EmS228/jumpguard/presentations/FDR_13Jump.pdf

# JumpGuard Final Design Review

Team Members:
Riley Holmes (CpE)
Emily Schwartz (CpE)
Ben Caba (EE)
Trevor Jordan (ME)
John Podgorney (ME)

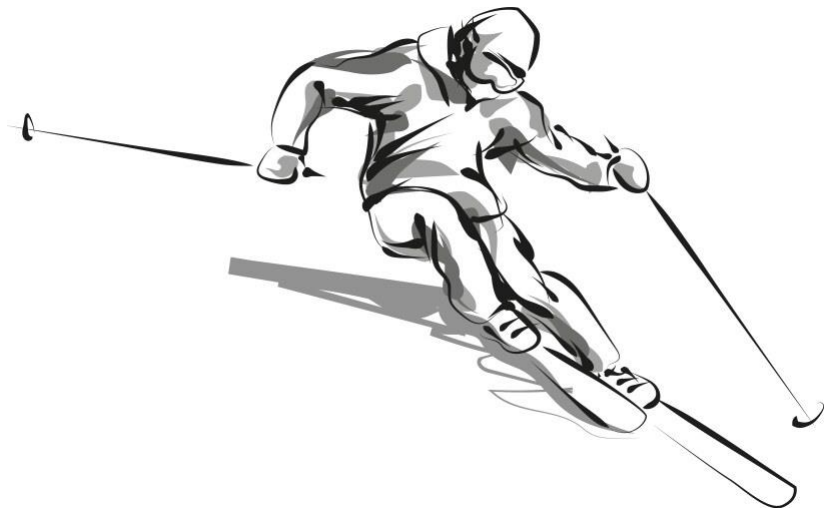
[picture p16: figure]

Clients: Nick Hekker, Kade Borson, Tate Ellinwood, Tristan Tober Advisor: Dr. Kevin Repasky
Date: 4/15/2025

# Problem Statement

Problem Motivation:
Many ski resorts today have terrain parks, which are collections of jumps and obstacles that can be ridden by athletes. Depending on the size of terrain park jumps, athletes can't always see the landing area before committing to the jump. So, if an athlete crashes on the bottom of a larger jump, athletes uphill may not be aware of the risk of collision awaiting them at the bottom of the jump.

Project Description:
A system will be designed to detect when the landing area is clear before notifying the next athlete that it is safe to proceed from the top of the hill.

Objectives:
This system will determine whether the landing area below a jump is clear and then report the status to athletes uphill from the landing area. The system must operate in inclement weather throughout the ski-season. The system will operate on a stand-alone power system to avoid running power lines to the system, which could create unnecessary hazards.

# Necessary Background

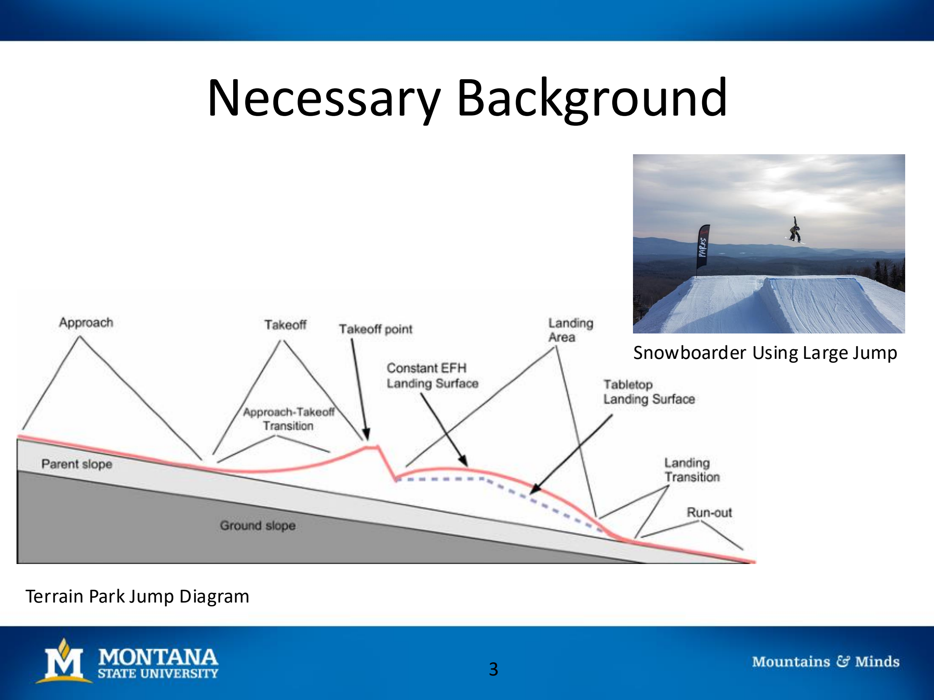
[picture p17: page 3]

Terrain Park Jump Diagram

Snowboarder Using Large Jump

# Project Design Concept

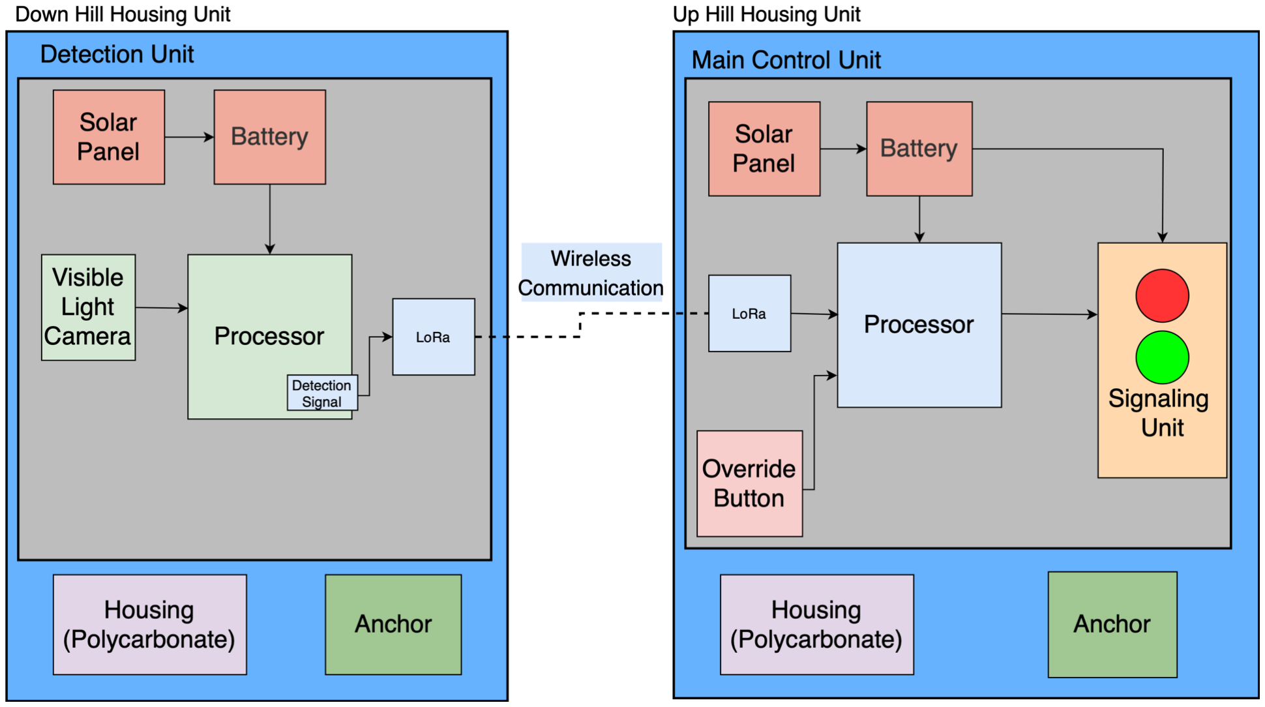
[picture p18: figure]

Conceptual Block Diagram

# System Design Solution

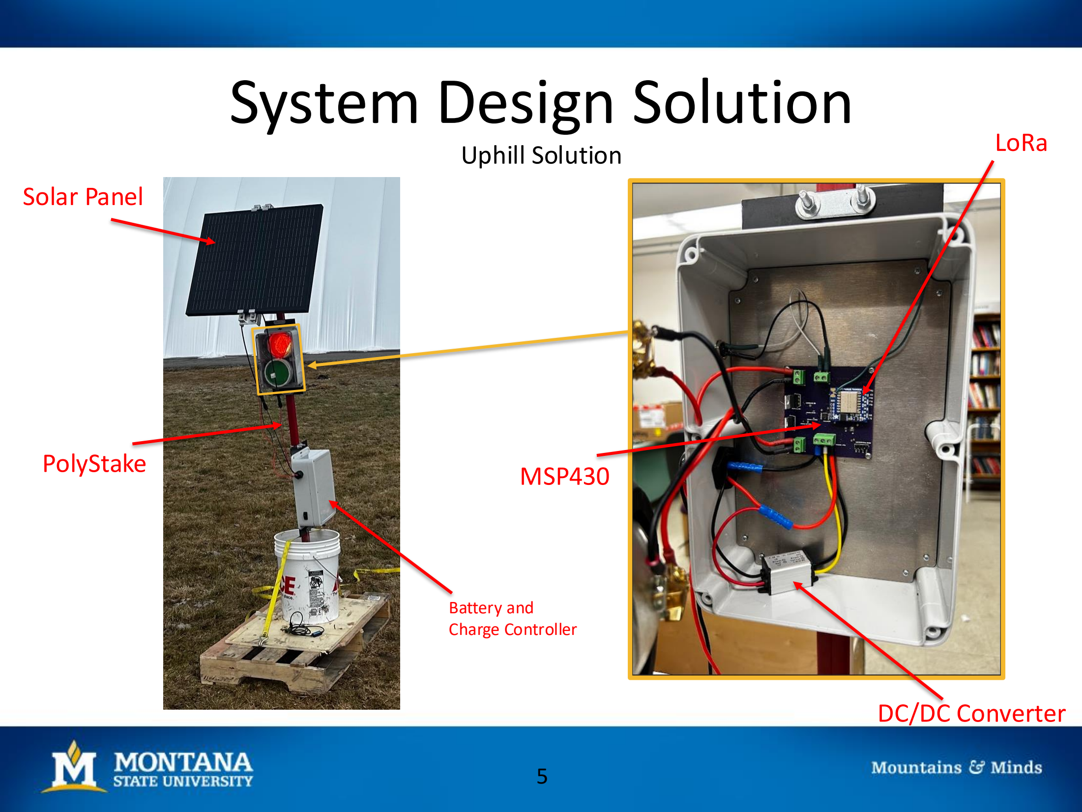
[picture p19: page 5]

Uphill Solution
Solar Panel

Battery and
Charge Controller

PolyStake

LoRa

MSP430

DC/DC Converter

# System Design Solution

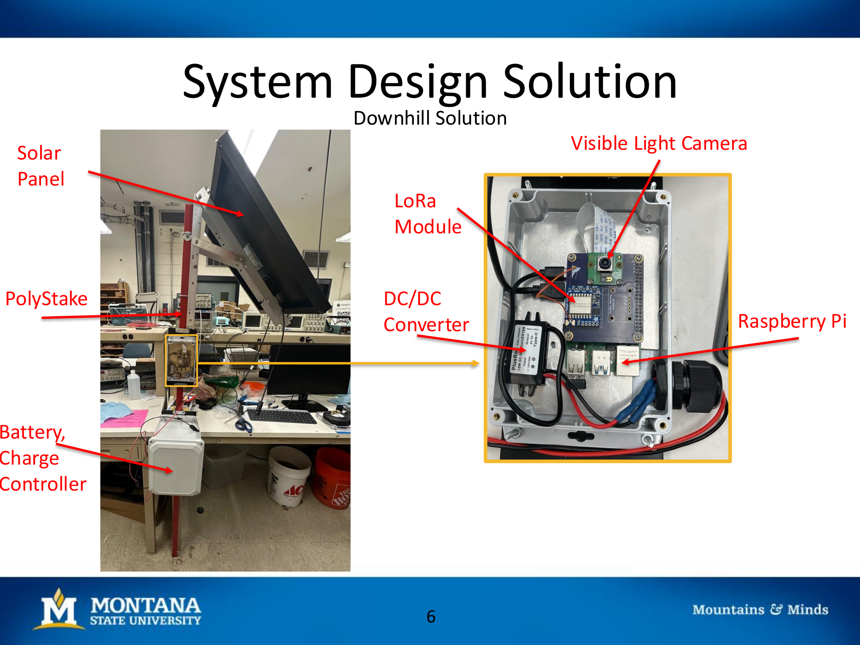
[picture p20: page 6]

Downhill Solution

Battery,
Charge
Controller

Solar
Panel
PolyStake | DC/DC Converter

Visible Light Camera

Raspberry Pi

LoRa
Module

# Design Solution: Uphill Power

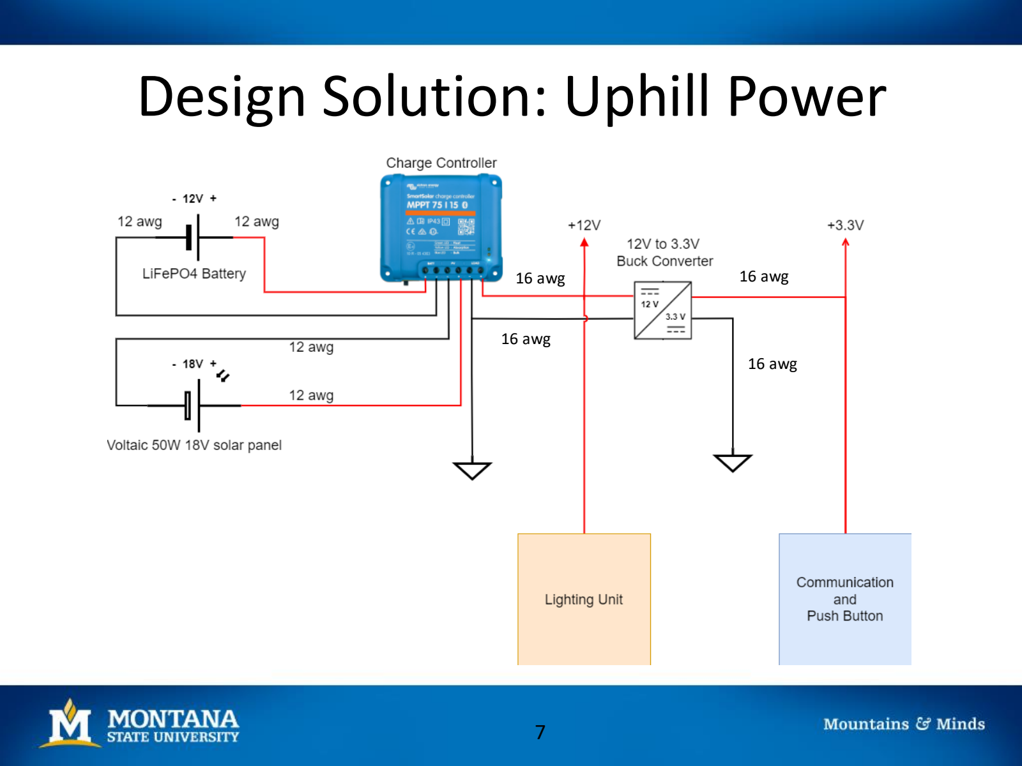
[picture p21: page 7]

16 awg

16 awg

16 awg

16 awg

# Design Solution: Uphill Power

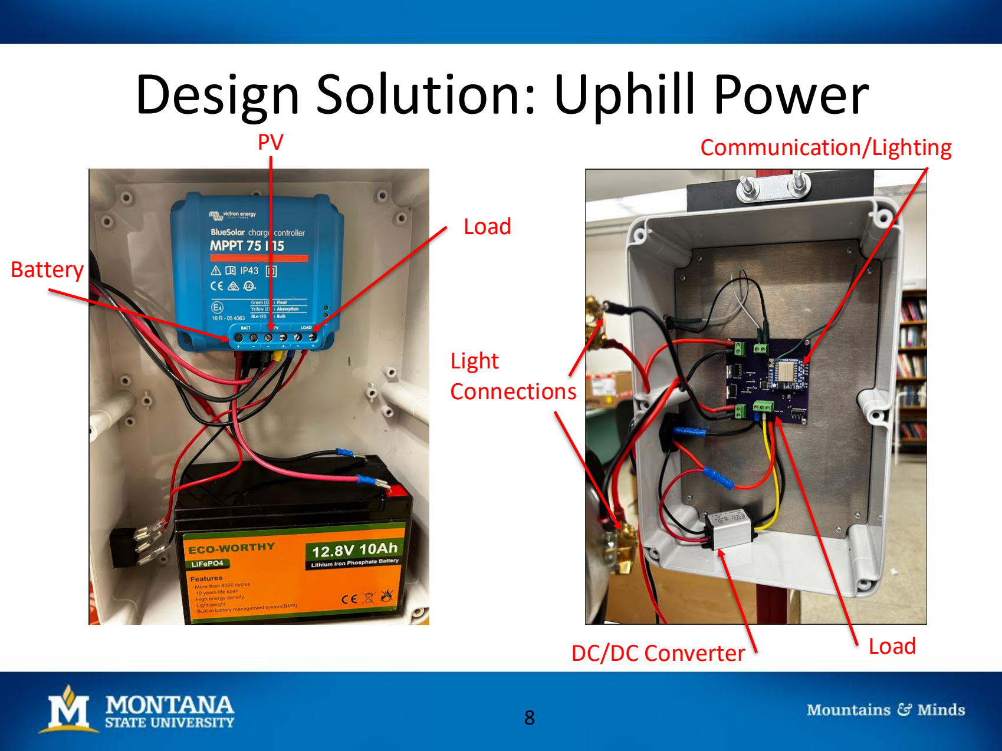
[picture p22: page 8]

Battery

PV

Load

Load

Light
Connections

DC/DC Converter

Communication/Lighting

# System Verification: Power (Spec 3.2.1 – test description)

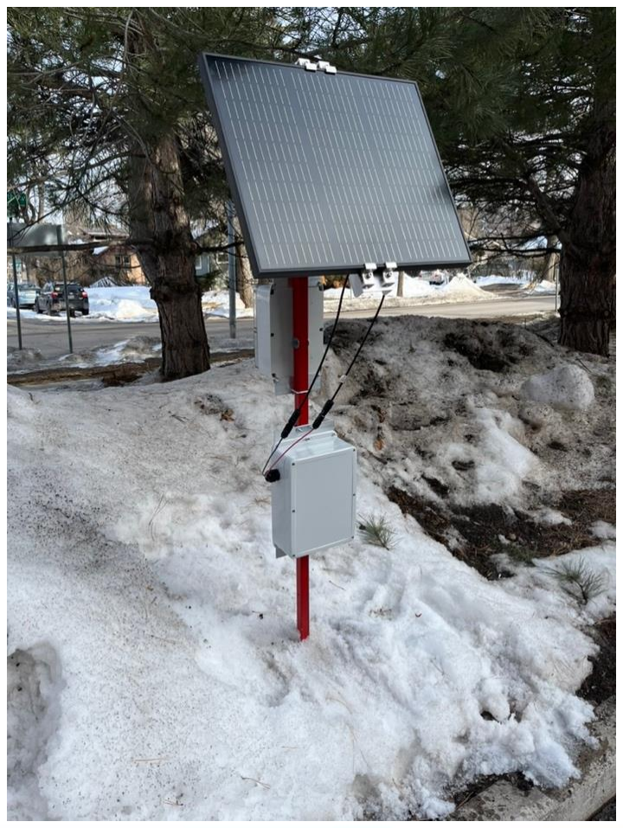
[picture p23: figure]

- Full system assembled
- Run off backup power for one day
- Run with solar panels for one day
- Run off backup power for one day

Spec 3.2.1) Can recharge for a 7-hour operational day with 3.5 hours of peak sunlight

# System Verification: Power (Spec 3.2.1 – test results)

Spec 3.2.1) Can recharge for a 7-hour operational day with 3.5 hours of peak sunlight

Date (mm/dd/yyyy) | Consumption (Wh) | Yield (Wh) | Initial Voltage (V) | Final Voltage (V)
04/09/2024 | 80 | 0 | 13.27 | 13.12
04/10/2024 | 70 | 160 | 13.14 | 13.42
04/11/2024 | 80 | 0 | 13.29* | 13.00

Uphill test results (04/09 – 04/11)

*system was used for additional testing after the 7 hour testing window

# System Verification: Power (Spec 3.2.1 – test results)

Spec 3.2.1) Can recharge for a 7-hour operational day with 3.5 hours of peak sunlight

Solar irradiance data for 04/10/2024 [1]

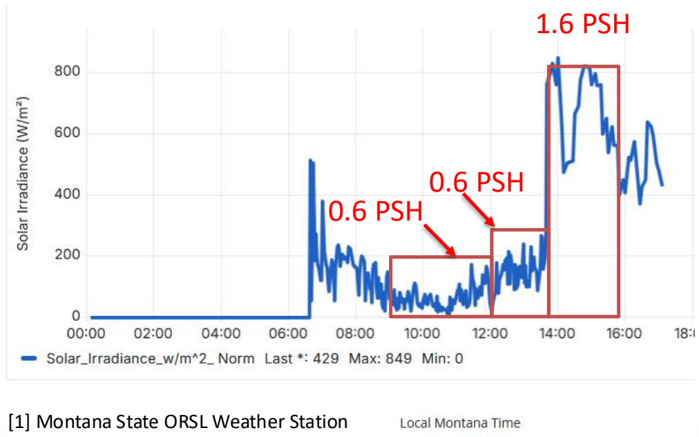
[picture p24: figure]
0.6 PSH; 1.6 PSH; [1] Montana State ORSL Weather Station

PSH for 4/10/2025 =
0.6 + 0.6 + 1.6 = ~2.8 PSH

Testing window: 8:56am-4:00pm

# System Verification: Power (summary)

Req Doc Item | Result | Pass/Fail
Req 3.1 | System operated continuously for 7 operational days | Pass
Spec 3.1.1 | System operated continuously for a 7-hour operational day | Pass
Spec 3.1.2 | Backup power operated for 7 hours | Pass
Req 3.2 | Solar and battery charger both charged the system | Pass
Spec 3.2.1 | Recharged with under 2.8 PSH | Pass
Spec 3.2.2 | Battery charger charged battery under 8 hours | Pass

# Design Solution: Communication

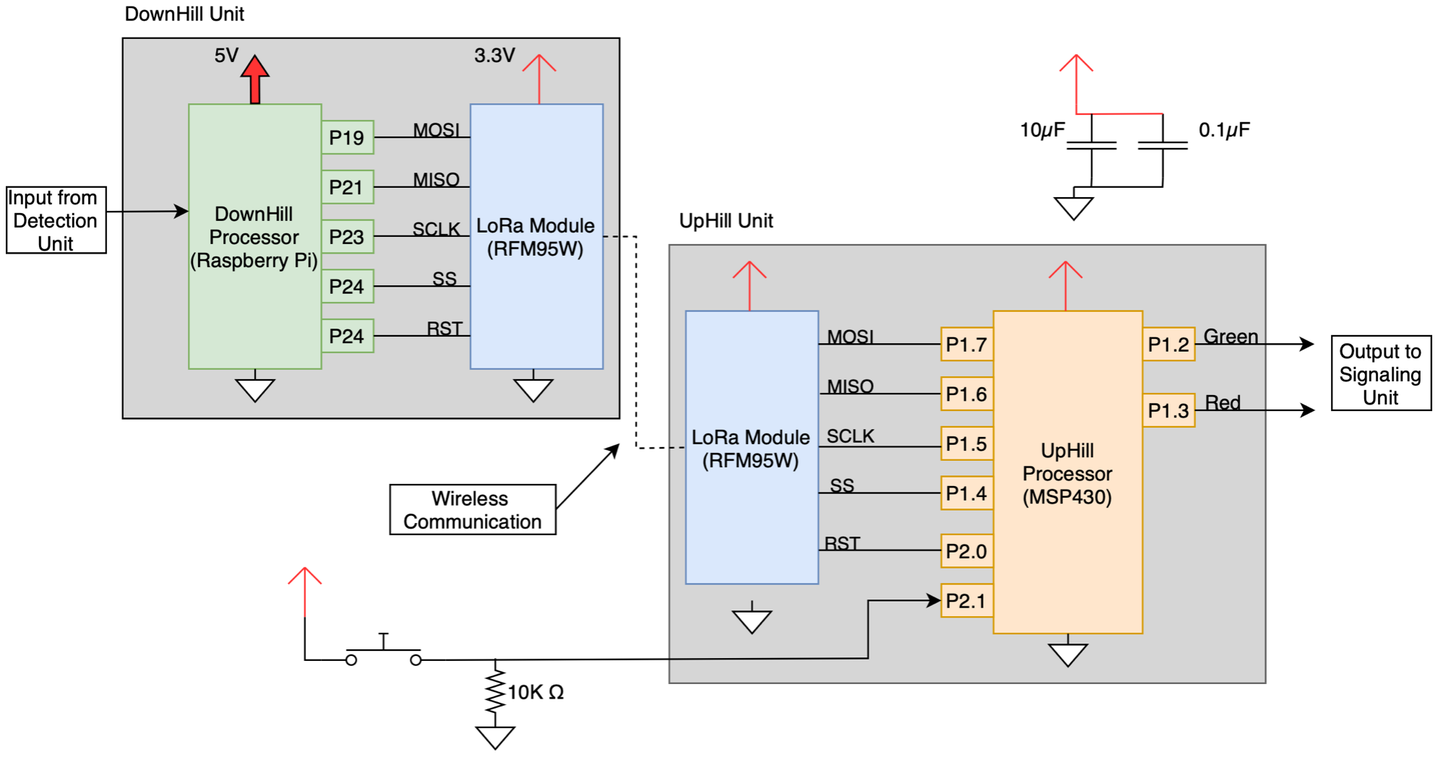
[picture p25: figure]

# System Verification: Communication Setup

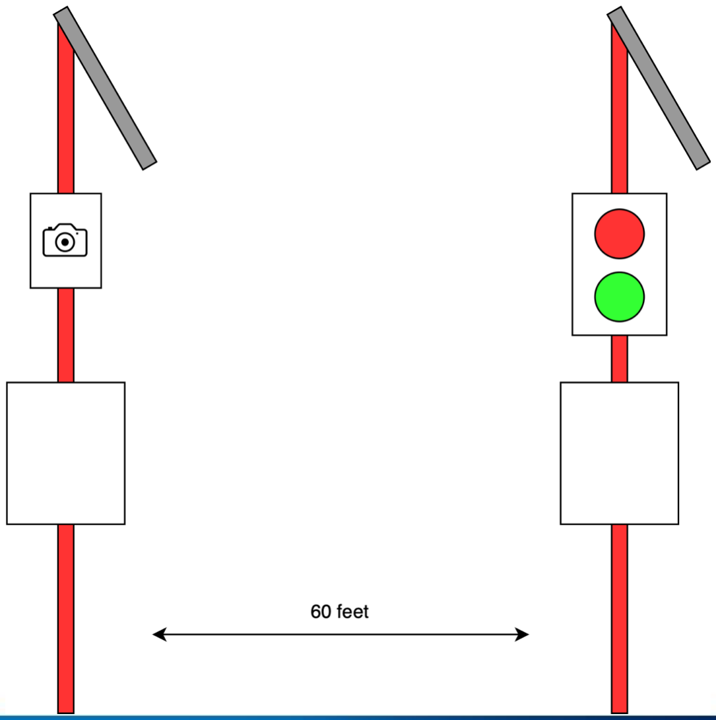
[picture p26: figure]

Req 1.2) System must communicate detection results to uphill athletes.

Spec 1.2.2) Dropout rate of information must be ≤ 2.0%

Spec 1.2.3) Sensors must communicate with signaling unit from a maximum distance of 60 ft away with a direct line of sight

Testing Procedures:
- Tested 20 times throughout a 7-hour period
- Tested for 5 days total
- Camera was covered with paper; green light is expected. When camera is uncovered, red light is expected

# System Verification: Communication Results

Results for day 1:
- 100% communication rate
- 0% dropout rate

Results for all days:
- 100% communication rate
- 0% dropout rate
| Expected Detection Signals | Actual Detection Signals
Test 1: | 1 | 1
Test 2: | 1 | 1
Test 3: | 1 | 1
Test 4: | 1 | 1
Test 5: | 1 | 1*
Test 6: | 1 | 1
Test 7: | 1 | 1
Test 8: | 1 | 1*
Test 9: | 1 | 1
Test 10: | 1 | 1
Test 11: | 1 | 1*
Test 12: | 1 | 1
Test 13: | 1 | 1
Test 14: | 1 | 1
Test 15: | 1 | 1
Test 16: | 1 | 1*
Test 17: | 1 | 1
Test 18: | 1 | 1
Test 19: | 1 | 1
Test 20: | 1 | 1

Testing day 1 – April 6th

*Camera timed out, after a reboot the system operated as expected

0 = lights did not operate as expected
1 = lights operated as
expected (changed from
green to red when camera
was uncovered, then back to green once covered)

Req 1.2) System must communicate detection results to uphill athletes.

Spec 1.2.2) Dropout rate of information must be ≤ 2.0%

Spec 1.2.3) Sensors must communicate with signaling unit from a maximum distance of 60 ft away with a direct line of sight

# Verification: Communication (Summary)

Req Doc Item | Results | Pass
Spec 1.2.1 – Latency from when the sensor triggers, to when the signaling unit triggers, must be ≤ 0.5s | Maximum Latency of 110 ms | Pass
Spec 1.3.3 – Latency of the lights changing states after a signal is received must be ≤ 0.5s | Refer to spec 1.2.1 results | Pass
Spec 1.3.4 – Must have a manual override to send the system to the “stop” state in case of emergencies | Entered ”Stop” mode 20/20 times | Pass

# Design Solution: Detection

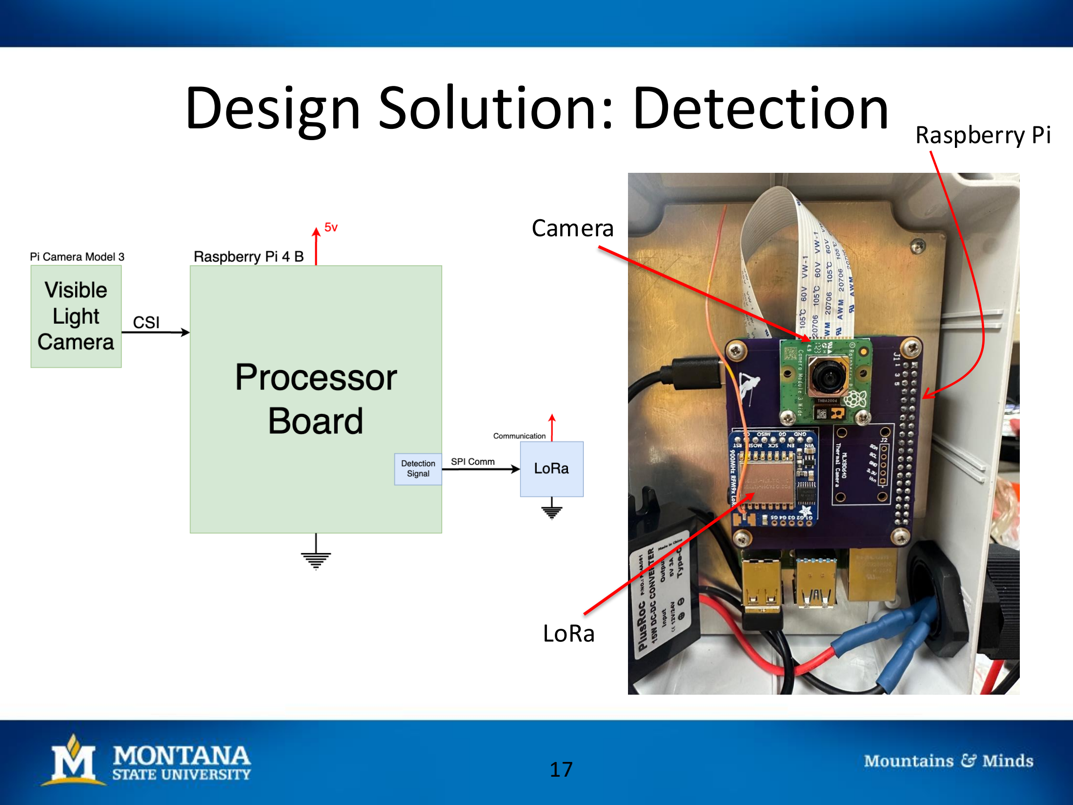
[picture p27: page 17]

LoRa

Camera

Raspberry Pi

# System Verification: Detection Setup

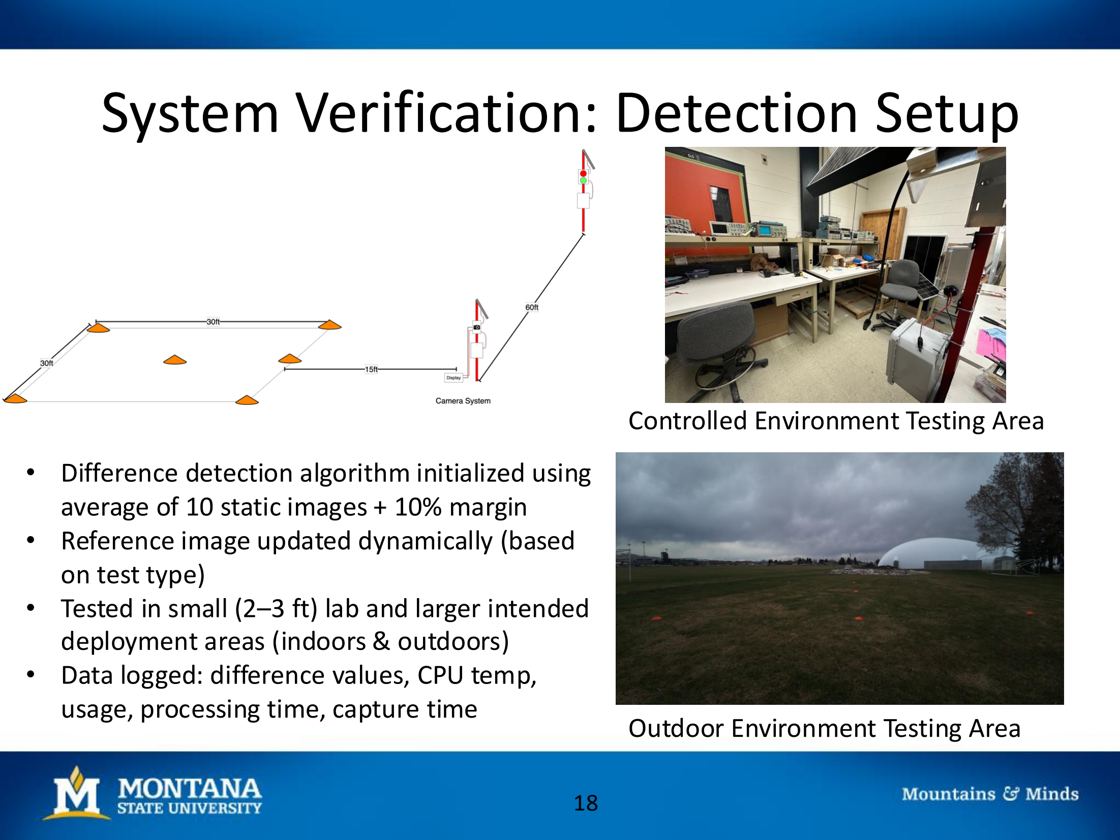
[picture p28: page 18]

Controlled Environment Testing Area

Outdoor Environment Testing Area

- Difference detection algorithm initialized using average of 10 static images + 10% margin
- Reference image updated dynamically (based on test type)
- Tested in small (2–3 ft) lab and larger intended deployment areas (indoors & outdoors)
- Data logged: difference values, CPU temp, usage, processing time, capture time

## System Verification: Detection Results (Controlled Test)

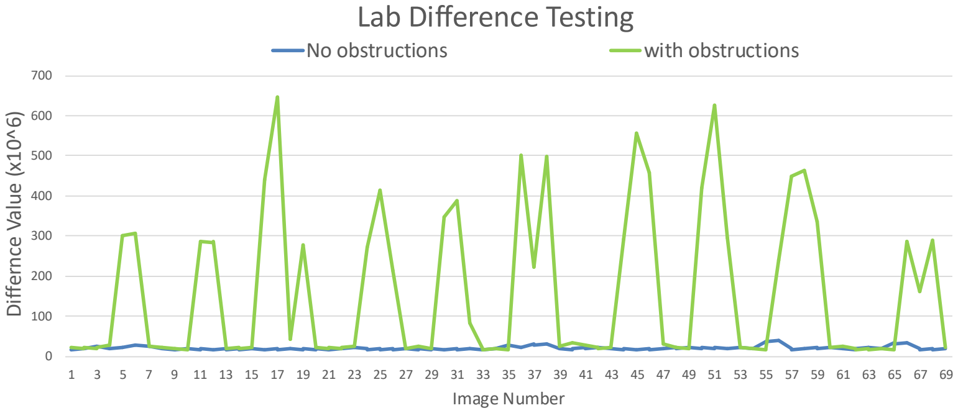
[picture p29: figure]
Differnce Value (x10^6); Image Number; Lab Difference Testing; No obstructions; with obstructions

- Detection was 100% accurate in limited space (~2–3 ft)
- Threshold logic performed consistently
- Difference values remained consistent: ~20-30M
- System remained responsive and CPU/memory usage stable
- Confirms algorithmic viability in stable, small-scale settings
1 | 3 | 5 | 7 | 9 11 13 15 17 19 21 23 25 27 29 31 33 35 37 39 41 43 45 47 49 51 53 55 57 59 61 63 65 67 69

## System Verification: Detection Results (Outdoor Test)

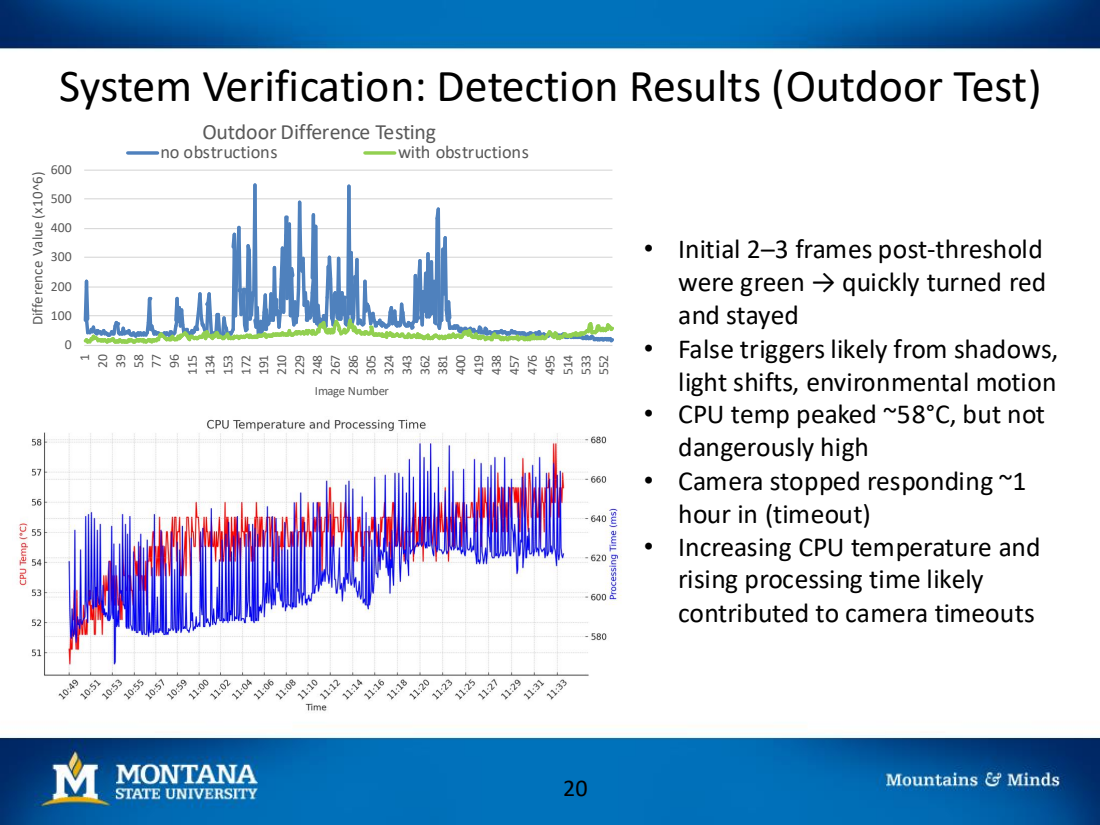
[picture p30: page 20]
Difference Value (x10^6); Image Number; no obstructions; with obstructions

Outdoor Difference Testing

• Initial 2–3 frames post-threshold
were green → quickly turned red
and stayed
• False triggers likely from shadows,

• CPU temp peaked ~58°C, but not
dangerously high
• Camera stopped responding ~1
hour in (timeout)
• Increasing CPU temperature and
rising processing time likely
contributed to camera timeouts

light shifts, environmental motion

## System Verification: Detection Summary & Lessons Learned

- What Worked: Algorithm logic, adaptive thresholding, thermal performance
- What didn’t Work: Environmental adaptation, reference handling, long-term stability
- To be added in the Future: Add thermal camera, region filtering, watchdog for camera recovery

Lessons + Next Steps

Metric | Small-Scale Lab | Full-Area Setup | Outdoor
Accuracy | 100% | Inconsistent | Unusable
Threshold Stability | High | Low | Very Low
CPU/Temp | Stable | Stable | High Load
Behavior | Reliable | Detection Drift | Crashes/Freezes

Req Doc Item | Results | Pass
Req 1.1: System must detect when the landing area is clear | In controlled smaller environments the system can detect a clear detection area | Fail at system level
Spec 1.1.1: Detection system must be able to detect athletes within a 30x30 ft area within the landing area | Environmental noise prevents detection over larger areas | Pass at Spec level, fail at system level
Spec 1.1.2: Must have ≥ 95% detection rate | In controlled environments the system can detect a clear landing area. | Pass at Spec level, fail at system level

# System Verification: Detection Summary

*Based on image difference noise behavior shown in Slide 3

# Design Solution: Mounting and Anchoring

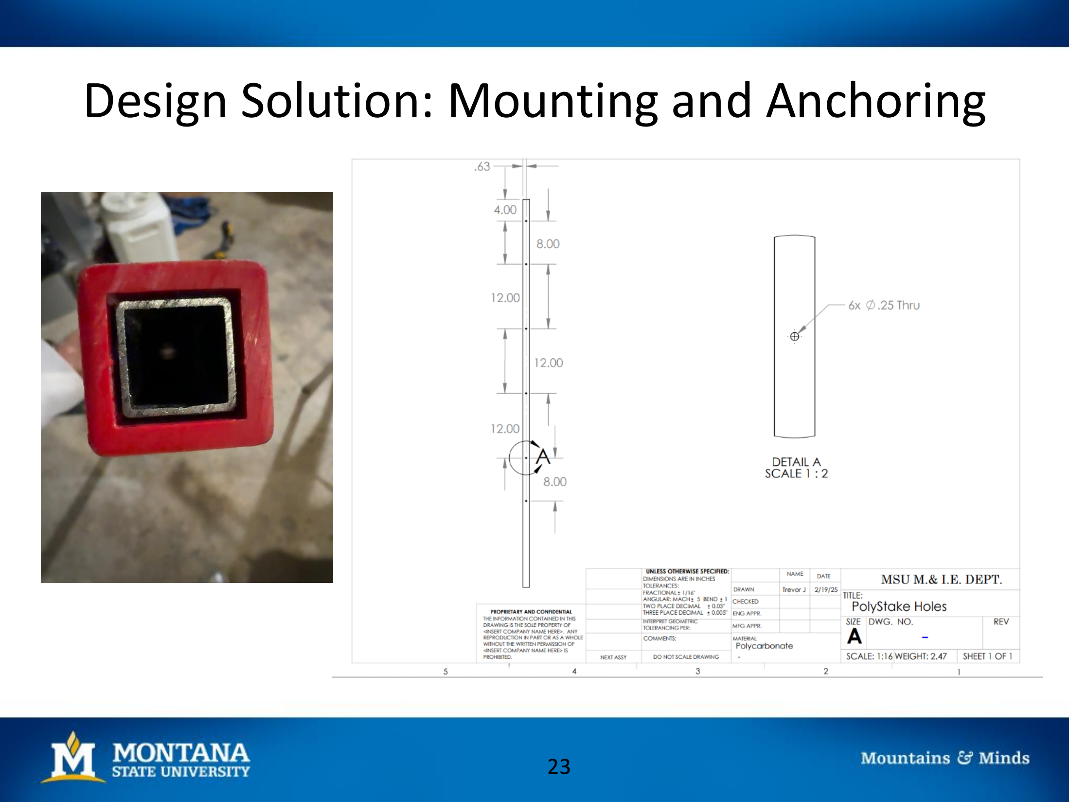
[picture p31: page 23]

# System Verification: Mounting and Anchoring Setup

Req 2.1) Must have housing material capable of protecting electronics while ensuring operation in varying weather conditions

Spec 2.1.2: Must be able to operate in winds up to 20 mph

Testing Procedure:
- System fully set up outdoors daily for 6 days with 20 random checks for functionality
- Wind speed, temperature, and overall conditions were recorded during each detection test
- Sand Bucket used to simulate mounting in snow

# System Verification: Mounting and Anchoring Results

Test # | Expected Signal | Actual Signal | Time | Weather | Light Visible? | Wind | Temp
6 | 1 | 1 | 10:50 AM | Light Hail | Yes | 1.21 mph | 46.8°F
7 | 1 | 1 | 11:05 AM | Light Hail | Yes | 1.13 mph | 47°F
18 | 1 | 1 | 3:15 PM | Sunny/ Cloudy | Yes | 23 mph | 54°F
19 | 1 | 1 | 3:30 PM | Sunny/ Cloudy | Yes | 24 | 54°F

Key Points of data from Thursday, April 10

# System Verification: Anchoring and Mounting

- Spec 2.1.2 Verified
The system was exposed to wind conditions up to and above 20 mph. All components remained fully functional, meeting the design specification.
- Weather Resistance Demonstrated
During testing, the system withstood not only wind but also rain and hail. No damage or performance issues were observed, confirming durability under various weather conditions.
- 0°F Temperature Specification Partially Verified
Full-system cold testing at 0°F was not possible due to the lack of a controlled environment and spring weather. However, the housings were tested separately and passed under low-temperature conditions.

# Design Solution: Housing

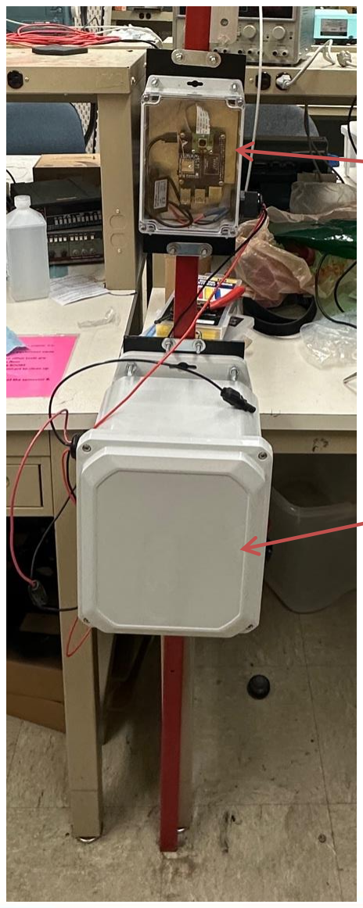
[picture p32: figure]

Detection Unit

Detection Housing

Battery Housing

# System Verification: Housing Setup

Req 2.1) Must have housing material capable of protecting electronics while ensuring operation in varying weather conditions

Test Method Summary:
Water was sprayed on the housings for 4 minutes from all sides using a hose / similar source, then internal elements were inspected for moisture and electronics functionality.

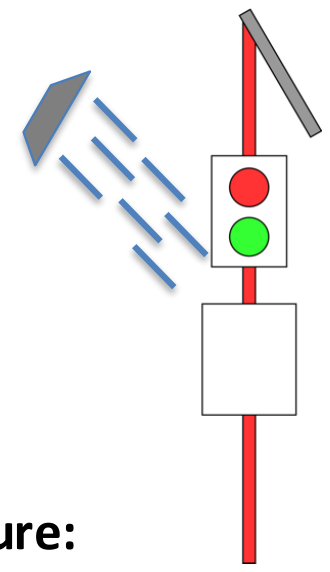
[picture p33: figure]

Testing Procedure:

1. Absorbent paper was placed in all housing at seams and cable entries
2. Housings were sprayed at medium pressure from the top, front, left, and right for 1 minute each
3. Housings were dried off, opened and inspected for water ingress

# System Verification: Housing Results

Housing Unit | Water Present? | Paper Damp? | Leak Location? | Electronics Functional?
Signaling | N | Y | Cable Gland | Y
Uphill Battery | N | N | N/A | Y
Detection | N | Y | Cable Gland | Y
Downhill Battery | N | N | N/A | Y
- Since slight water ingress was present, the system cannot confidently pass Req 2.1
- Moving forward, a simple fix can be made by getting some larger rubber plugs or silicon-based sealant for the unused spots in the cable glands

Pass/Fail Criteria:
PASS: No visible internal water, dry paper/sensors, electronics working normally.

FAIL: Any sign of internal water, malfunctioning components, or wet absorbent indicators.

# System Verification: Objective 2

Req Doc item | Result | Pass
Spec 2.1.1 | Humidity remained below 80% at 0° | Spec passes, System N/A
Spec 2.1.2 | System operated in wind over 20mph | Pass
Spec 2.1.3 | Unable to test | N/A
Req 2.1 | Slight water ingress, electronics protected | Fail – Can be fixed with some quick changes to sealing
Spec 2.2.1 | Light visible from 180ft | Pass
Spec 2.2.2 | Green: 1317 Lumens Red: 1626 Lumens | Pass
Spec 2.2.3 | Housings fully adjustable along stake up to 5ft individually | Spec pass, System fail – Can be fixed with a longer stake/extension
Req 2.2 | Lights produce bright and visible light from 30ft away | Pass

Spec 2.1.1) Must be able to withstand and function in temperatures ≥ 0°F
Spec 2.1.3) System is not meant to operate in visibility lower than 30 ft or when the terrain park is not operational Spec 2.2.3) Adjustable between 0 - 5 feet with height increments by ± 6” for every adjustment

# Project Status

- Working to complete Final Project Report, and create User’s manual for Sponsors - Communicating with the Sponsors for Project Handoff - Design Fair Poster is nearly complete - Preparing System to display during Design Fair - Req 2.1 will be tested again before Design Fair with improved sealing in the upper units’ glands

# Project Budget

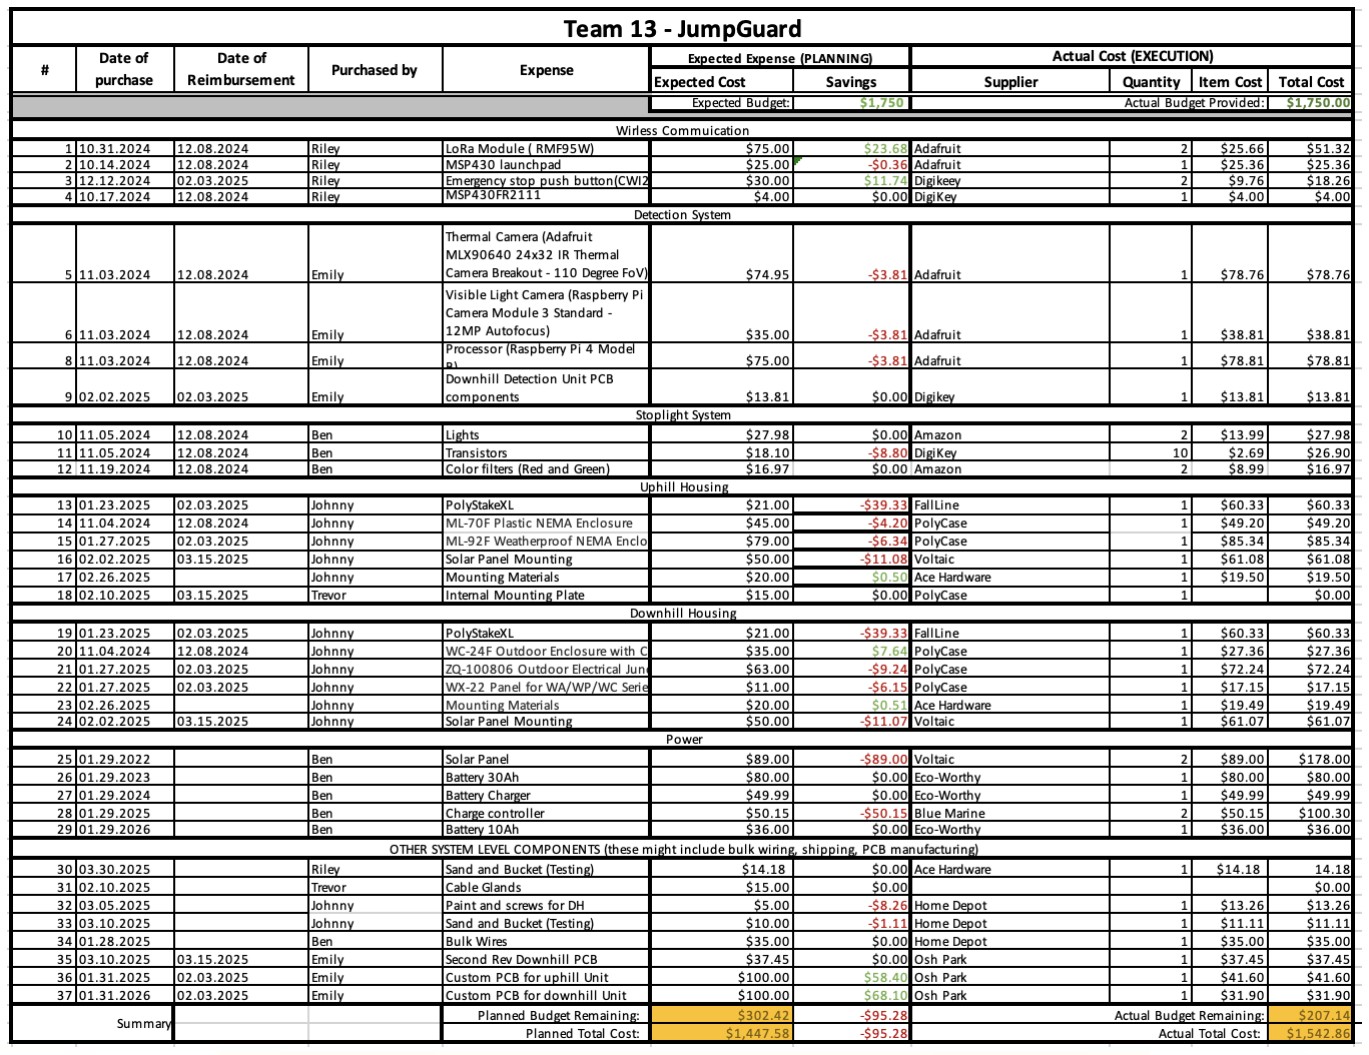
[picture p34: figure]

# Bill of Materials

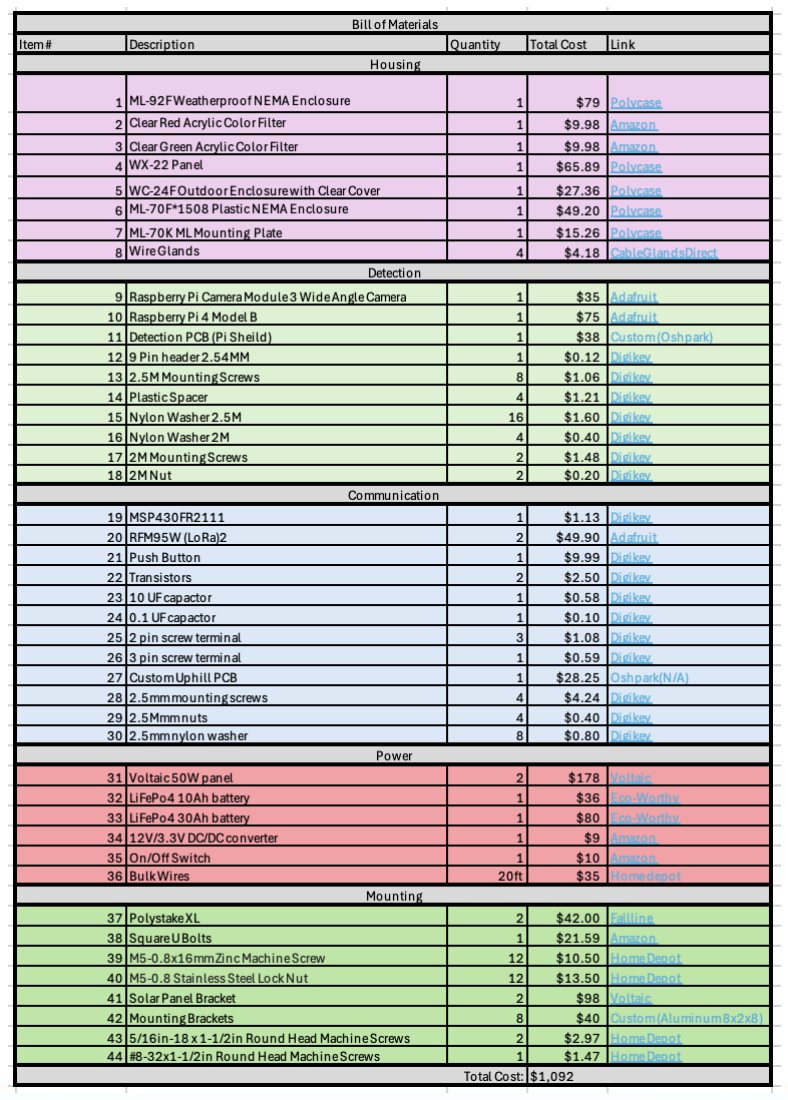
[picture p35: figure]

# Summary

- This project integrated electrical, computer, and mechanical subsystems into a unified object detection system. While the system worked reliably in a controlled lab setting, real-world testing revealed challenges with environmental variability and system stability.
- We gained valuable experience in applying the full engineering design process—designing, testing, analyzing results, and iterating based on performance. Each team member contributed to this effort:
– Electrical Engineer: Power and lighting subsystem
– Computer Engineers: Image processing and LoRa communication
– Mechanical Engineers: Stake and protective hardware design
- Although not all detection goals were met in the field, the project gave us meaningful hands-on experience in cross-disciplinary collaboration and real-world system design, and a successful proof of concept and prototype was designed for the sponsors to move into the next stage of the design process.

# QUESTIONS?

# Design Solution: Downhill Power System

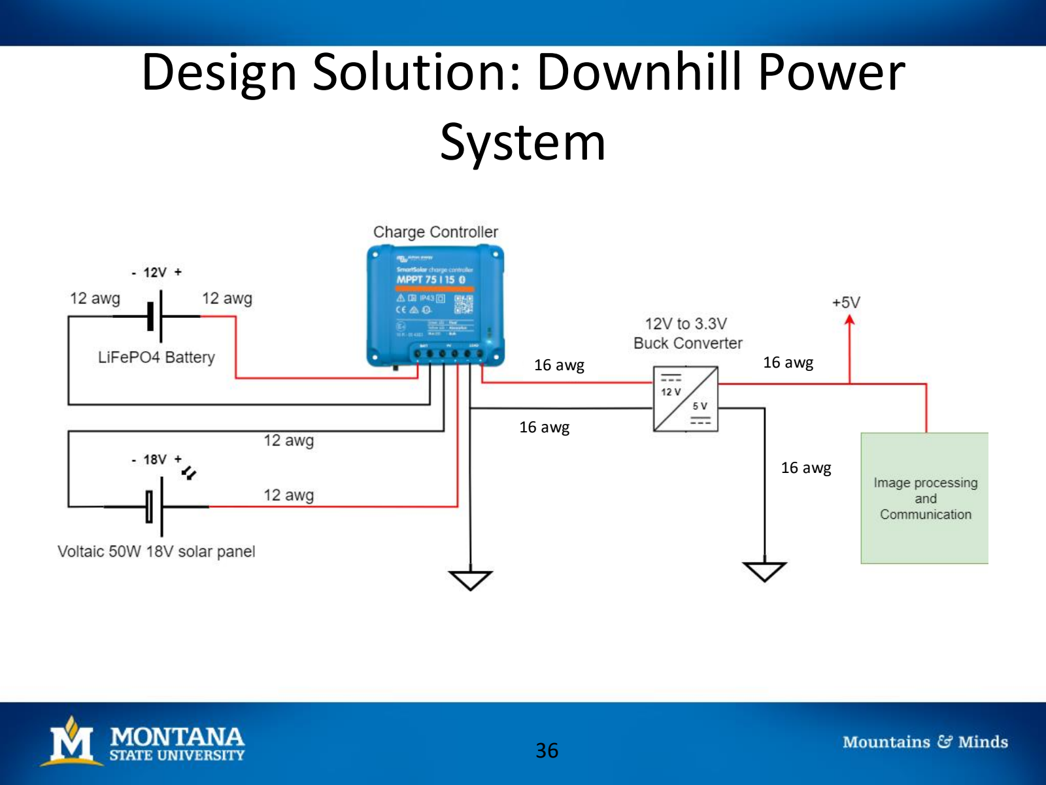
[picture p36: page 36]

16 awg

16 awg

16 awg

16 awg

# Design Solution: Downhill Power System

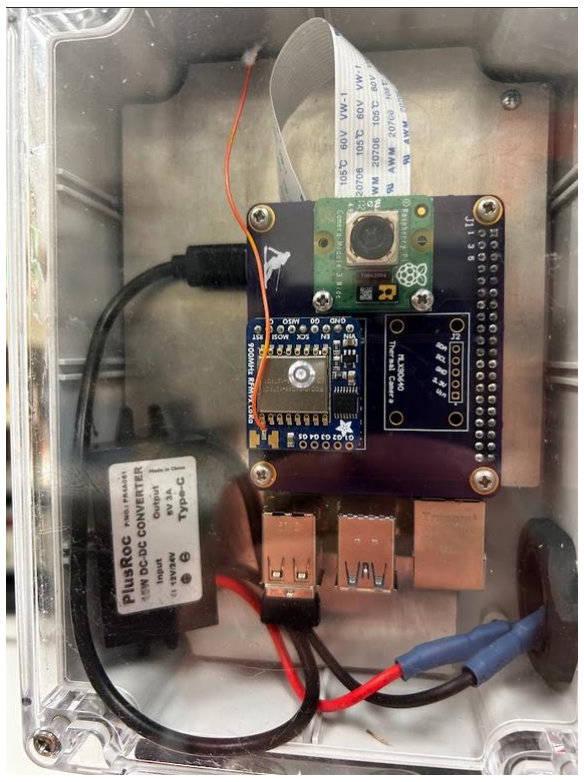
[picture p37: figure]

# System Verification: Power system test results (uphill)

Date | Yield(Wh) | Consumption (Wh) | Max. PV power(W) | Max. PV voltage(V) | Min. battery voltage(V) | Max. battery voltage(V)
4/11/2025 | 0 | 80 | 0 | 0.01 | 12.87 | 13.43
4/10/2025 | 160 | 70 | 54 | 19.62 | 13.15 | 14.21
4/9/2025 | 0 | 80 | 0 | 0 | 13.12 | 13.27
4/8/2025 | 50 | 80 | 50 | 19.01 | 12.71 | 13.35
4/7/2025 | 60 | 70 | 35 | 20.72 | 13.19 | 14.23
4/6/2025 | 0 | 70 | 0 | 0.01 | 12.97 | 13.8

# System Verification: Power system test results (downhill)

Date | Yield(Wh) | Consumption (Wh) | Max. PV power(W) | Max. PV voltage(V) | Min. battery voltage(V) | Max. battery voltage(V)
4/11/2025 | 0 | 40 | 0 | 0.01 | 13.24 | 13.39
4/10/2025 | 70 | 40 | 38 | 19.74 | 13.25 | 14.22
4/9/2025 | 0 | 30 | 0 | 0.01 | 13.24 | 13.39
4/8/2025 | 40 | 30 | 57 | 20.59 | 13.26 | 14.22
4/7/2025 | 50 | 30 | 36 | 18.19 | 13.28 | 13.49
4/6/2025 | 0 | 30 | 0 | 0.01 | 13.25 | 13.31

# System Verification: Mounting and Anchoring

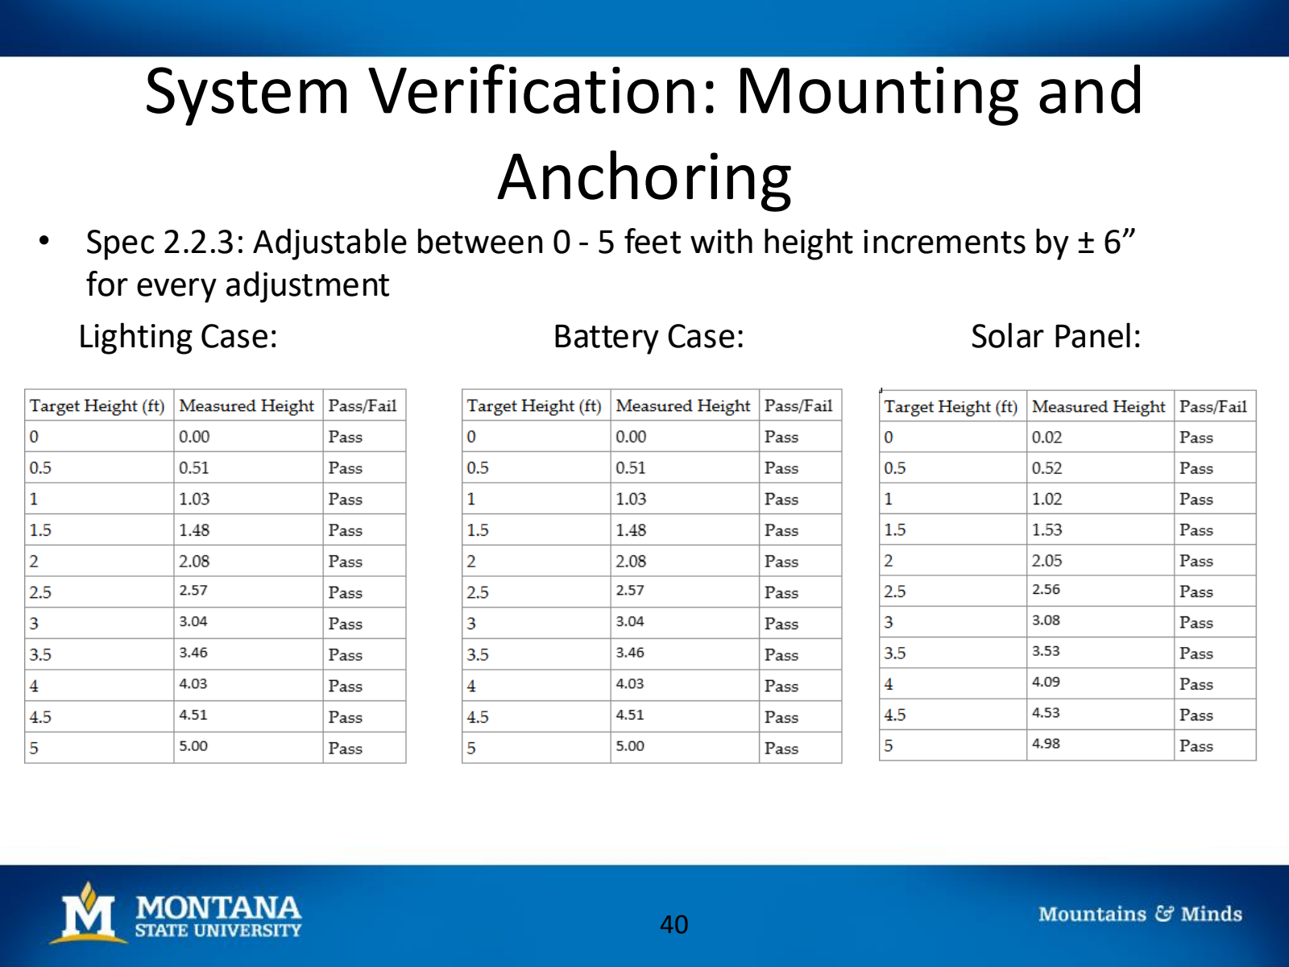
[picture p38: page 40]

- Spec 2.2.3: Adjustable between 0 - 5 feet with height increments by ± 6” for every adjustment
Lighting Case: | Battery Case: | Solar Panel:

# System Verification: Detection Data

## Indoor Full Area Testing

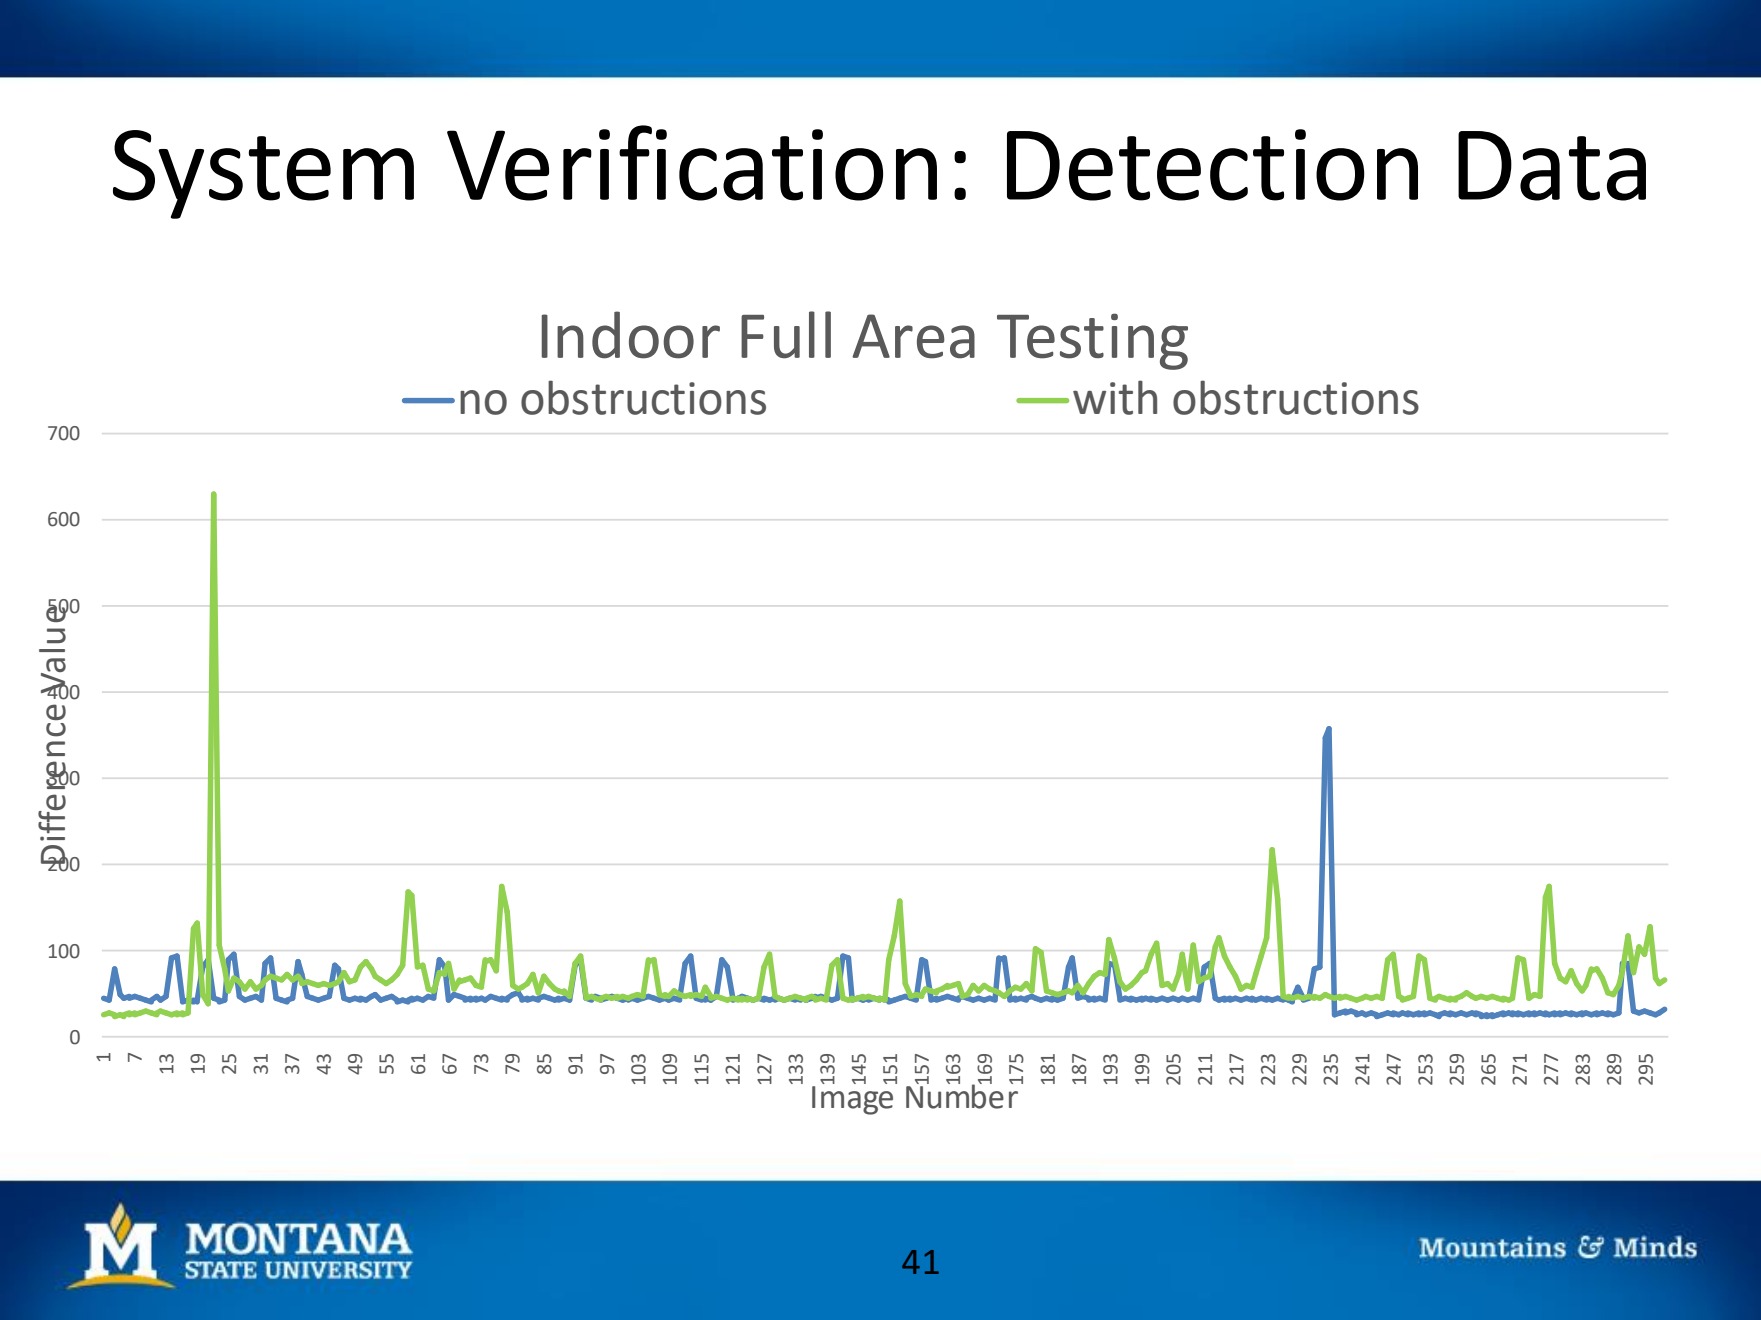
[picture p39: page 41]
Difference Value; Image Number; no obstructions; with obstructions

# Day 1 System Testing Data

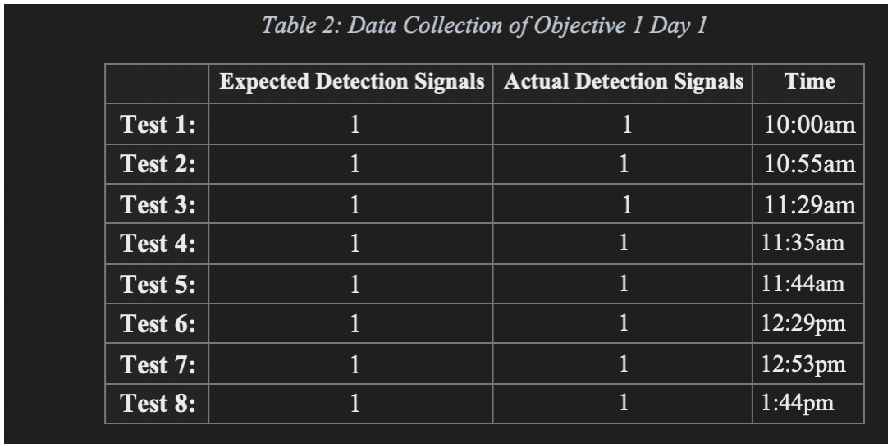
[picture p40: figure]

# Day 2 System Testing Data

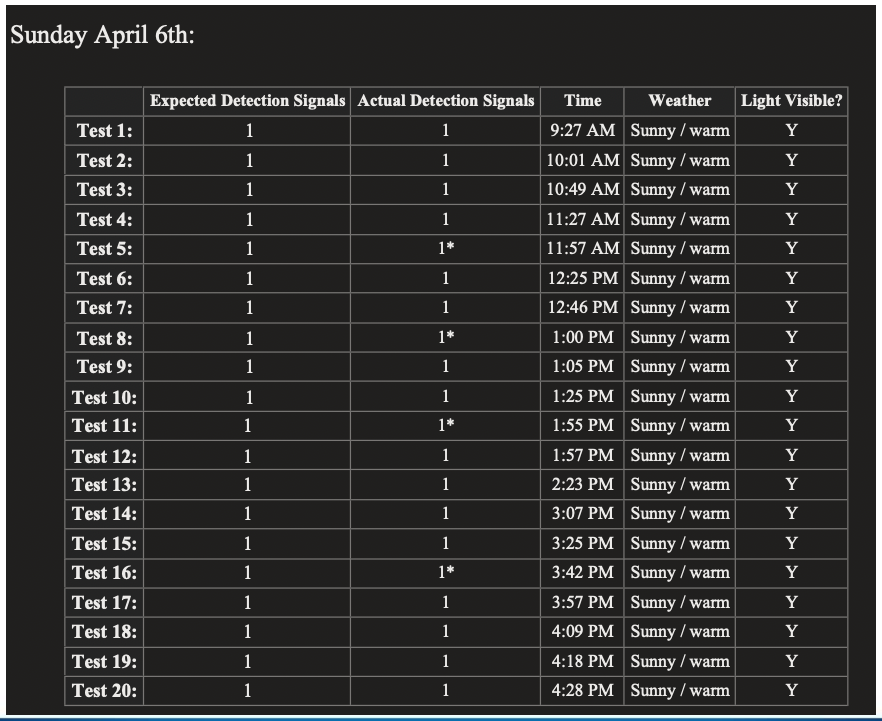
[picture p41: figure]

# Day 3 System Testing Data

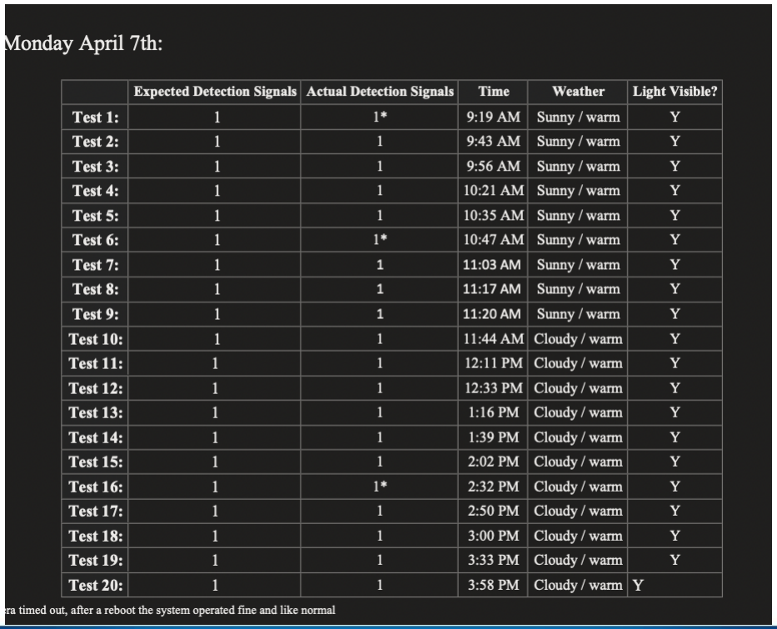
[picture p42: figure]

# Day 4 System Testing Data

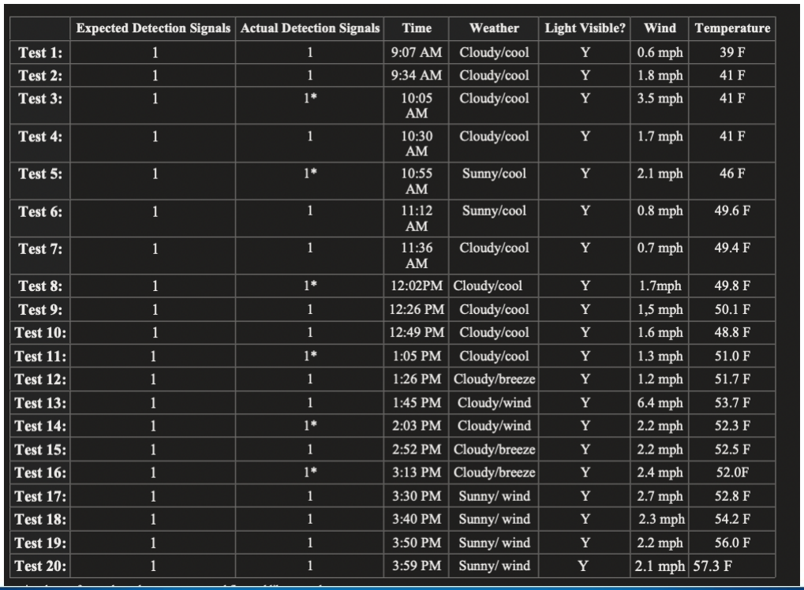
[picture p43: figure]

# Day 5 System Testing Data

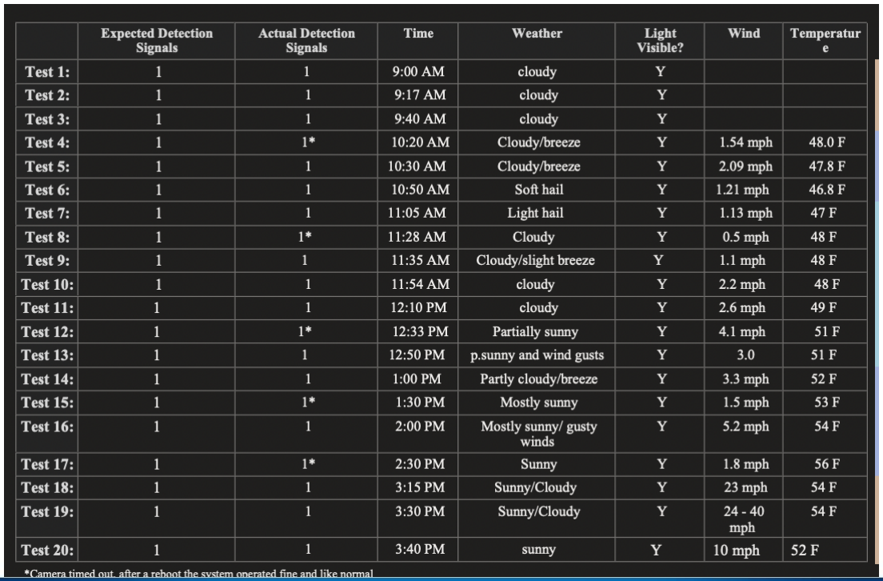
[picture p44: figure]

# Day 6 System Testing Data

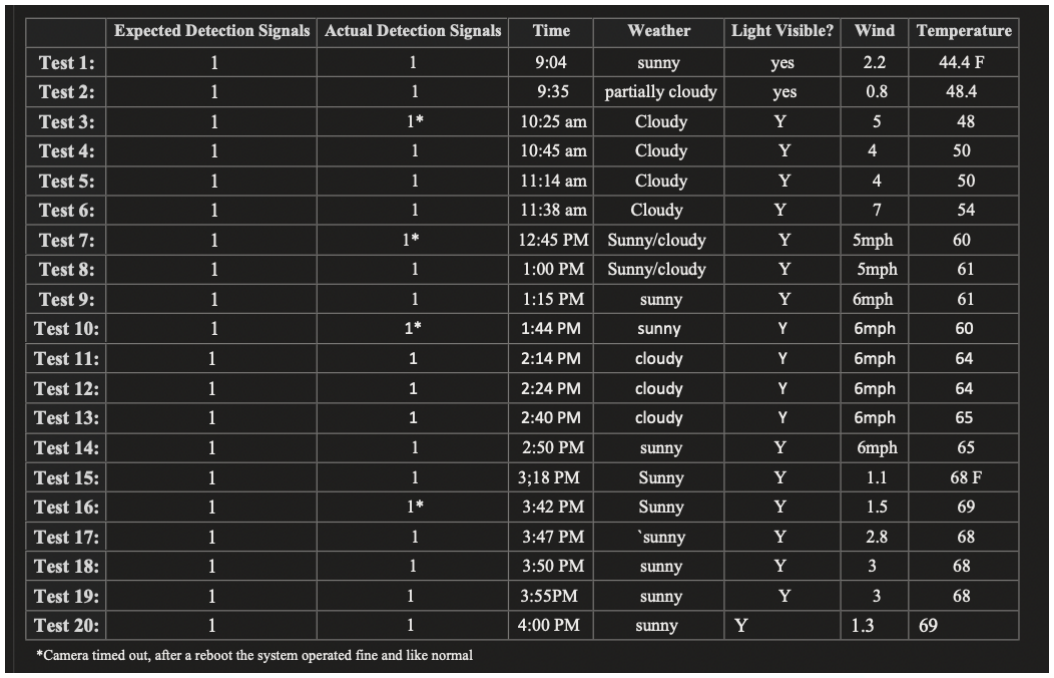
[picture p45: figure]

Objective 1: Determine whether the landing area below a jump is clear,

### and then report the status to athletes uphill from the landing area

Req 1.1) System must detect when the landing area is clear
Spec 1.1.1) Detection system must be able to detect athletes within a 30x30 ft area within the landing area
Spec 1.1.2) Must have ≥ 95% detection rate
Req 1.2) System must communicate detection results to uphill athletes
Spec 1.2.1) Latency from when the sensor triggers, to when the signaling unit triggers, must be ≤ 0.5s
Spec 1.2.2) Dropout rate of information must be ≤ 2%
Spec 1.2.3) Sensors must communicate with signaling unit from a maximum distance of 60 ft away with a direct line of sight
Req 1.3) System must notify the next athlete it is safe to proceed
Spec 1.3.1) Signal must produce a green light when the landing area is clear
Spec 1.3.2) Signal must produce a red light when the landing area is not clear
Spec 1.3.3) The latency of the light changing states after a signal is received must be ≤ 0.5 seconds
Spec 1.3.4) Must have a manual override to send the system to the “stop” state in case of emergencies or other events

## Objective 2: The system must operate in inclement weather throughout the months of December through April

Req 2.1) Must have housing material capable of protecting electronics while ensuring operation in varying weather conditions
Spec 2.1.1) Must be able to withstand and function in temperatures ≥ 0°F Spec 2.1.2) Must be able to operate in winds up to 20 mph
Spec 2.1.3) System is not meant to operate in visibility lower than 30 ft or when the terrain park is not operational
Req 2.2) Signaling Unit must be visible to athletes in varying weather conditions Spec 2.2.1) Must be able to see signaling unit from 30 ft away uphill
Spec 2.2.2) Lights on the signaling unit must produce at least 1000 Lumens Spec 2.2.3) Adjustable between 0 - 5 feet with height increments by ± 6” for every adjustment

### Objective 3: The system will operate on a standalone power system to avoid running power lines to the system which could create unnecessary hazards

Req 3.1) Power source must be reliable in varying winter conditions
Spec 3.1.1) Must operate continuously for 7 hours
Spec 3.1.2) Must have sufficient backup power to operate normally for 7 operational hours
Req 3.2) The system must have the ability to recharge both primary and secondary power sources
Spec 3.2.1) Can recharge for a 7 hour operational day with 3.5 hours of peak sunlight
Spec 3.2.2) Backup power can be recharged through an external source in 8 hours for the system to operate for 7 operational hours
