EmS228/jumpguard/presentations/PDR_13Jump.pdf

# JumpGuard Preliminary Design Review

Team Members:
Riley Holmes (CpE)
Emily Schwartz (CpE)
Ben Caba (EE)
Trevor Jordan (ME)
John Podgorney (ME)


Clients: Nick Hekker, Kade Borson, Tate Ellinwood, Tristan Tober Advisor: Dr. Kevin Repasky
Date: 10/31/2024

# Problem Statement

Problem Motivation:
Many ski resorts today have terrain parks, which are collections of jumps and obstacles that can be ridden by athletes. Depending on the size of terrain park jumps, athletes can't always see the landing area before committing to the jump. So, if an athlete crashes on the bottom of a larger jump, athletes uphill may not be aware of the risk of collision awaiting them at the bottom of the jump.

Project Description:
A system will be designed to detect when the landing area is clear before notifying the next athlete that it is safe to proceed from the top of the hill.

Objectives:
This system will determine whether the landing area below a jump is clear, and then report the status to athletes uphill from the landing area. The system must operate in inclement weather throughout the ski-season. The system will operate on a stand-alone power system to avoid running power lines to the system, which could create unnecessary hazards.

# Necessary Background

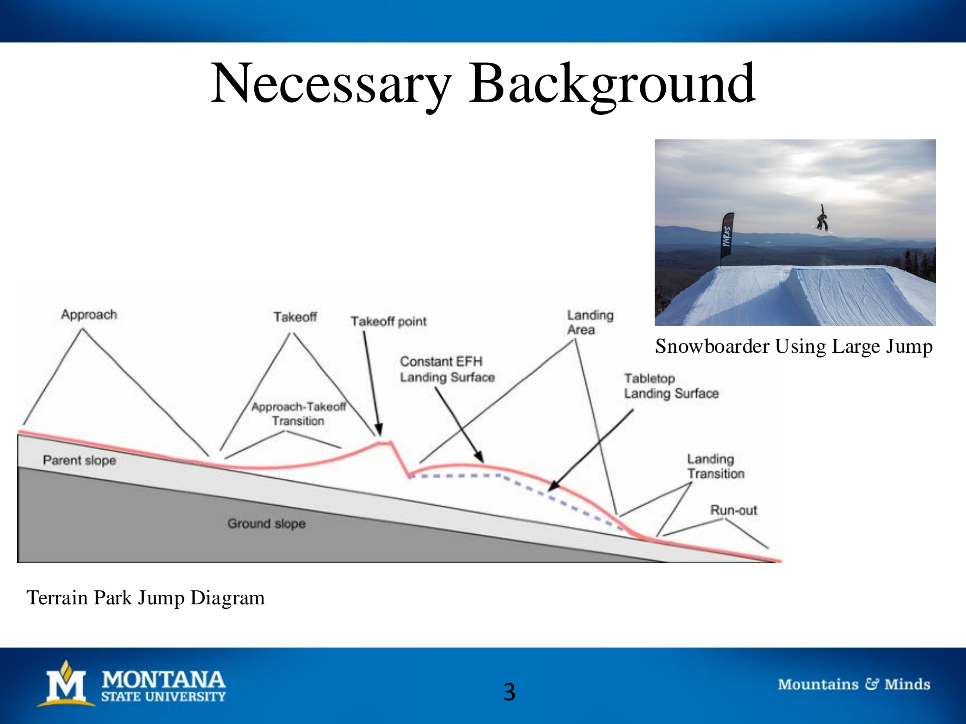
[picture p46: page 3]

Terrain Park Jump Diagram

Snowboarder Using Large Jump

# Project Design Concept

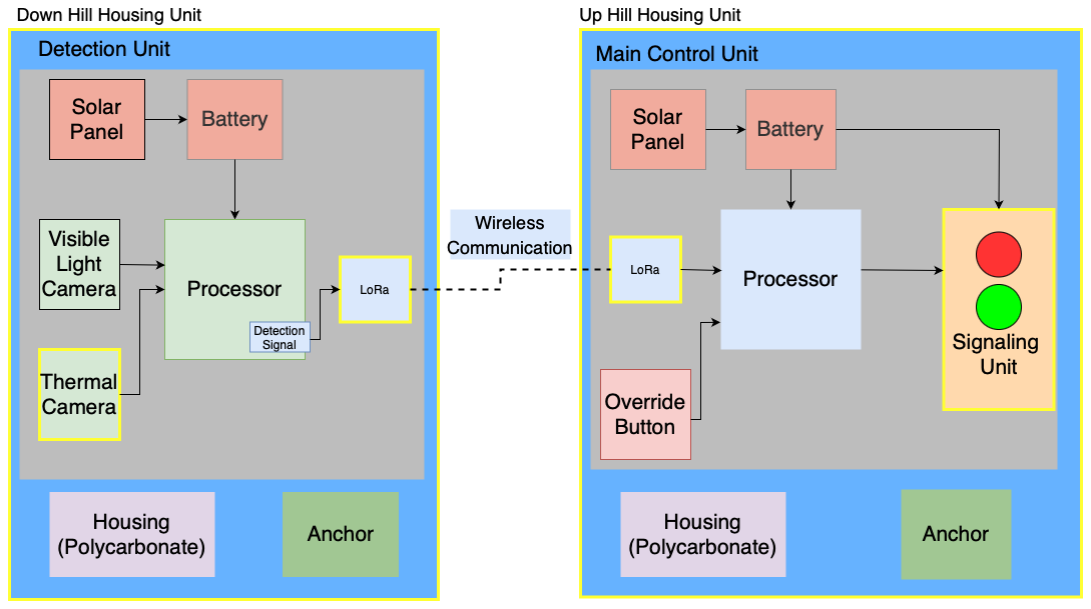
[picture p47: figure]

Conceptual Block Diagram

# Design Solution: Detection Unit

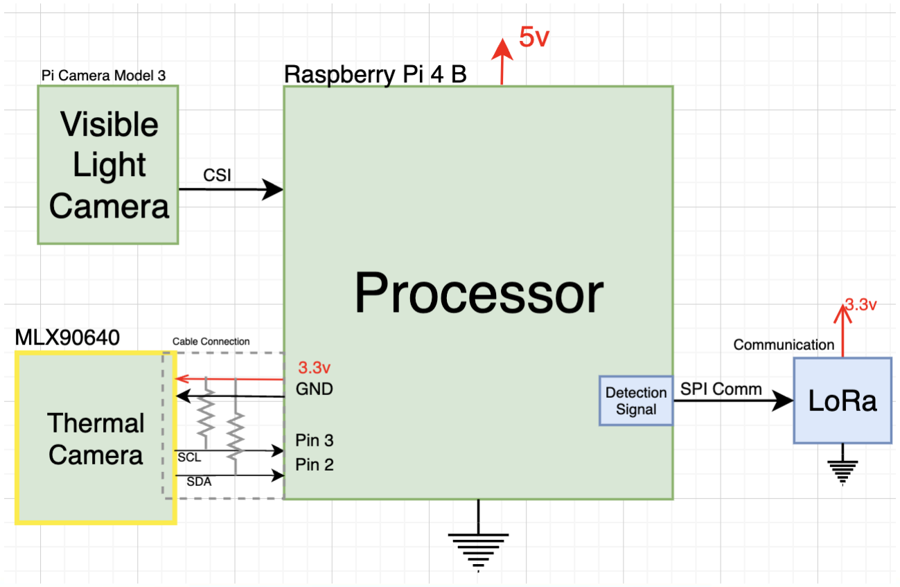
[picture p48: figure]

# Detection Unit: Software Design

## Thermal Camera

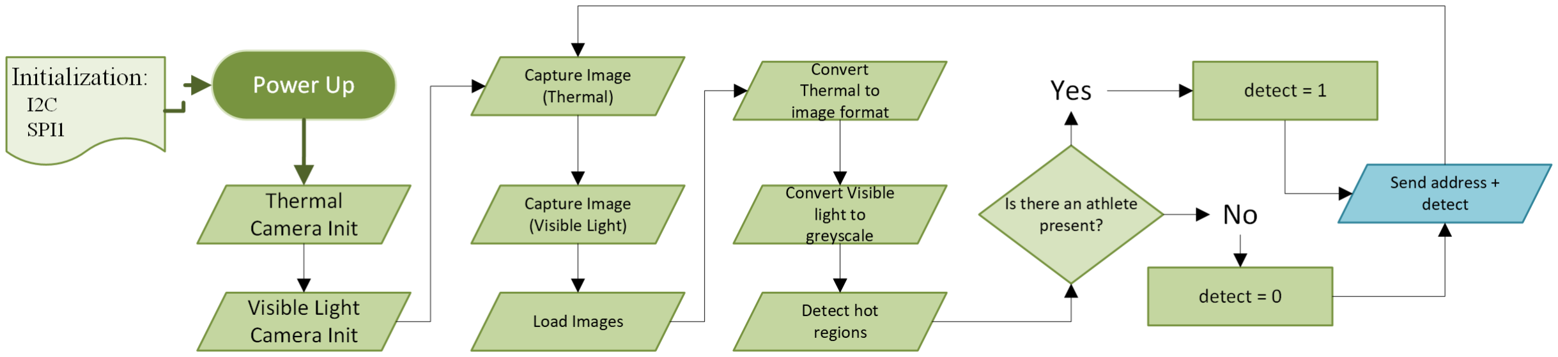
[picture p49: figure]

I2C slave address | 0x33
RAM start address | 0x0400

# Detection Unit Preliminary Prototype

Spec 1.1.1) Detection system must be able to detect athletes within a 30x30 ft area within the landing area

### Issue/Risk:

- I am unfamiliar with image processing, and how to interpret images in MATLAB

### Prototype:

- Gain familiarity with MATLAB image processing toolbox.
- Interpret images in MATLAB (Determine presence of athlete)
- The data to be collected will be the accuracy between different layers of clothing. (Threshold of 95%)

### Benefits:

- Doing this will ensure the successful interpretation of the images from the cameras once they are sent to the raspberry pi
- The data will be used to create the program to run the subsystem

# Downhill Housing Subsystem

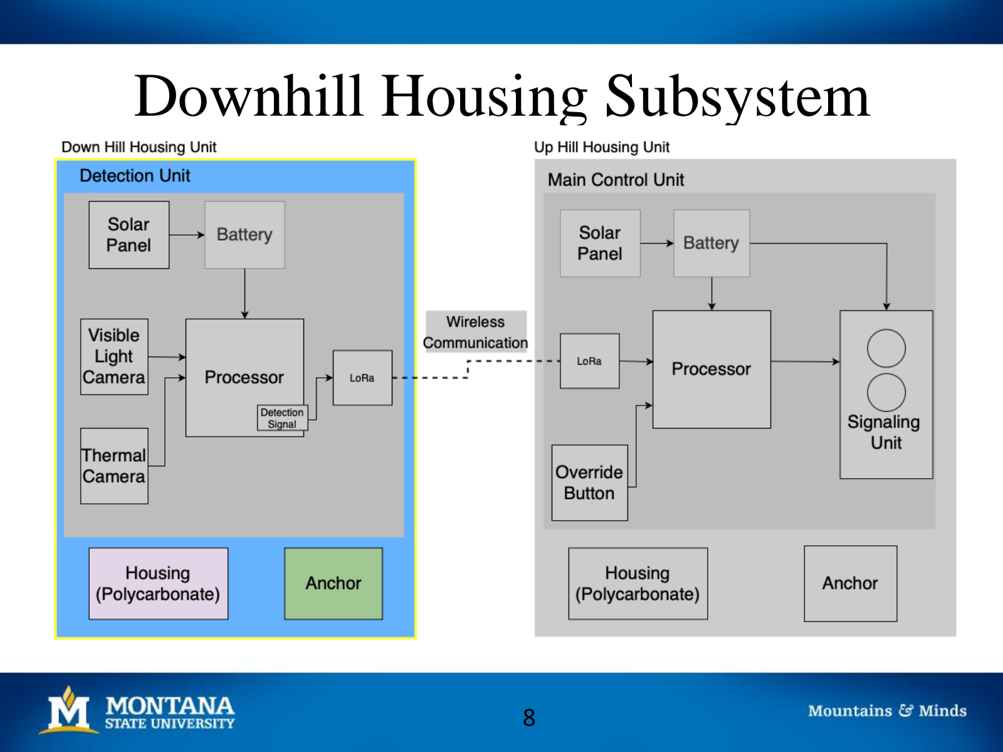
[picture p50: page 8]

# Design Solution: Downhill Housing

Downhill housing from PolyCase
- Weatherproof
- Clear cover for detection system visibility
- Custom machinability
- Fully adjustable on the stake using U-bolts

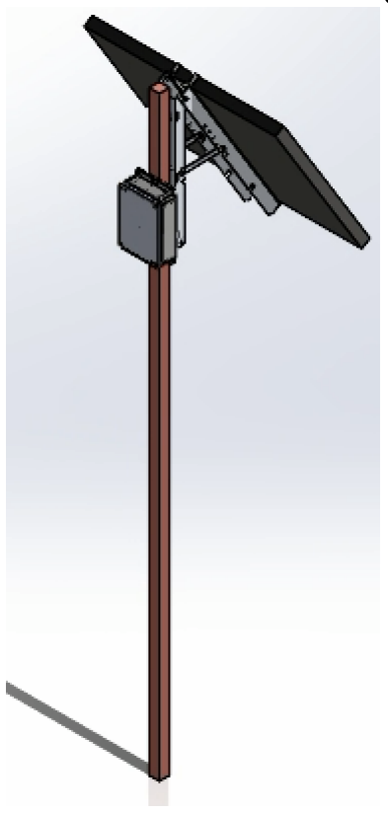
[picture p51: figure]

3D model of the downhill
components mounted on the
Polystake

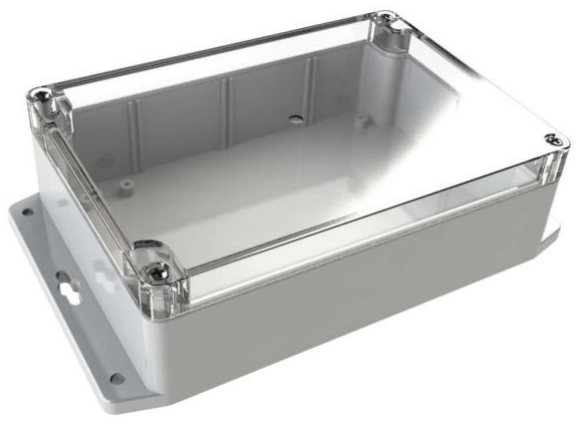
[picture p52: figure]

6.73 x 4.76 x 2.17 inch case PolyStake from FallLine
- Same stakes used for marking at resorts such as Bridger Bowl
- Made to bend if ran into by a skier or snowboarder
- 1.25” x 1.25” x 6’ Stake, providing the necessary height for adjustment

# Downhill Housing Preliminary Prototype

Issues/Risk:
- The exact solar panel and battery to be mounted is unknown, as we are still determining needed power for the detection unit
Prototype:
- Will test the ability of the Detection Unit to detect through the clear polycarbonate cover
- Done by collecting images at various decreasing temperatures and comparing them to a test image
- Data will be analyzed by examining the contrast and the change in dimensions of the gridlines
- Plot the analyzed data as a function of temperature
Benefits:
- Allow us to make sure the downhill housing fully cooperates with the detection system

Req 2.1) Must have housing material capable of protecting electronics while
ensuring operation in varying weather conditions
Spec 2.1.1) Must be able to withstand and function in temperatures ≥ 0°F Spec 2.1.2) Must be able to operate in winds up to 20 mph
Spec 2.1.3) System is not meant to operate in visibility lower than 30 ft or

# Example Test Image

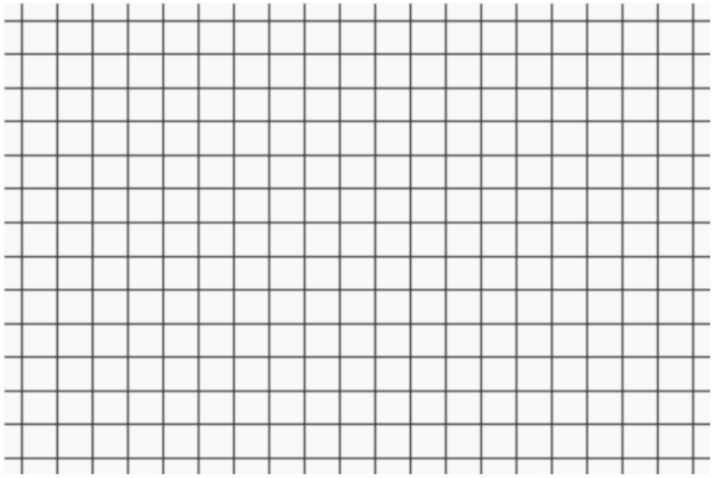
[picture p53: figure]

# Theoretical Results Plot

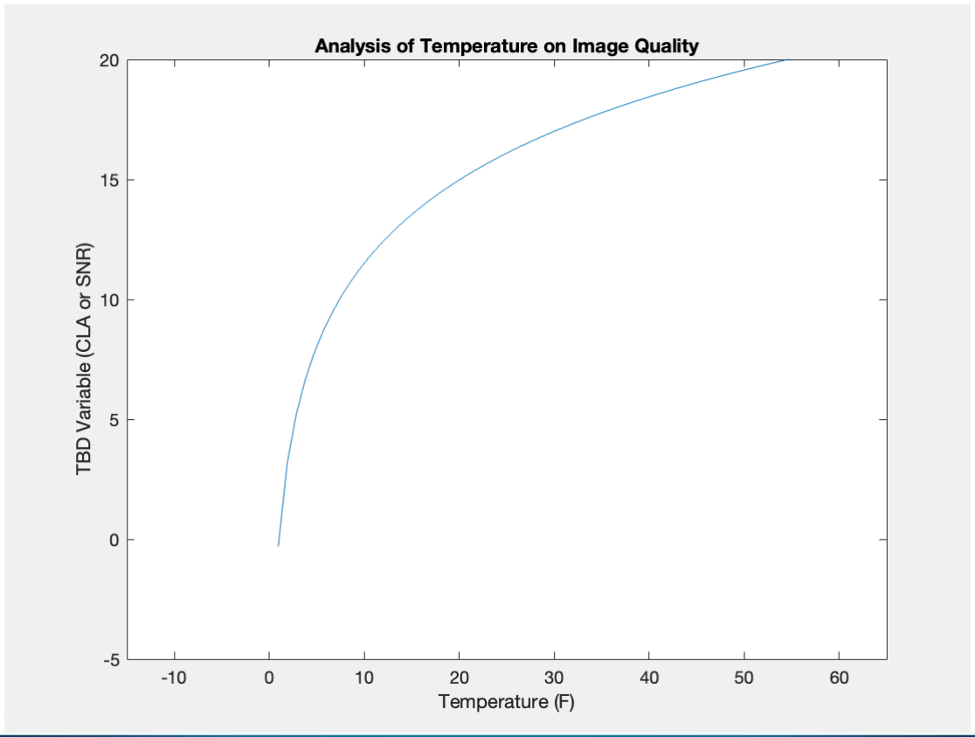
[picture p54: figure]

# Communication Subsystem

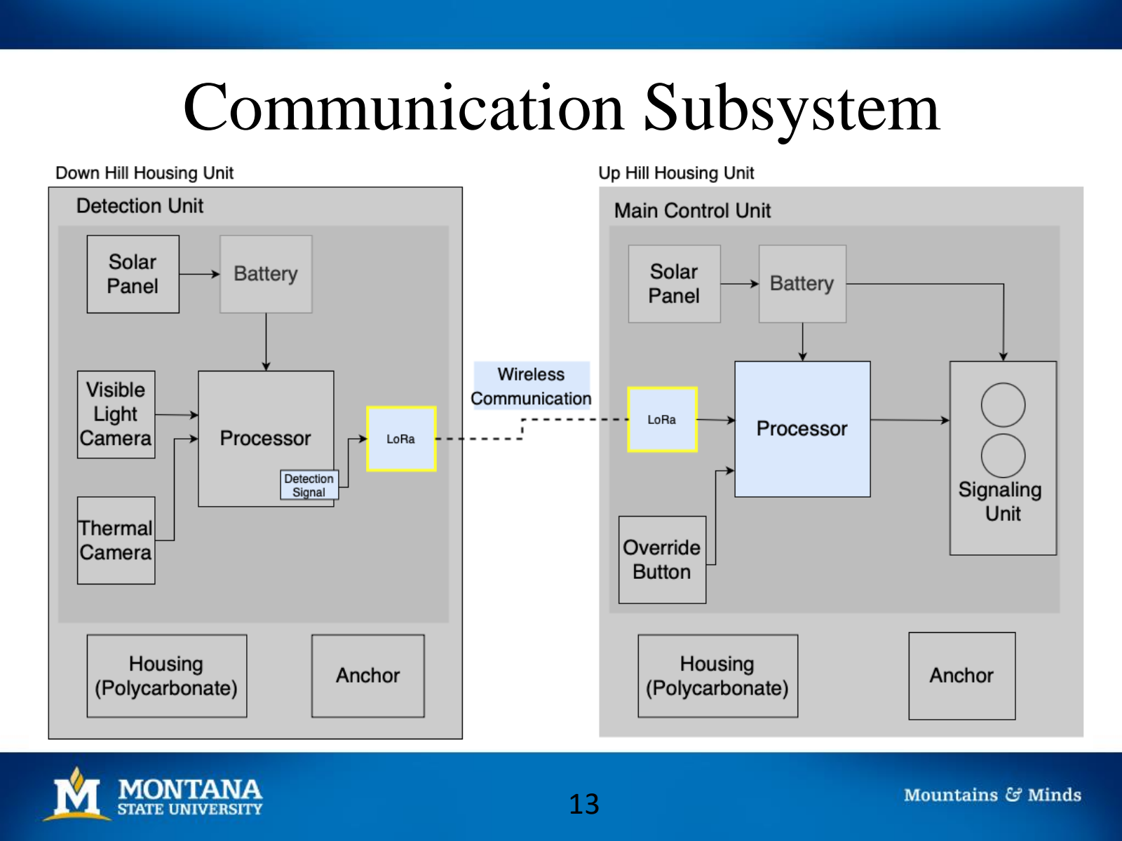
[picture p55: page 13]

# Design Solution: Communication

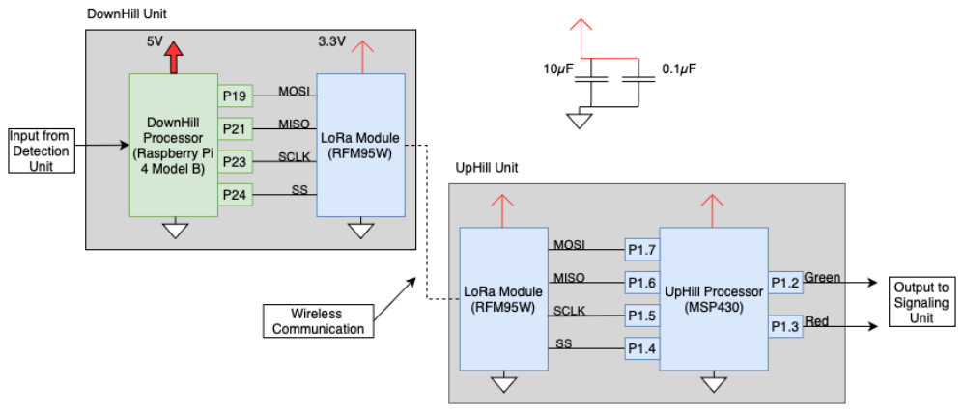
[picture p56: figure]

# Design Solution: Communication Flow Chart

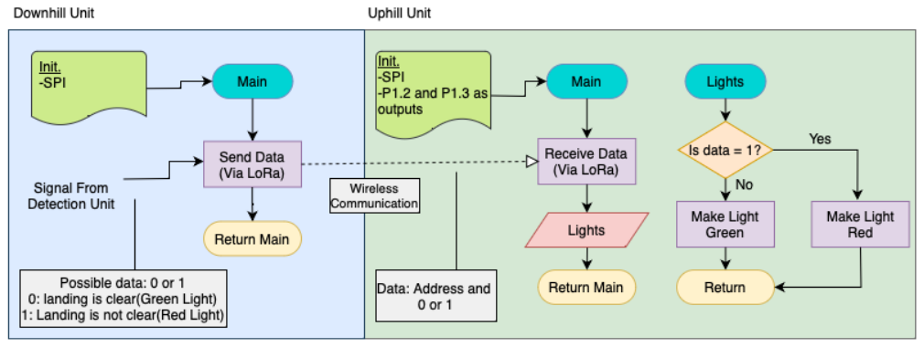
[picture p57: figure]

# Communication Preliminary Prototype

## Risk:

- Unfamiliarity with LoRa
- Latency
- Data loss during
transmission

Req 1.2) Communication between units must be wireless
Spec 1.2.1) Latency from when the sensor triggers to when the signaling unit triggers must be less than 0.5s
Spec 1.2.2) Dropout rate of information must be less than 2%
Spec 1.2.3) Sensors must communicate with signaling unit from a maximum distance of 60 ft away with a direct line of sight

## Prototype:

- Build the uphill and downhill units, including LoRa modules and processors.

## Testing/Data:

- Starting at 60 ft test:
– Latency: will be plotted as a function of distance
– Packet loss: will be plotted as a function of distance
- Then test at a range 10ft – 200ft, and without direct line of sight.
- This data will then be used to verify a working subsystem and reveal weaknesses in the system, such as signal strength, latency and packet loss.

# Communication Preliminary Prototype

To collect latency:
- Send a packet of data from downhill unit
to uphill unit.
- Once received, send an acknowledgement back to downhill unit

To measure latency:
- Start a timer on downhill unit before packet is sent and stop timer when acknowledgement is received.
- Start a timer when uphill unit received data and stop timer when ack is sent.

To collect Packet loss:
- Send one packet 500 times

To measure packet loss:
- Measure how many packets were received
- Measure the inaccuracy of packets received

DH timer – UH timer = 2x Latency Goal: latency ≤ 100 ms

Packet loss % + inaccuracy % ≤ 2%

# Lighting Unit Subsystem

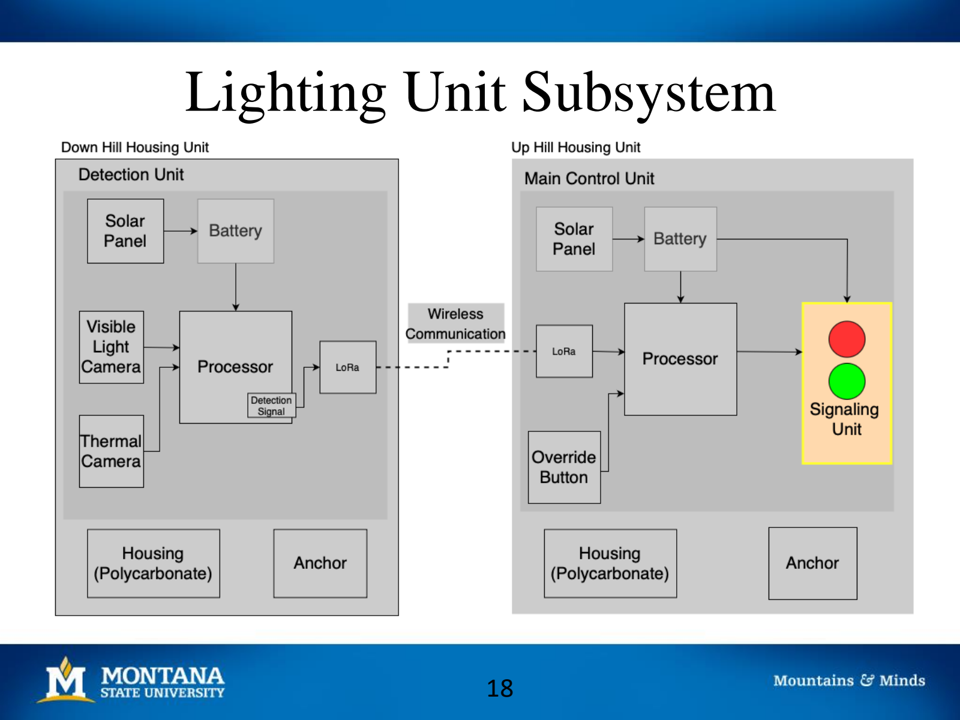
[picture p58: page 18]

# Design Solution: Signaling Unit

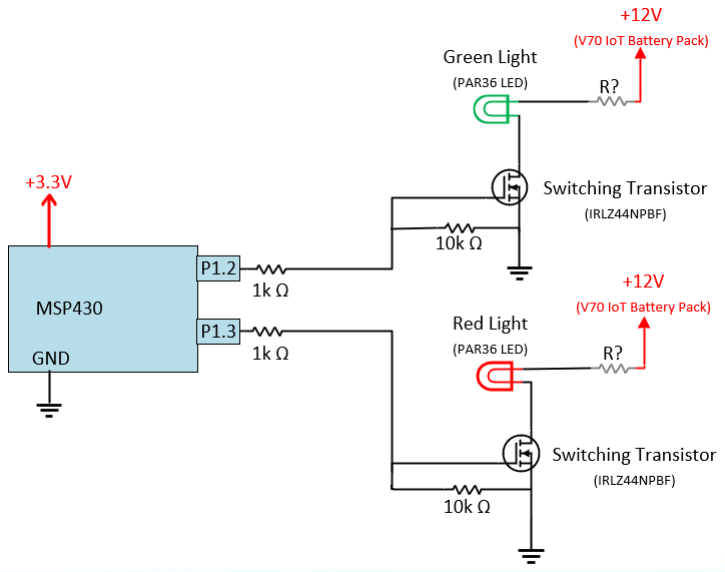
[picture p59: figure]

- Control signal from
microcontroller will
control light color
- Each transistor acts as
switch
- High control signal
will turn on a light
- Lights will be
primarily powered by
solar battery, with a
backup battery
capability

# Signaling Unit Preliminary Prototype

Issues/Risk:
- Exact current draw from the lights is unknown
- Visibility of lights

Prototype:
- Test lumen count
- Measure voltage across each light
- Measure current through each light
- Measure current and voltage through each transistor (on and off)
- Measure gate voltage and current

Benefits:
- Knowing the amount of current through the lights will allow us to finish power calculations and pick a backup battery
- If lumen count is high enough, we can potentially add a current limiting resistor to increase power efficiency

# Signaling Unit Preliminary Prototype

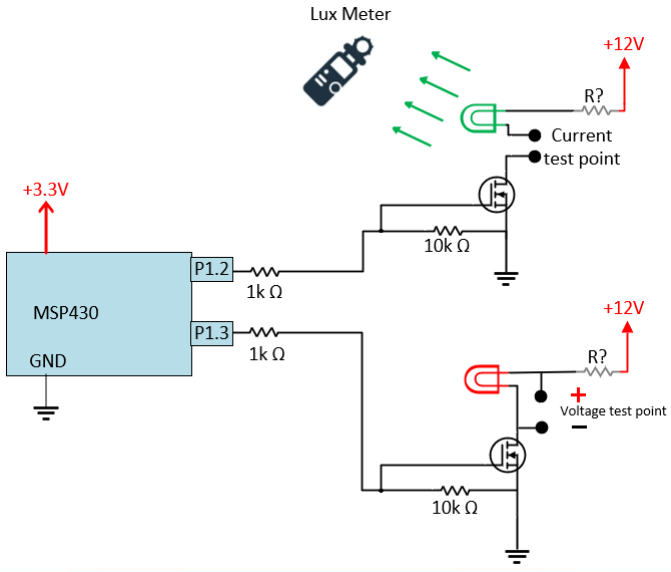
[picture p60: figure]

# Uphill Housing Subsystem

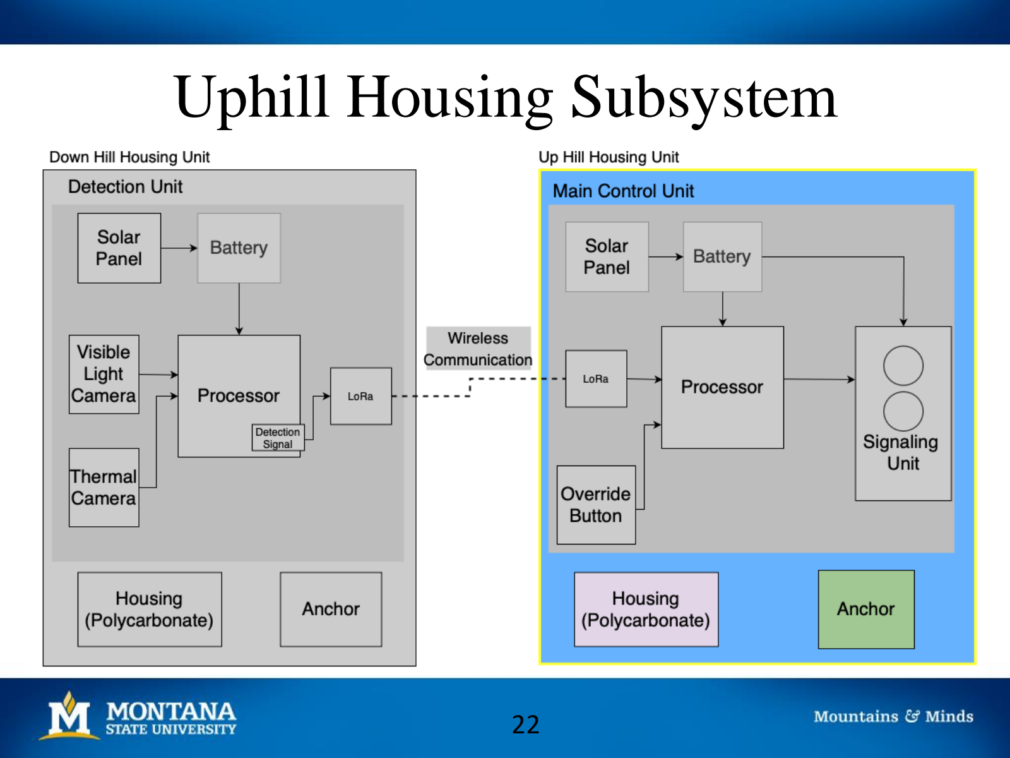
[picture p61: page 22]

# Design Solution: Uphill Housing

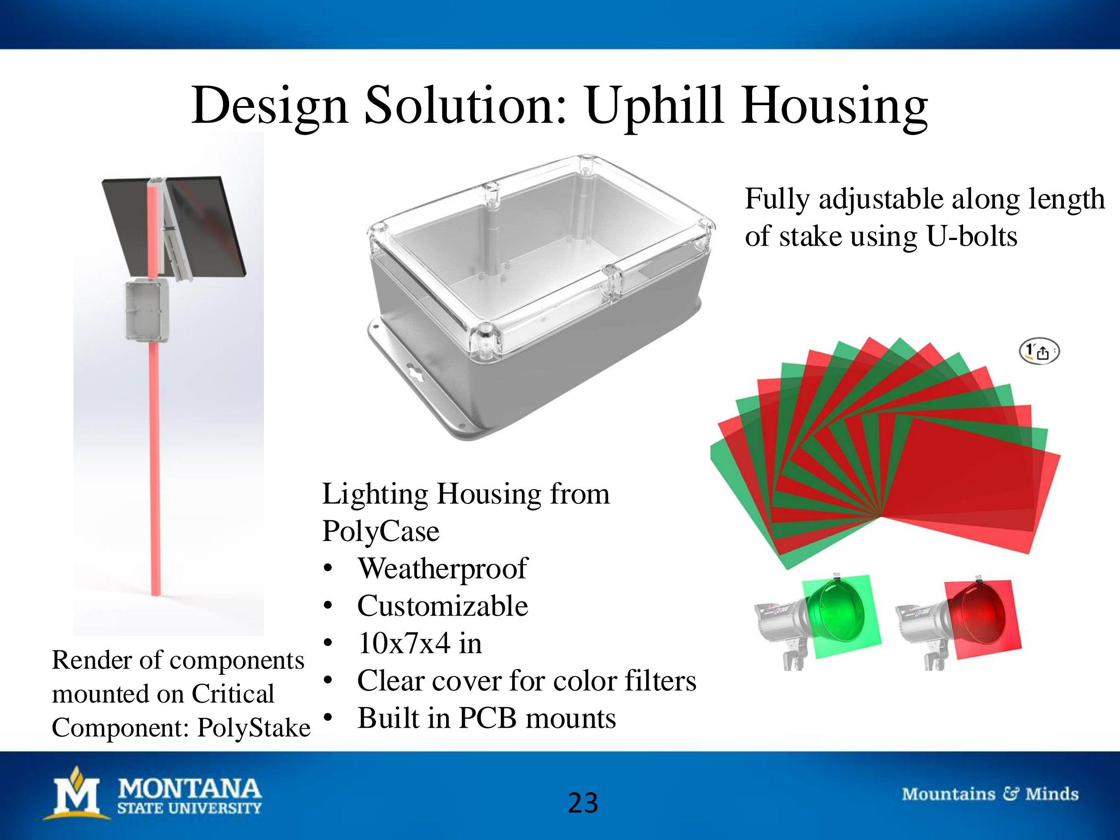
[picture p62: page 23]

Lighting Housing from
PolyCase
- Weatherproof
- Customizable
- 10x7x4 in
- Clear cover for color filters
- Built in PCB mounts

Render of components
mounted on Critical
Component: PolyStake

Fully adjustable along length of stake using U-bolts

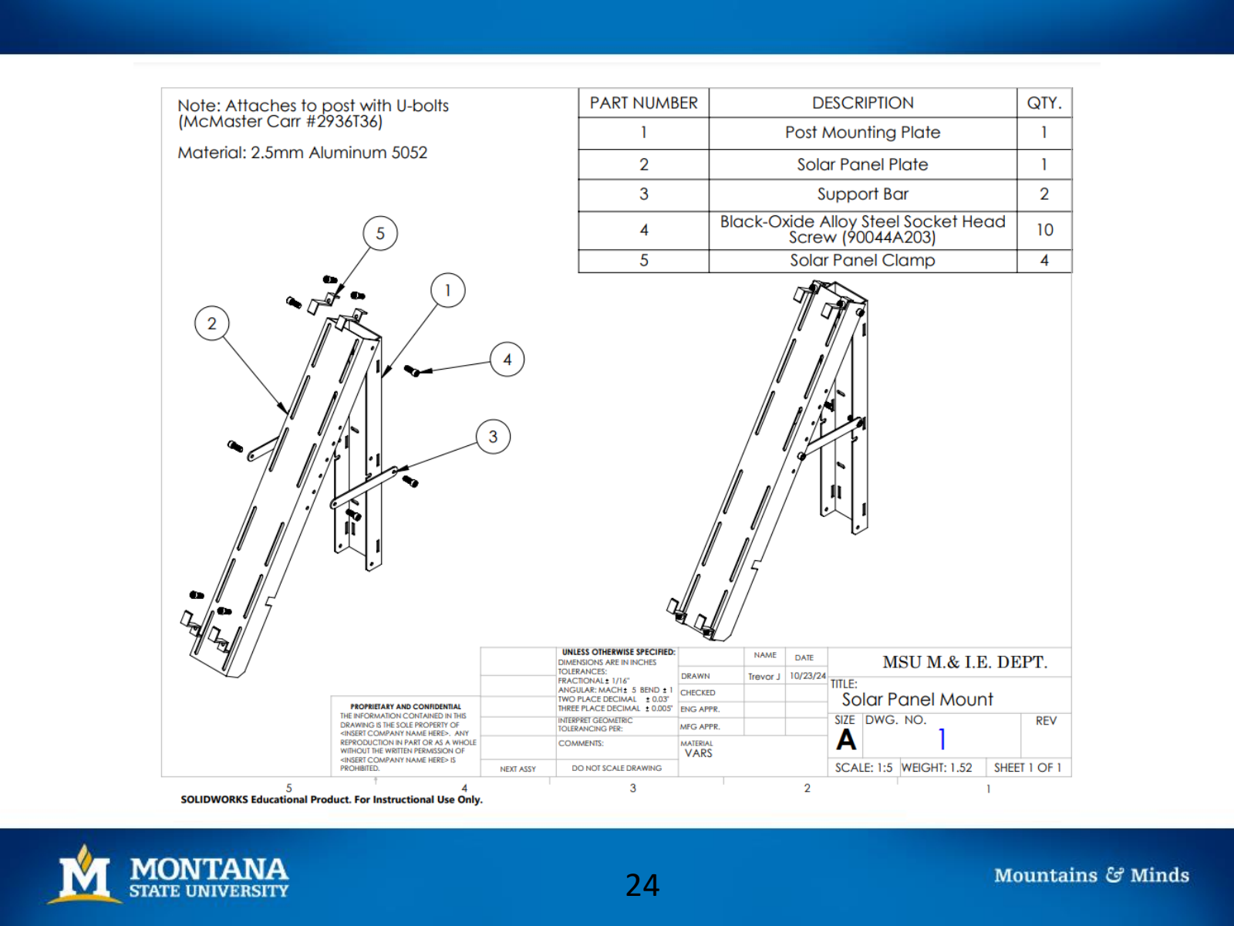
[picture p63: page 24]
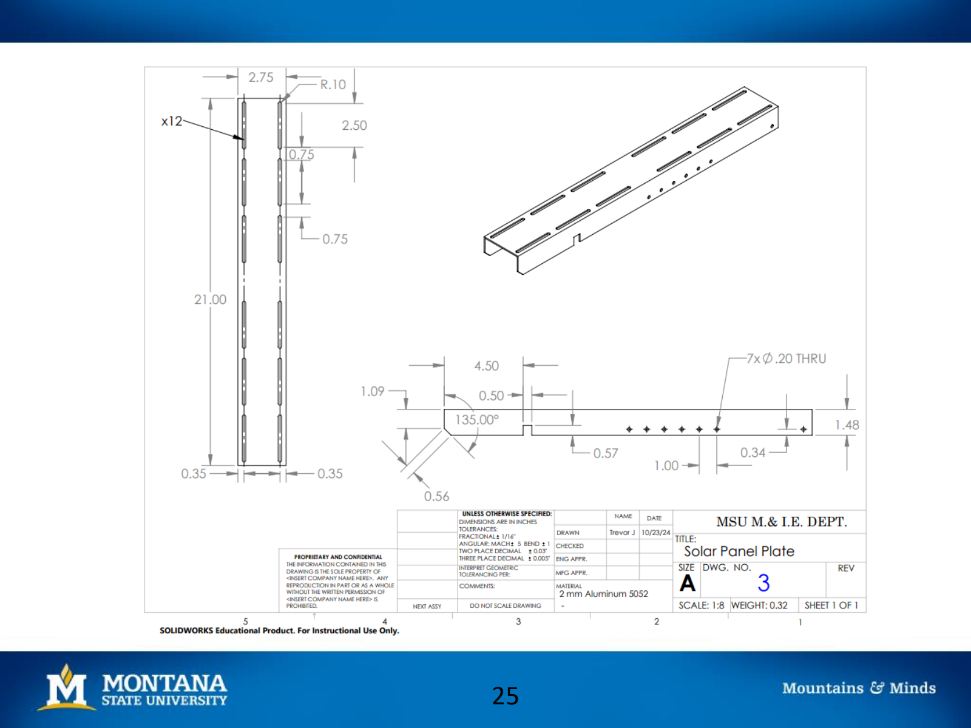
[picture p64: page 25]

# Uphill Housing Preliminary Prototype

Prototype:
- The displacement at the top of the stake vs incremental loads (1 pound per measurement) will be measured and analyzed
- Will test a few pounds over the equivalent load calculated to ensure reliability
- A sandbag will be tied to the top of the stake to simulate the load
- Stake inserted in sand water mix to simulate snow
Benefits:
- Accurate data on how much weight our stake can withstand
- Potentially will need to reinforce the stake

Issue/Risk:
- Mounting Stake must be able to support the weight of solar panel, solar panel mount, lighting unit, and battery/housing

# Ideation of Complete System Design

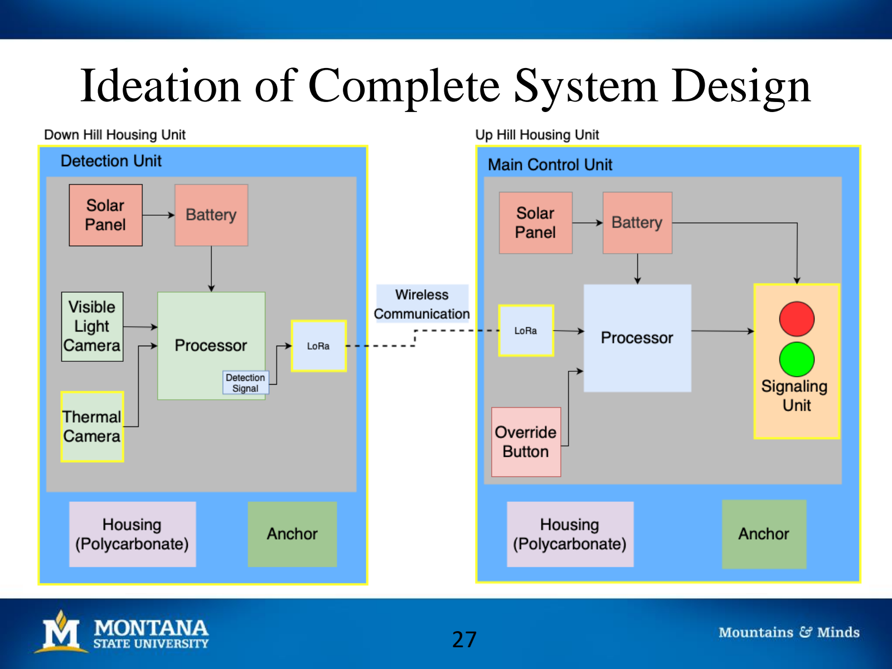
[picture p65: page 27]

# Additional Subsystems

# Power Subsystem

## Uphill Unit: - 50 Watt 18 Volt Solar Panel (Voltaic) - 12V Lithium-ion battery (Ah needed unknown) - Charge controller - 12V to 3.3V DC/DC converter Downhill Unit: - Expected Wattage 15W (5V and 3A) - 12V to 5V DC/DC converter

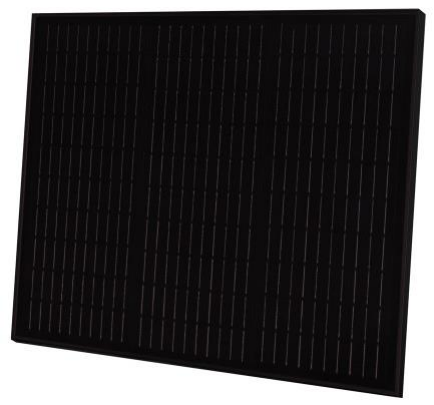
[picture p66: figure]

Uphill Solar Panel
(23 x 20 x 1.2 in)

# Estimated Budget

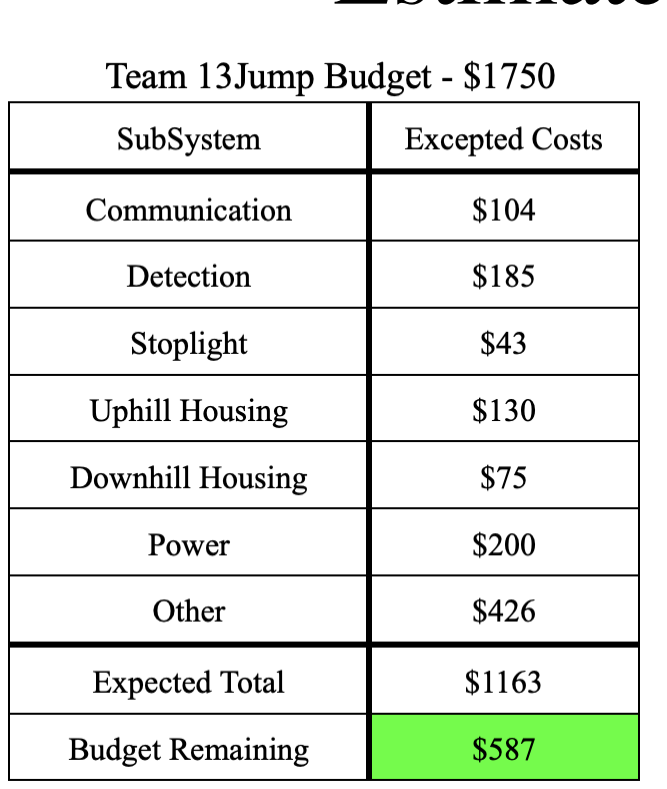
[picture p67: figure]

Key Items Costs:
- LoRa - $75
- Thermal Camera - $75
- Visible Light Camera - $35
- Raspberry Pi 4 - $75
- Stoplights - $28
- Uphill housing - $40
- Solar panel and battery - $200

# Summary

- This project aims to enhance skier safety by providing real-time information about the landing zone's clarity, reducing collision risks and promoting smoother traffic flow in terrain parks. With the design phase complete, we are preparing to begin prototype testing.
- Our progress is supported by our expertise, resources, and commitment to improving safety. We have designed a robust system that integrates thermal and visible light imaging technologies for accurate monitoring of the landing area.
- The potential to significantly reduce accidents makes this project valuable. As we test the system, we believe it will effectively prevent collisions, and we will make necessary adjustments to optimize its performance in real-world conditions.

# QUESTIONS?

# ADDITIONAL SUPPORT SLIDES

Objective 1: Determine whether the landing area below a jump is clear,

## and then report the status to athletes uphill from the landing area

Req 1.1) System must detect when the landing area is clear
Spec 1.1.1) Detection system must be able to detect athletes within a 30x30 ft area within the landing area
Spec 1.1.2) Must have ≥ 95% detection rate
Req 1.2) System must communicate detection results to uphill athletes
Spec 1.2.1) Latency from when the sensor triggers, to when the signaling unit triggers, must be ≤ 0.5s
Spec 1.2.2) Dropout rate of information must be ≤ 2%
Spec 1.2.3) Sensors must communicate with signaling unit from a maximum distance of 60 ft away with a direct line of sight
Req 1.3) System must notify the next athlete it is safe to proceed
Spec 1.3.1) Signal must produce a green light when the landing area is clear
Spec 1.3.2) Signal must produce a red light when the landing area is not clear
Spec 1.3.3) The latency of the light changing states after a signal is received must be ≤ 0.5 seconds
Spec 1.3.4) Must have a manual override to send the system to the “stop” state in case of emergencies or other events

## Objective 2: The system must operate in inclement weather throughout the months of December through April

Req 2.1) Must have housing material capable of protecting electronics while ensuring operation in varying weather conditions
Spec 2.1.1) Must be able to withstand and function in temperatures ≥ 0°F Spec 2.1.2) Must be able to operate in winds up to 20 mph
Spec 2.1.3) System is not meant to operate in visibility lower than 30 ft or when the terrain park is not operational
Req 2.2) Signaling Unit must be visible to athletes in varying weather conditions Spec 2.2.1) Must be able to see signaling unit from 30 ft away uphill
Spec 2.2.2) Lights on the signaling unit must produce at least 1000 Lumens Spec 2.2.3) Adjustable between 0 - 5 feet with height increments by ± 6” for every adjustment

## Objective 3: The system will operate on a standalone power system to avoid running power lines to the system which could create unnecessary hazards

Req 3.1) Power source must be reliable in varying winter conditions
Spec 3.1.1) Must operate continuously for 7.5 hours
Spec 3.1.2) Must have sufficient backup power to operate normally for 21 operational hours
Req 3.2) The system must have the ability to recharge both primary and secondary power sources
Spec 3.2.1) Can recharge for a 7.5 hour operational day with 3.5 hours of peak sunlight
Spec 3.2.2) Backup power can be recharged through an external source in 8 hours for the system to operate for 21 operational hours

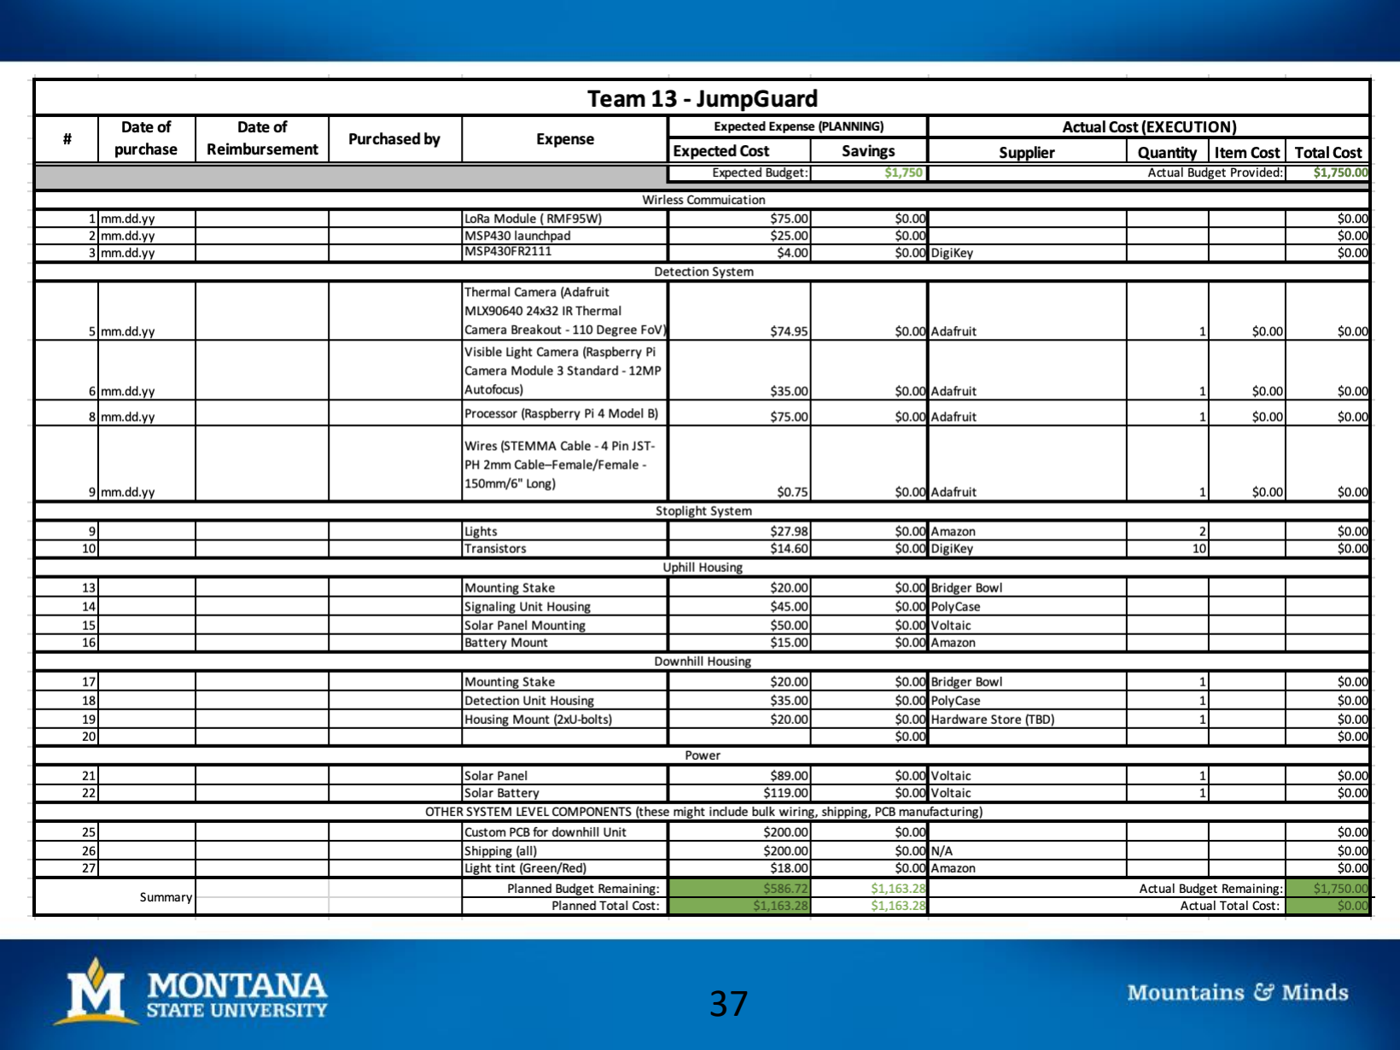
[picture p68: page 37]

# Block Diagram of Detection

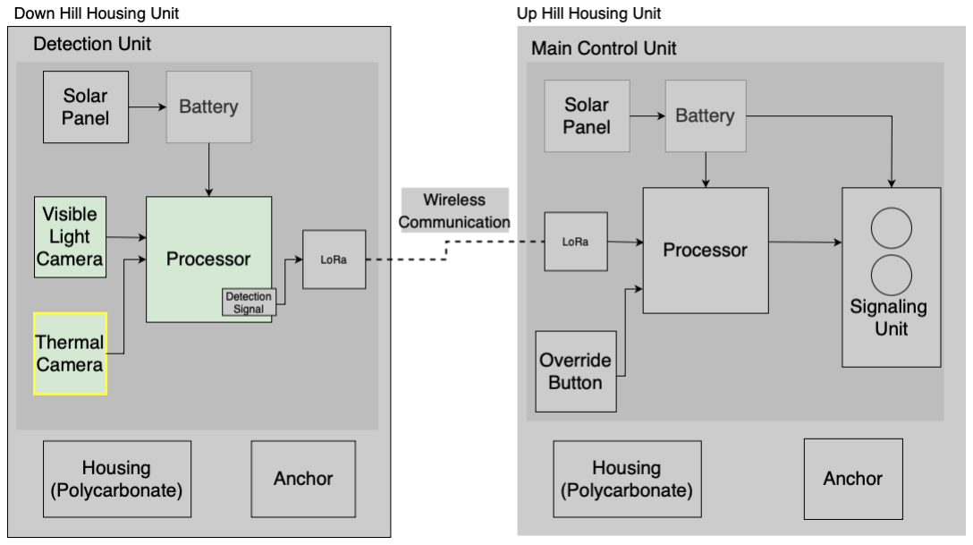
[picture p69: figure]

# Alternative Analysis Thermal Camera

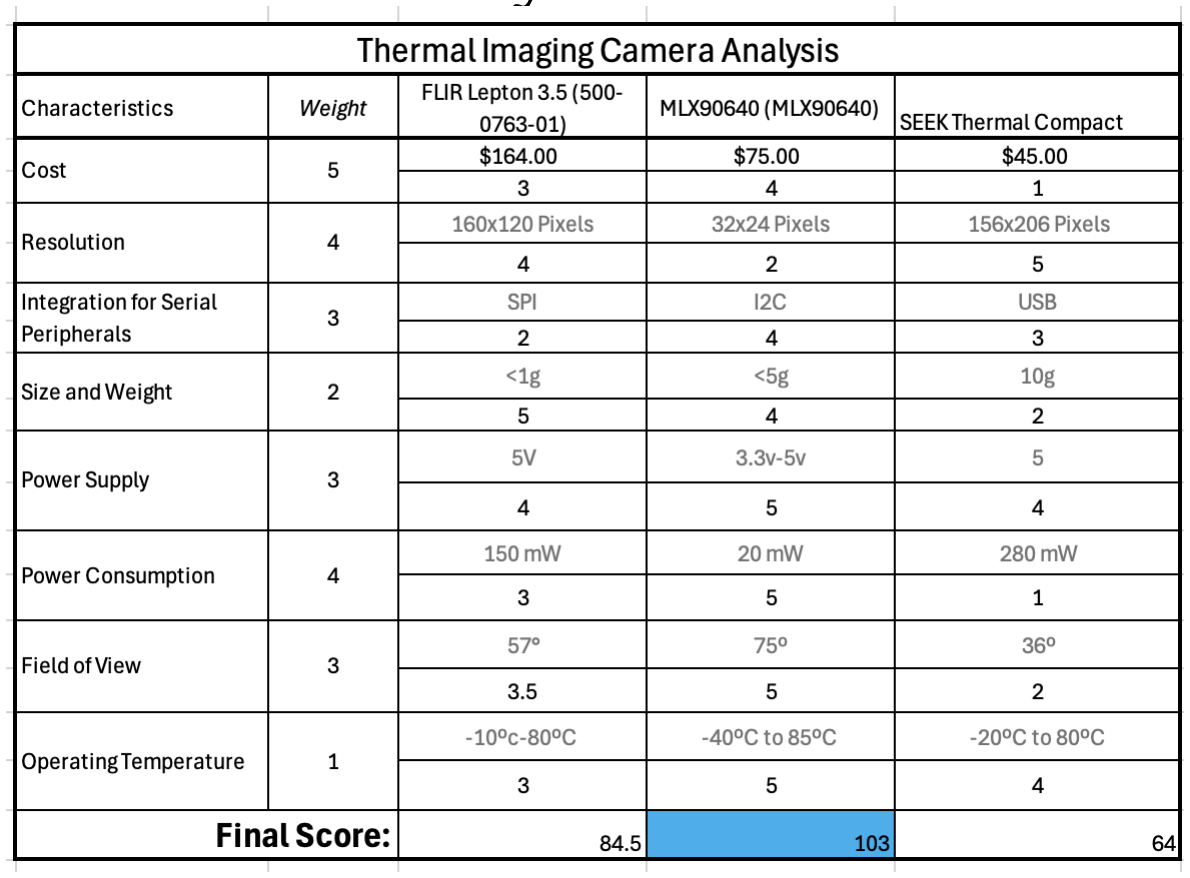
[picture p70: figure]

# I2C Commands/Key Registers

Key Registers/ Commands | Address | Description
RAM Start Address | 0x0400 | Holds pixel data (32x24 resolution). Reading from this address retrieves the temperature data for each pixel. Each pixel value is 16 bits.
Status Register | 0x8000 | This register provides the status of the device, including flags for data availability. Bit 3: New data available flag. Indicates when a new frame of data is ready. Bit 12: Power mode (0 for normal operation, 1 for sleep). Bits 4-7: Subpage selection for interleaved subpage modes
Control Register | 0x800D | Used to configure device operation modes like refresh rate. Refresh Rate Bits (Bits 0-2): 0b000: 0.5 Hz 0b001: 1 Hz 0b010: 2 Hz 0b011: 4 Hz 0b100: 8 Hz 0b101: 16 Hz 0b110: 32 Hz 0b111: 64 Hz Command: Write to the 0x800D register to set the desired refresh rate.
EEPROM Registers for Calibration Data | 0x2400 to 0x273F | Stores the calibration parameters unique to each MLX90640 sensor. These values are needed to convert raw data into accurate temperature readings. Command: Read from 0x2400 to 0x273F to obtain the calibration data, which is 832 bytes long.
Device Identification | 0x2407 to 0x2408 | These registers contain the device ID to identify the specific MLX90640 unit. Command: Read from these registers to retrieve the device ID, which may be useful for device validation or troubleshooting.

# Design Details: Downhill Housing

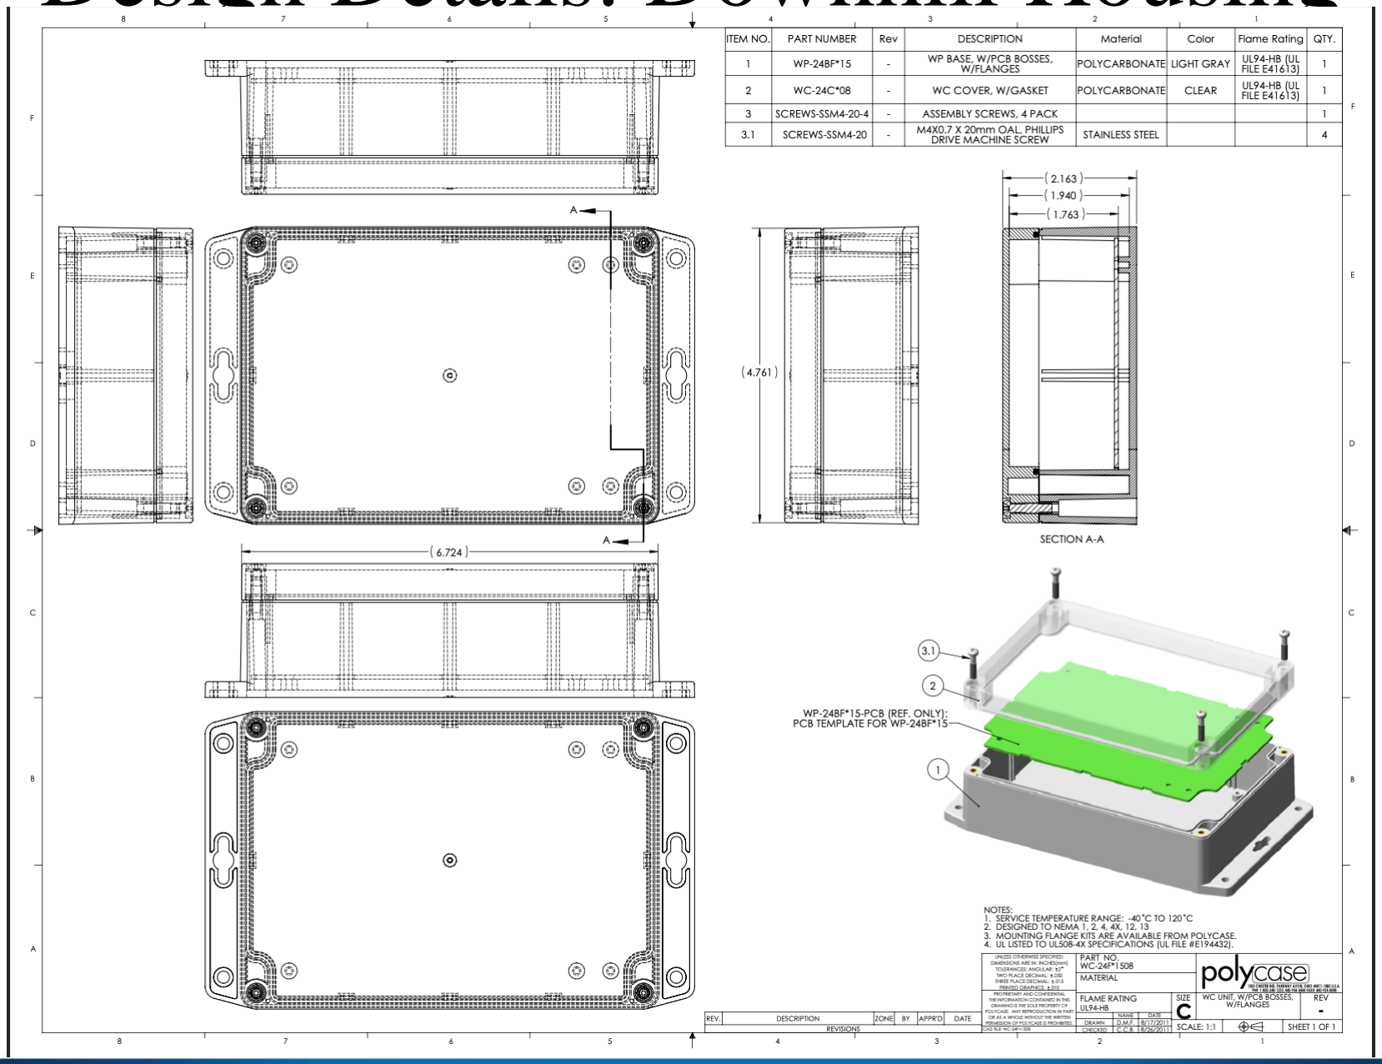
[picture p71: figure]

# Design Details: Downhill Housing

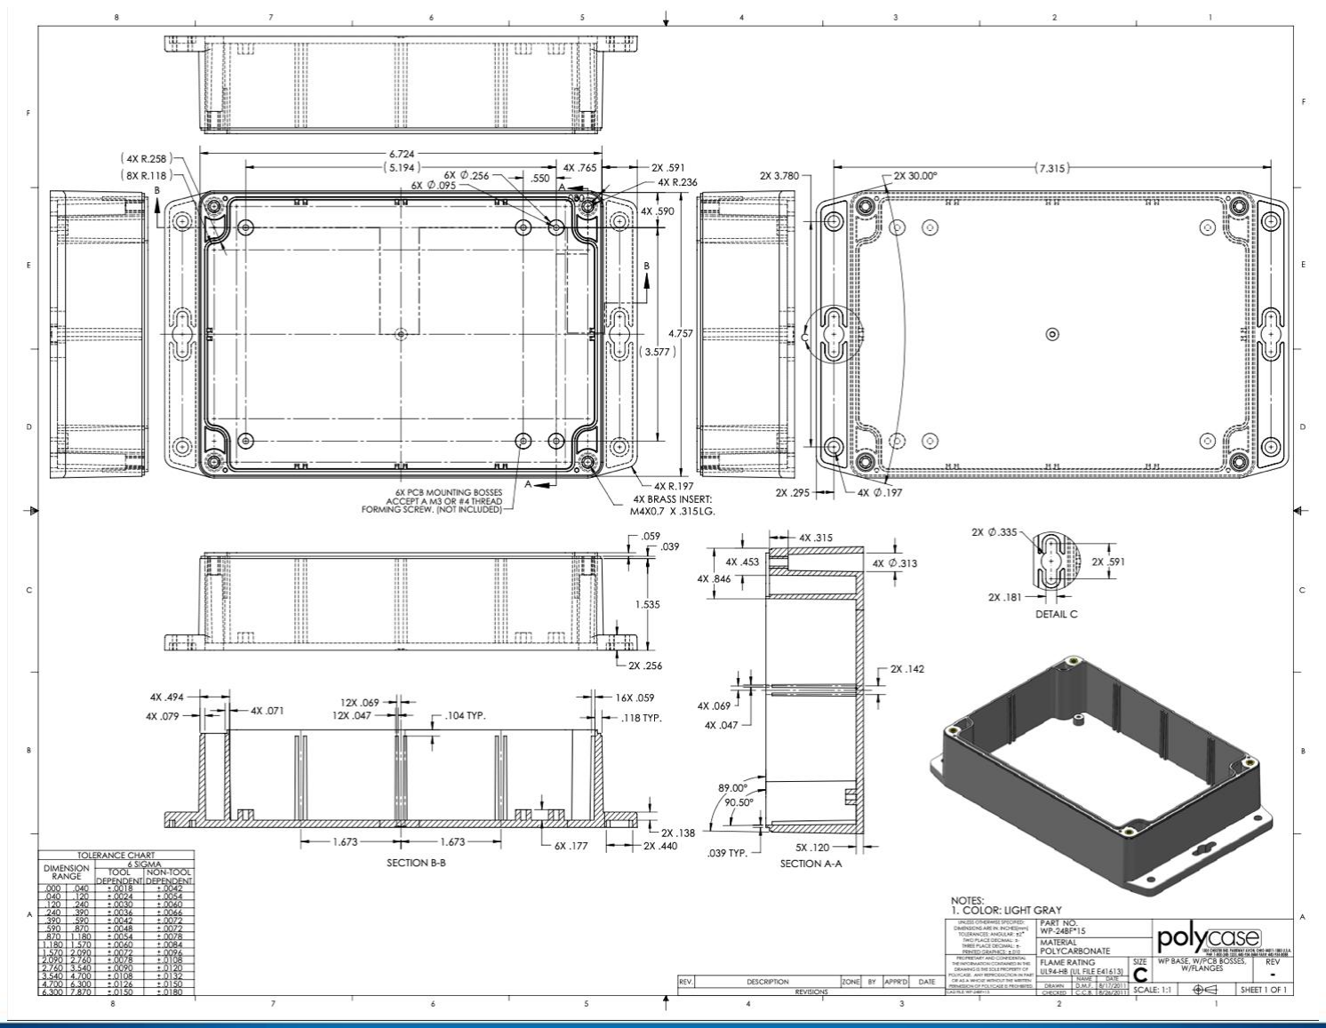
[picture p72: figure]

# Design Details: Downhill Housing

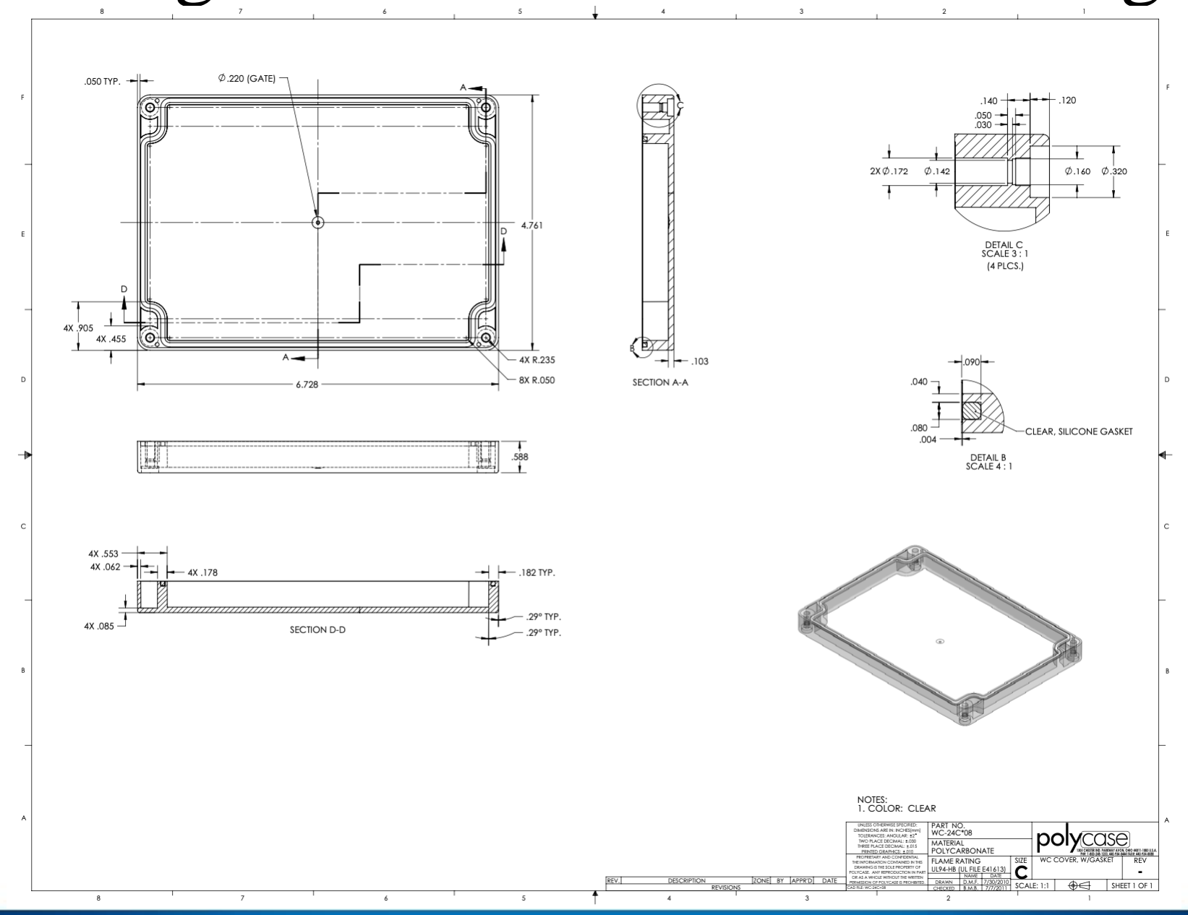
[picture p73: figure]

# Design Details: Downhill Housing

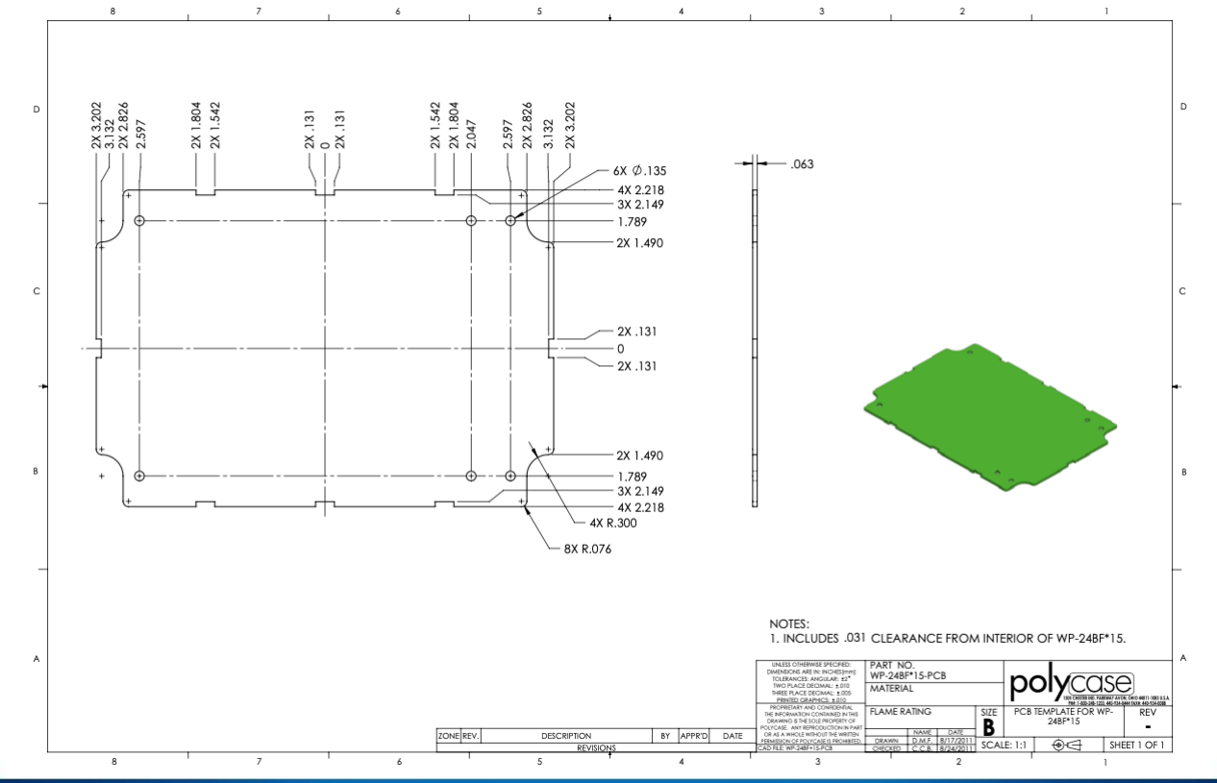
[picture p74: figure]

## Mounting Critical Component Alternatives Analysis

U bolt for mounting
components to PolyStake

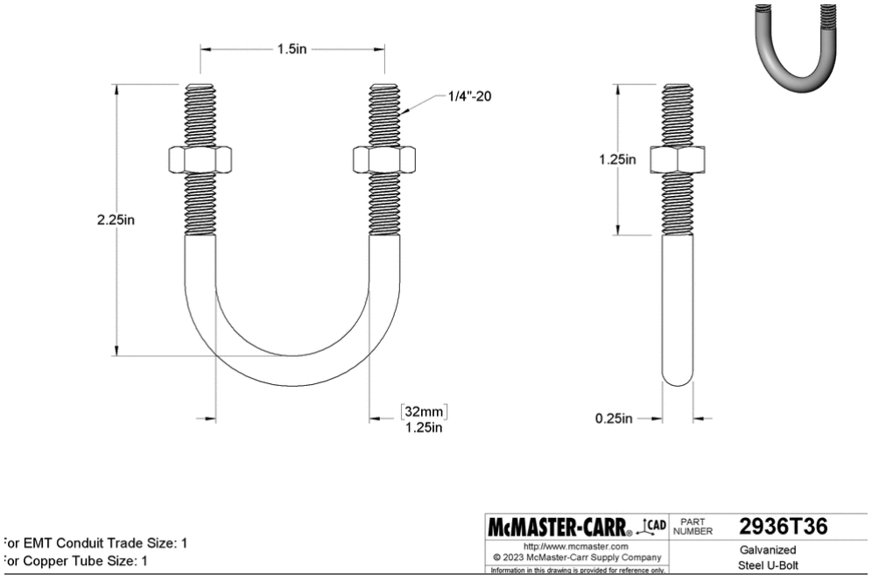
[picture p75: figure]

Solar panel battery case Drawing

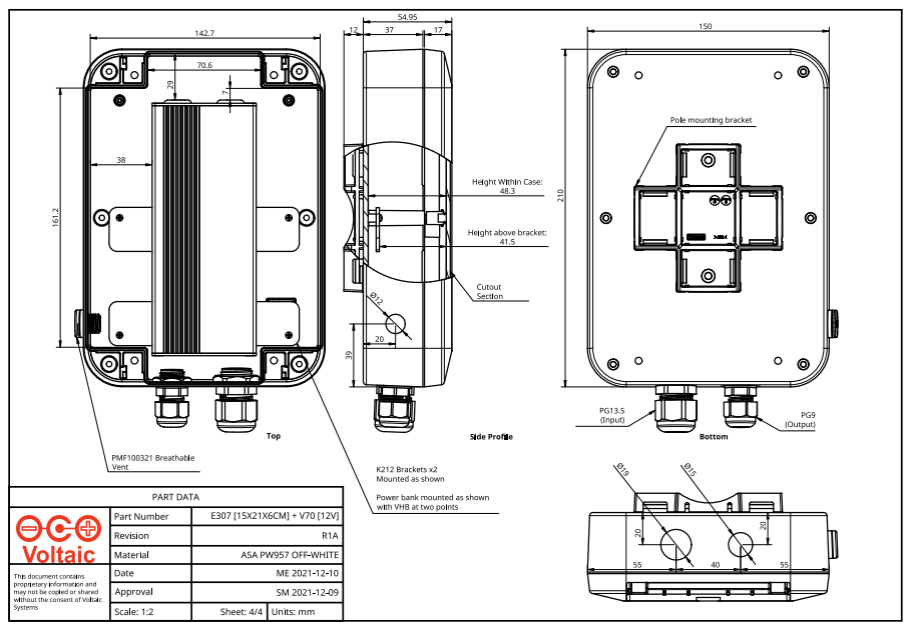
[picture p76: figure]

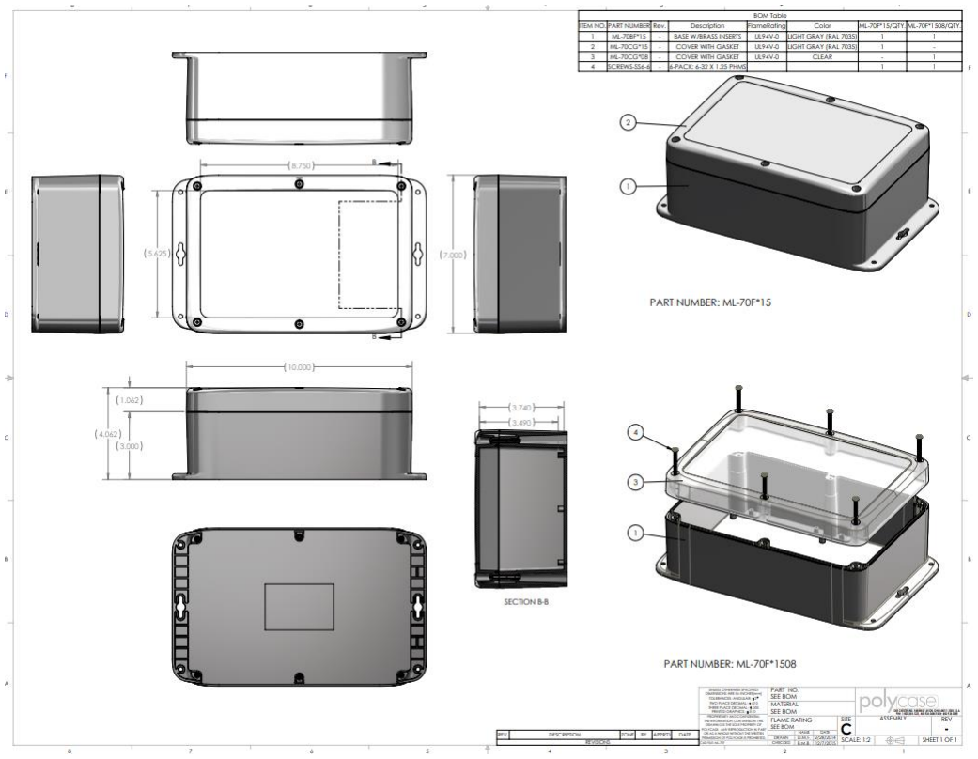
[picture p77: figure]
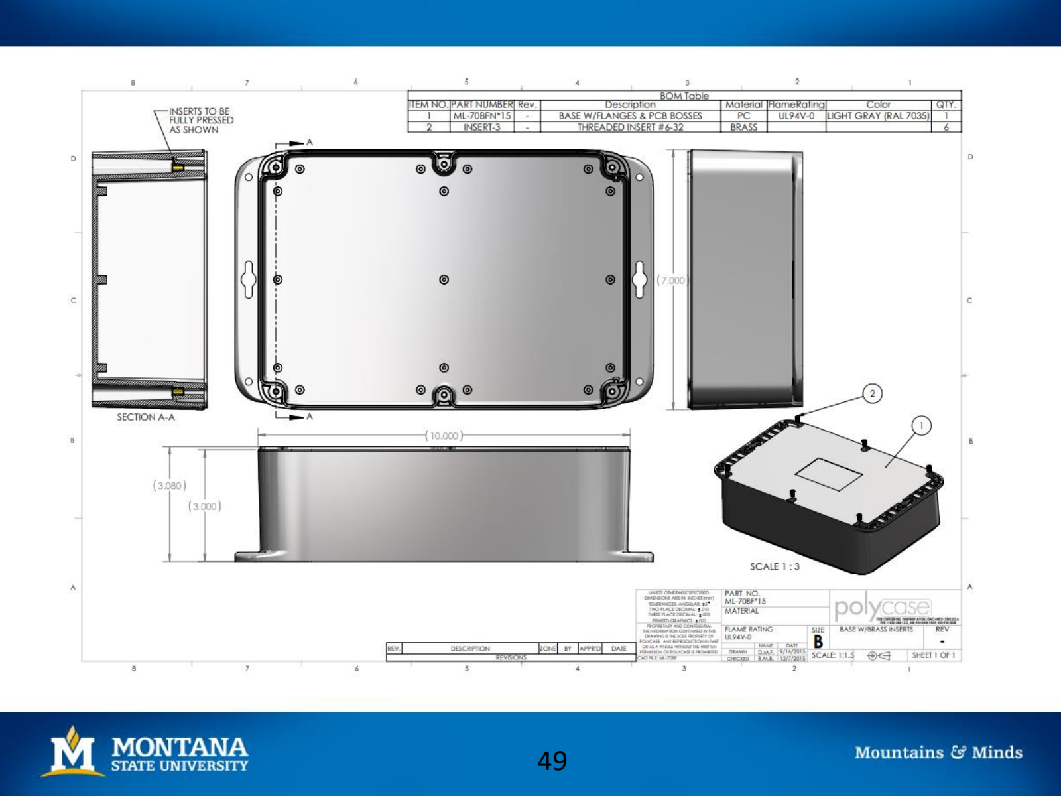
[picture p78: page 49]
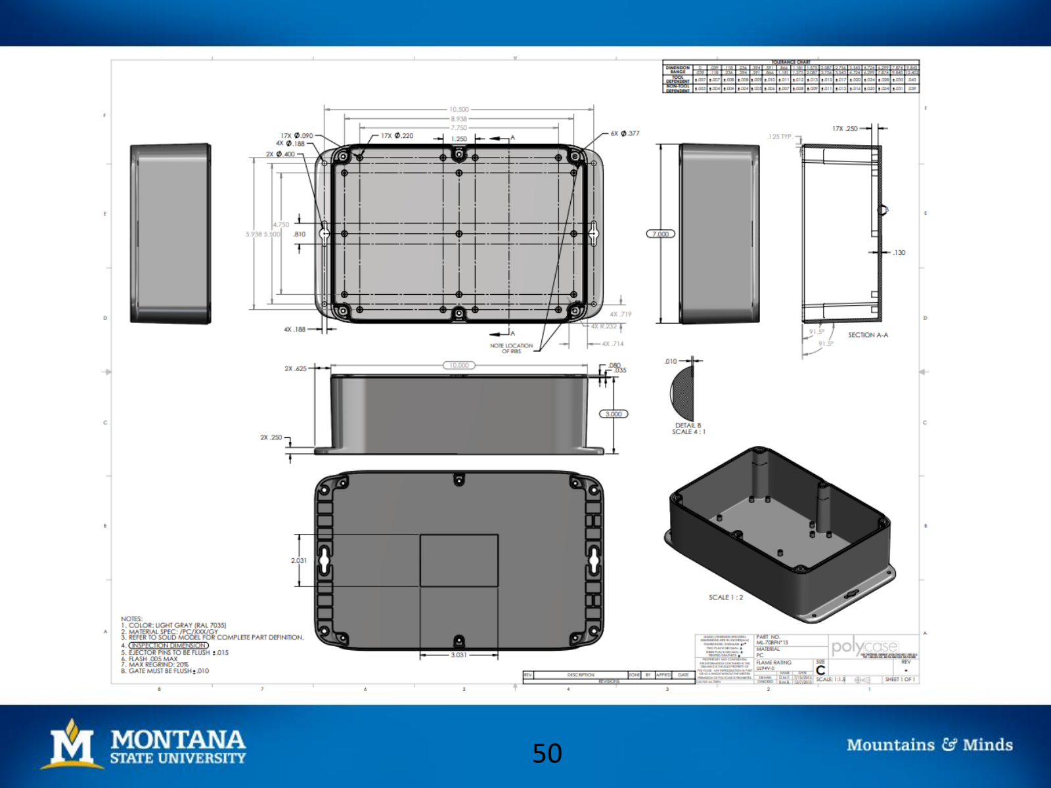
[picture p79: page 50]
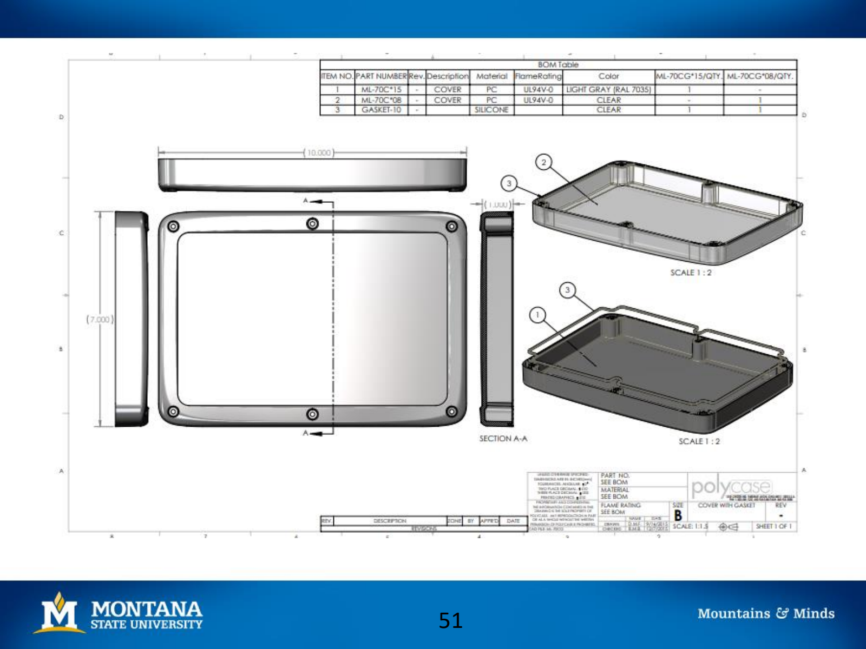
[picture p80: page 51]
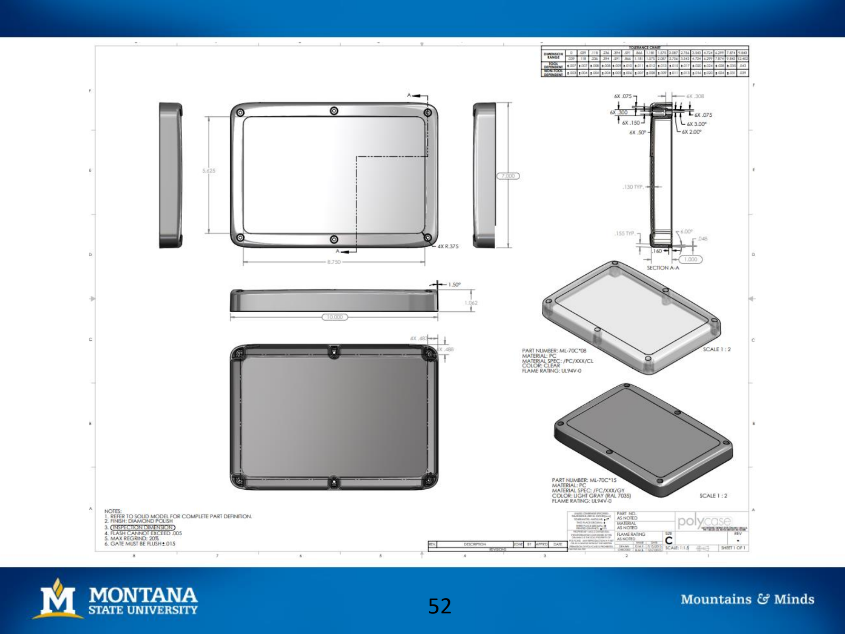
[picture p81: page 52]
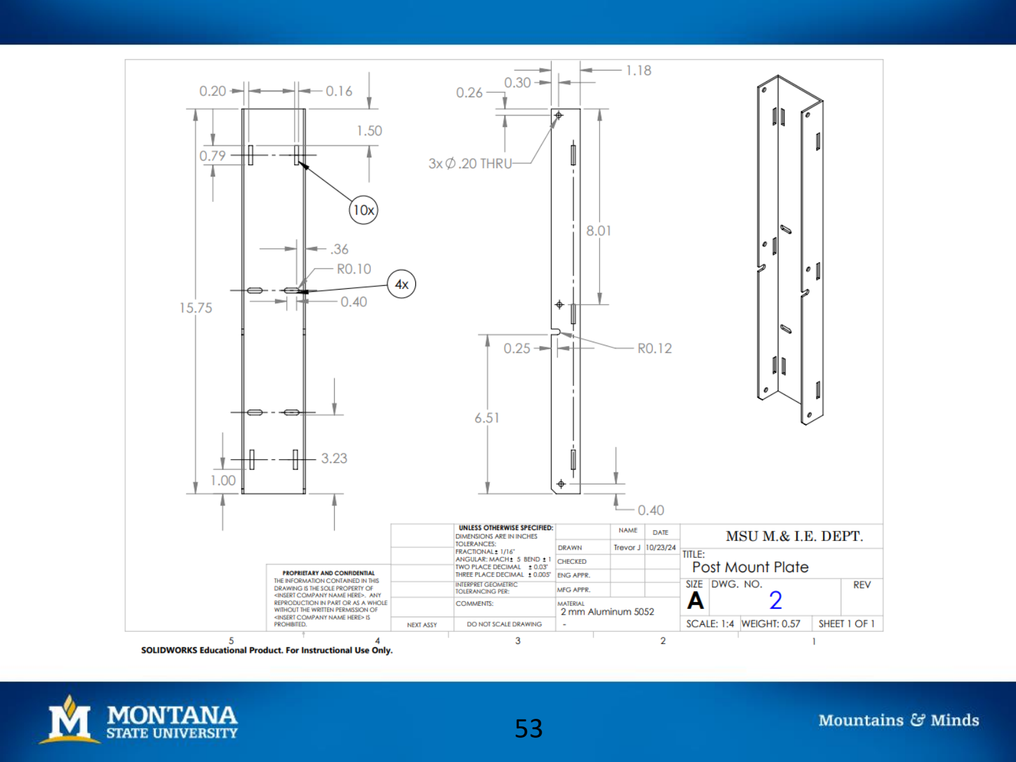
[picture p82: page 53]
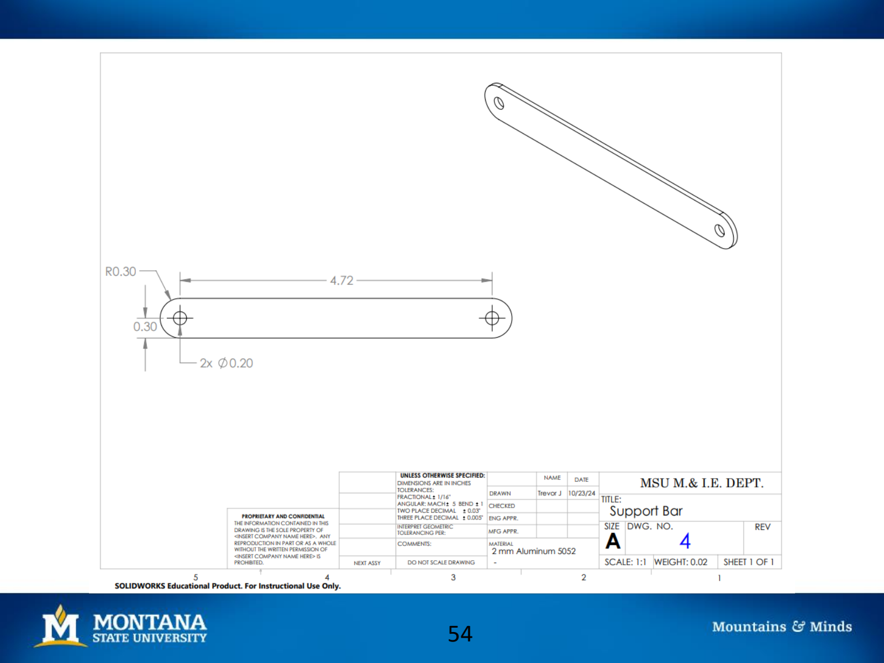
[picture p83: page 54]

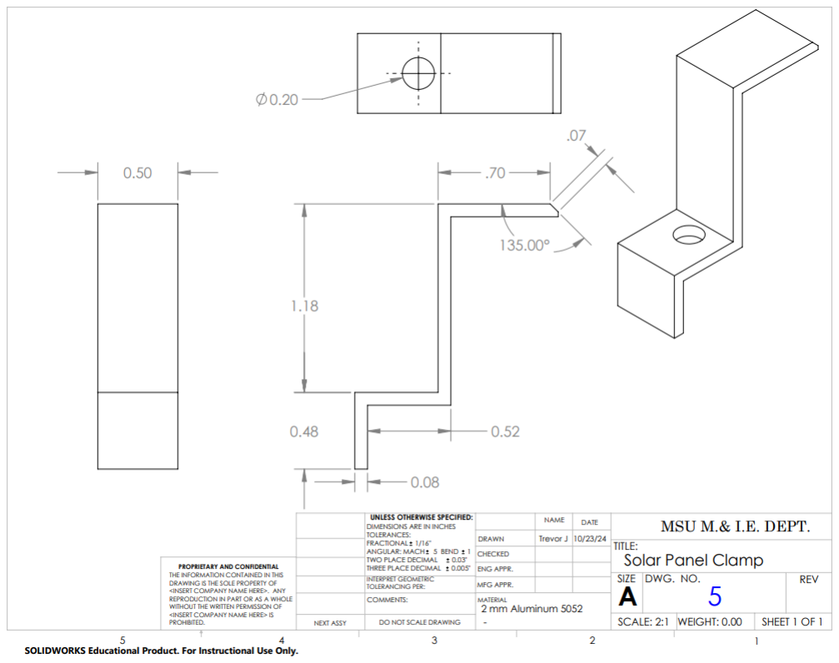
[picture p84: figure]

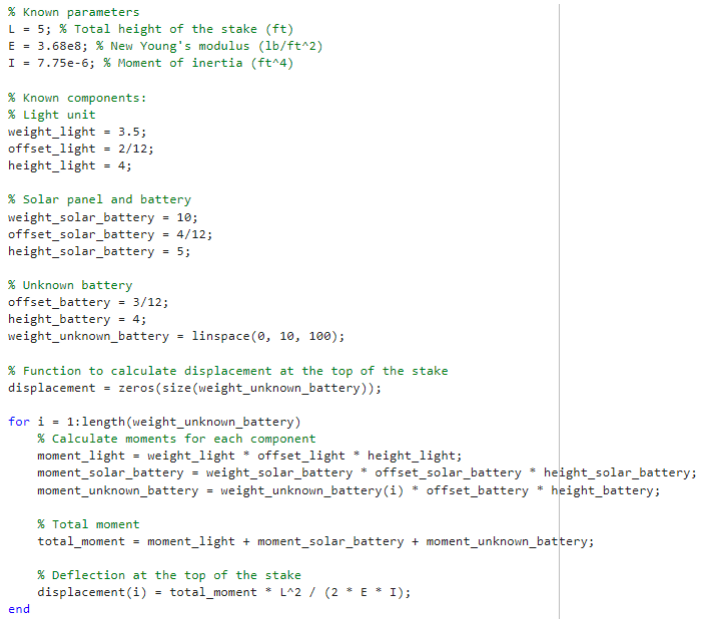
[picture p85: figure]

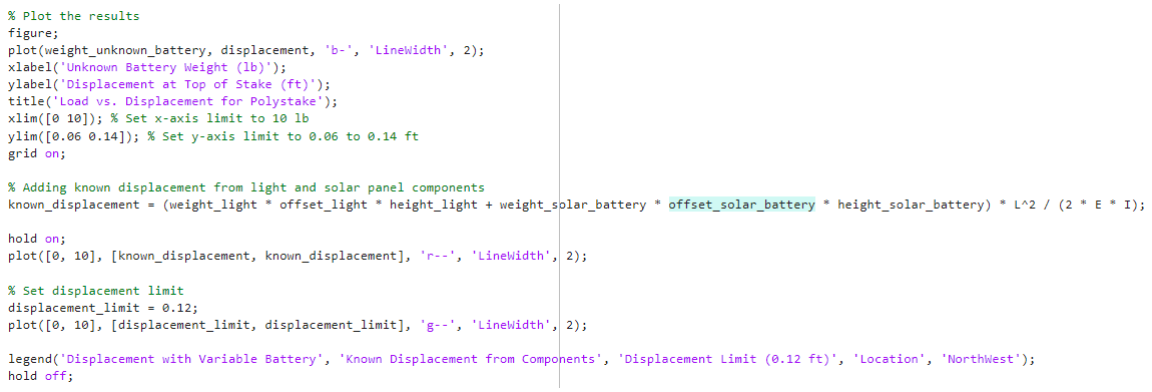
[picture p86: figure]

# Communication Alternative Analysis

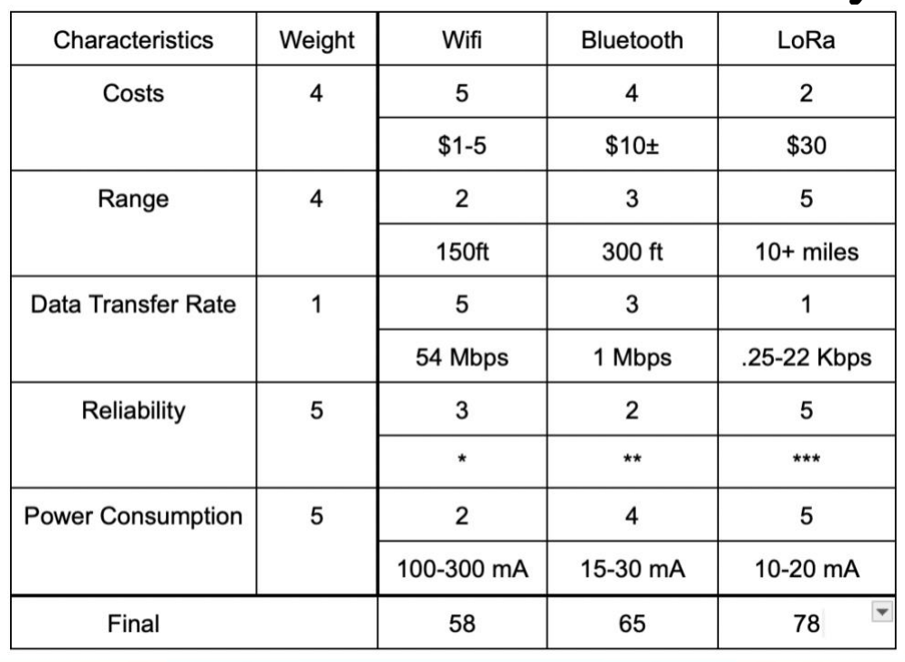
[picture p87: figure]

# Lights Alternative Analysis

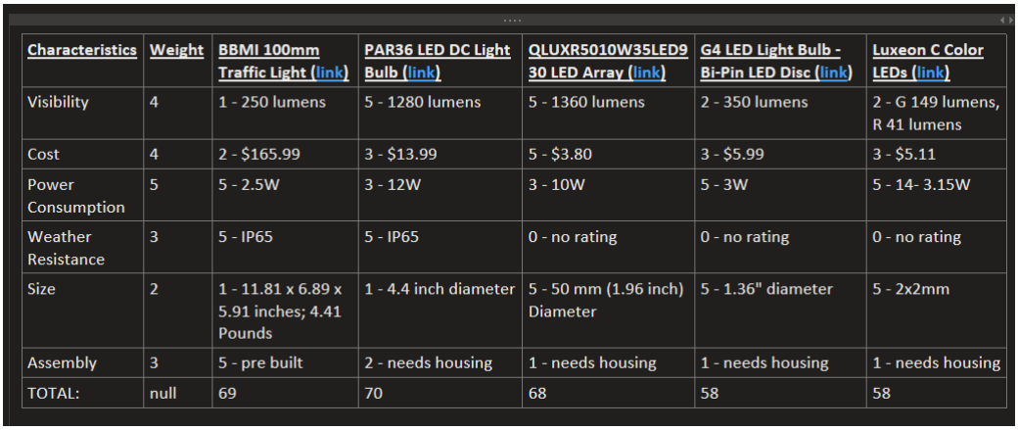
[picture p88: figure]

# Transistor Datasheet Info

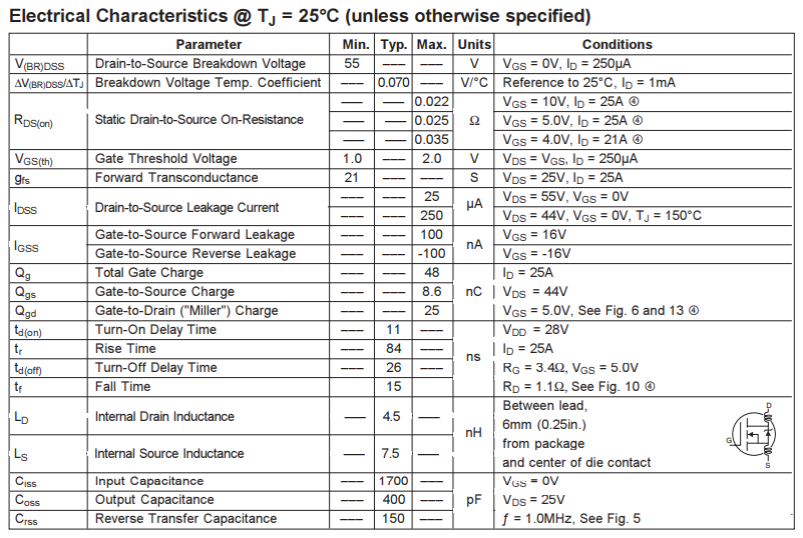
[picture p89: figure]

# Solar Panel Specs

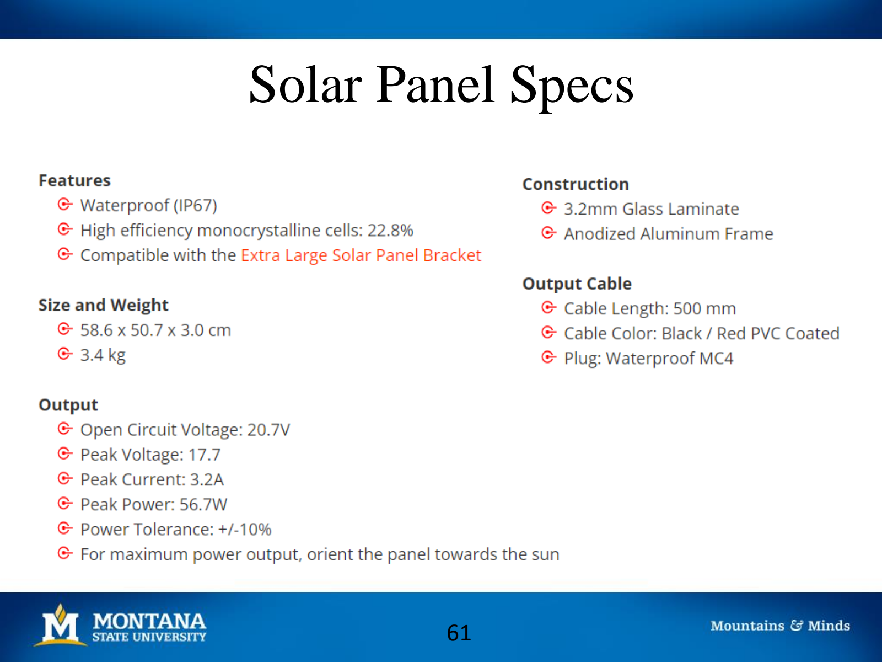
[picture p90: page 61]

# Battery Specs

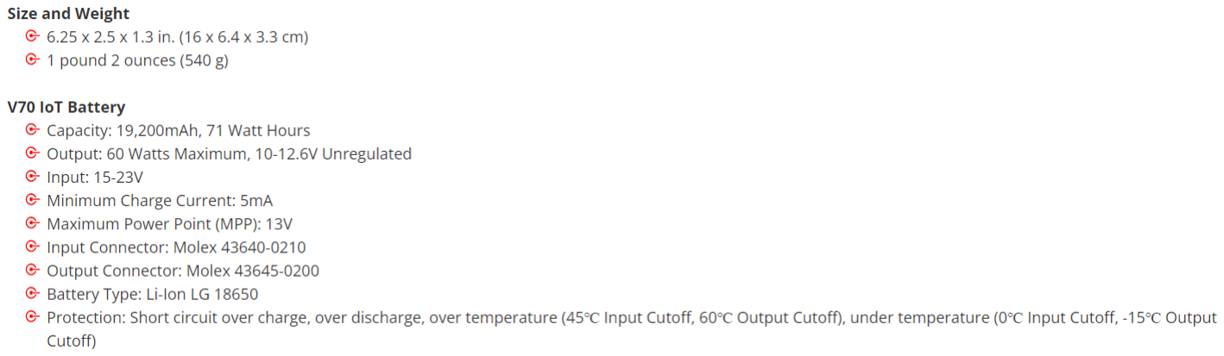
[picture p91: figure]
