EmS228/jumpguard/officialDocuments/MOU_13Jump.pdf

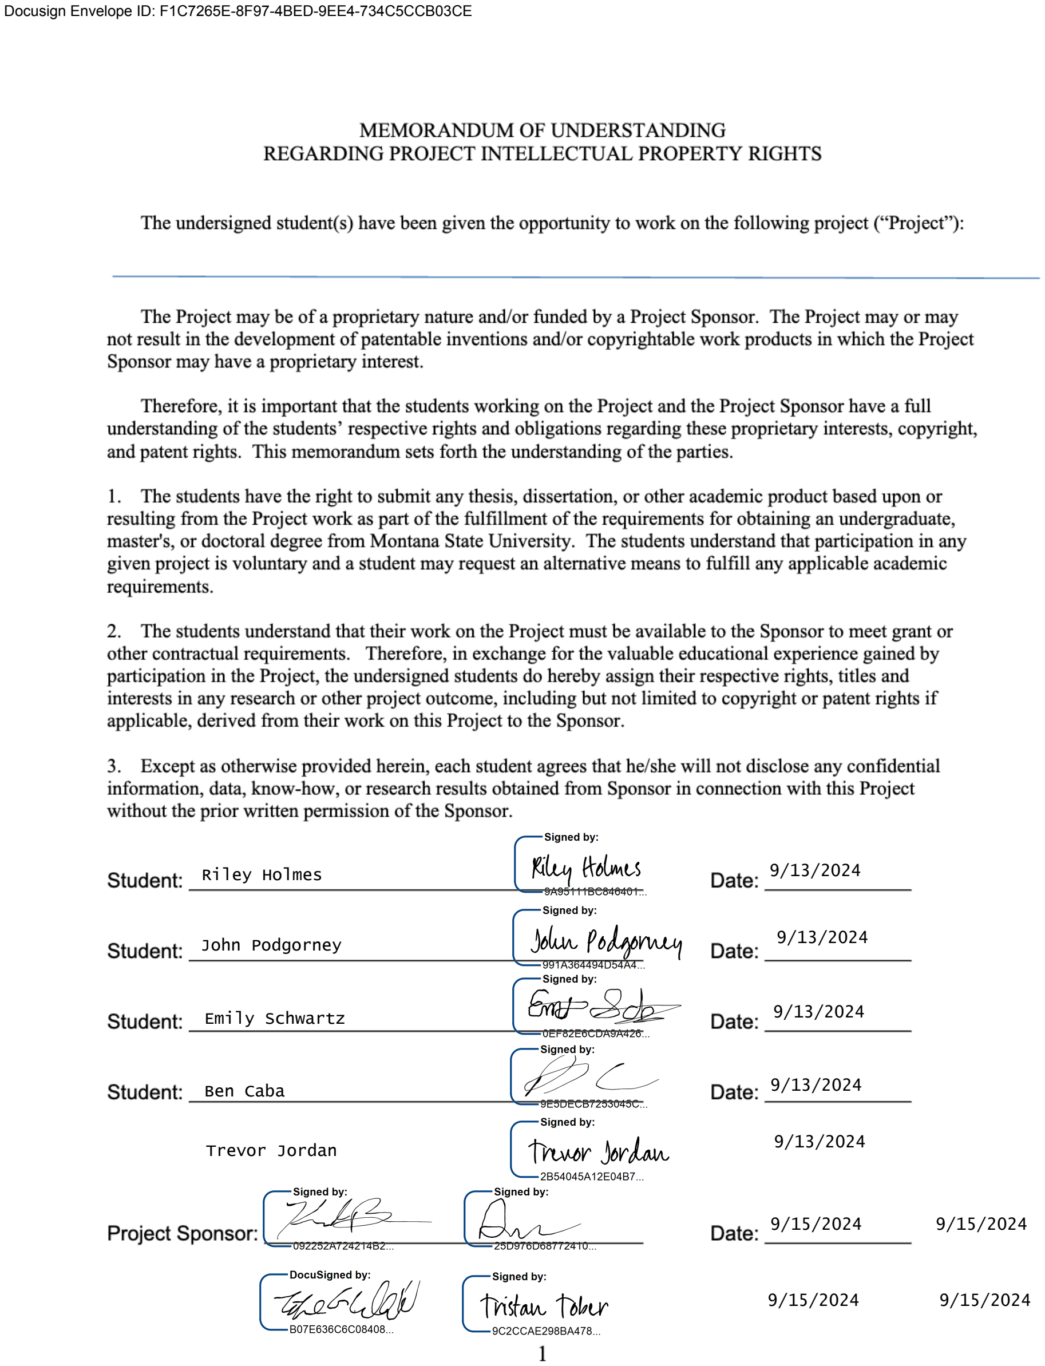
[picture p119: page 1]

Docusign Envelope ID: 840B6EFB-E4FE-4726-BE98-D6FF625C1A49

9/13/2024 Ben Caba

9/13/2024 Emily Schwartz

John Podgorney | 9/13/2024
Riley Holmes | 9/13/2024

9/13/2024 Trevor Jordan

Docusign Envelope ID: F1C7265E-8F97-4BED-9EE4-734C5CCB03CE

9/15/2024 | 9/15/2024
9/15/2024 | 9/15/2024
