EmS228/jumpguard/testing/frames/frameSet1/frame02.png

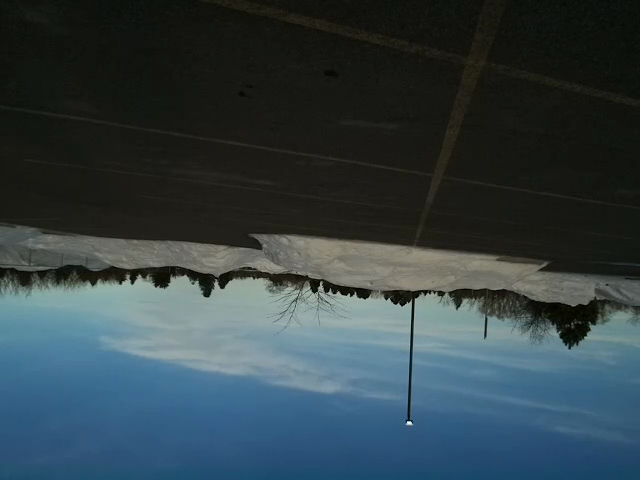
testing/frames/frameSet1/frame02.png
