EmS228/jumpguard/testing/frames/frameSet1/frame12.png

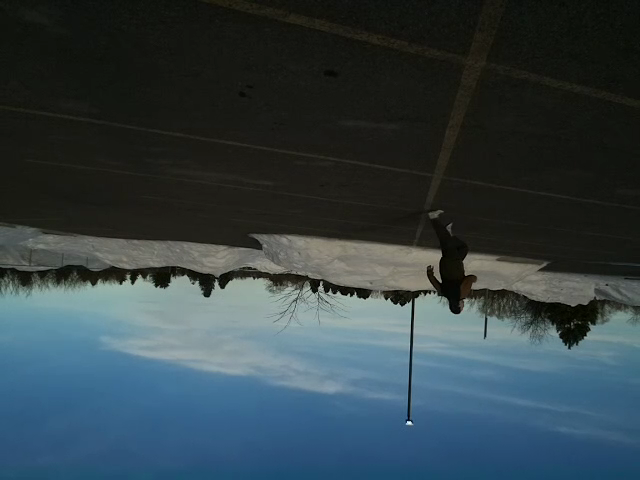
testing/frames/frameSet1/frame12.png
