EmS228/jumpguard/testing/frames/frameSet2/frame04.png

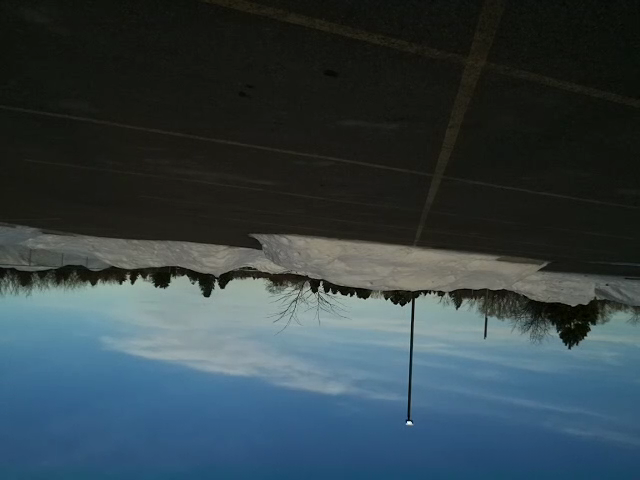
testing/frames/frameSet2/frame04.png
