EmS228/jumpguard/testing/frames/frameSet2/frame09.png

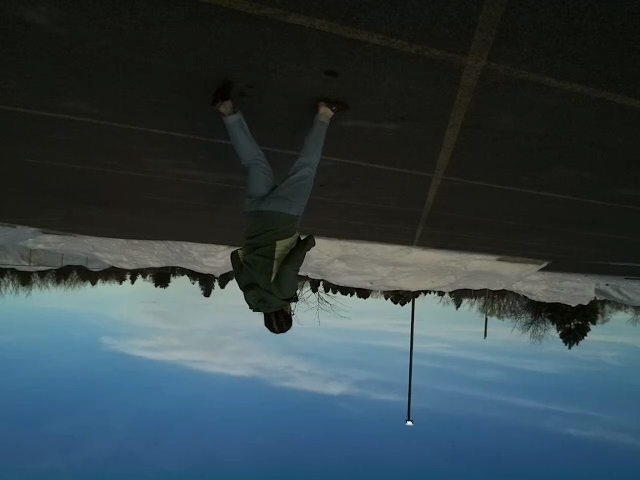
testing/frames/frameSet2/frame09.png
