EmS228/jumpguard/testing/frames/frameSet2/frame10.png

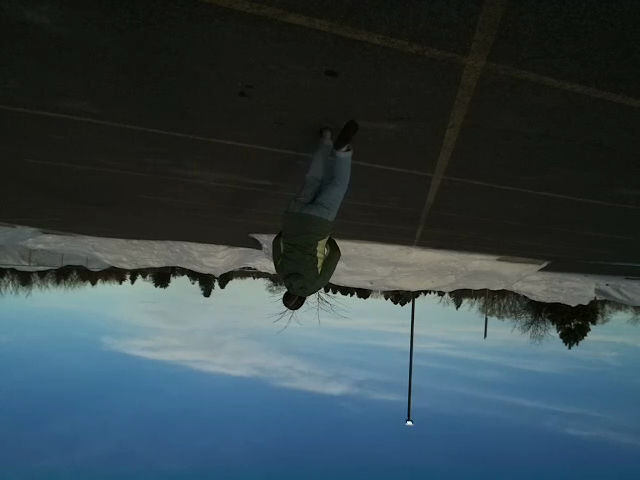
testing/frames/frameSet2/frame10.png
