EmS228/jumpguard/testing/frames/frameSet2/frame13.png

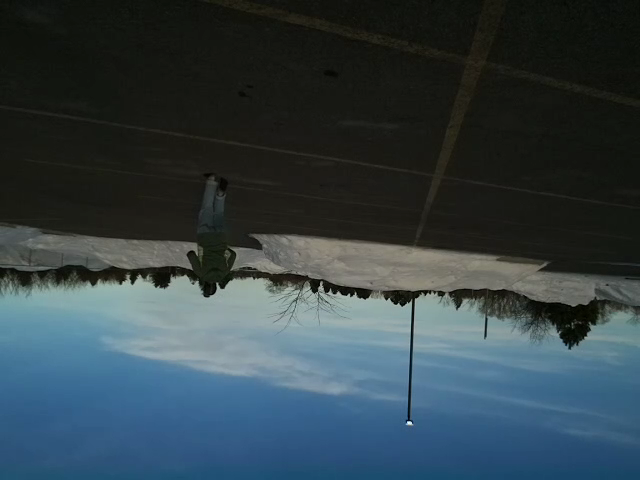
testing/frames/frameSet2/frame13.png
