EmS228/jumpguard/testing/frames/frameSet2/frame16.png

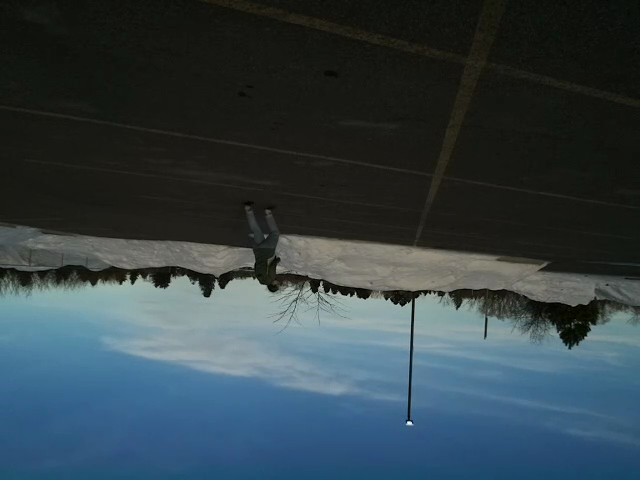
testing/frames/frameSet2/frame16.png
