EmS228/jumpguard/testing/frames/frameSet2/frame17.png

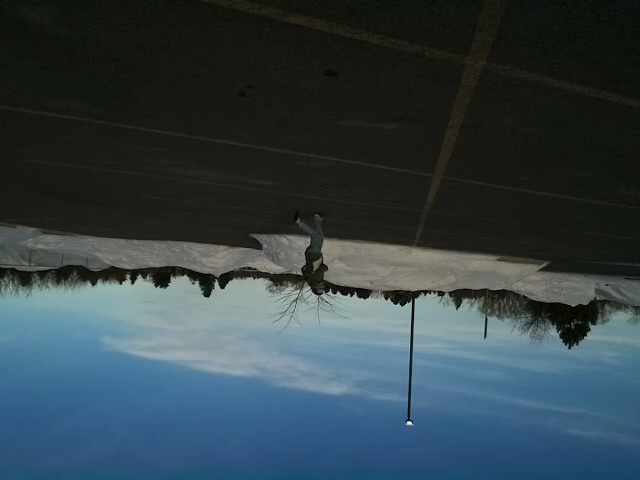
testing/frames/frameSet2/frame17.png
