EmS228/jumpguard/testing/frames/frameSet3/frame02.png

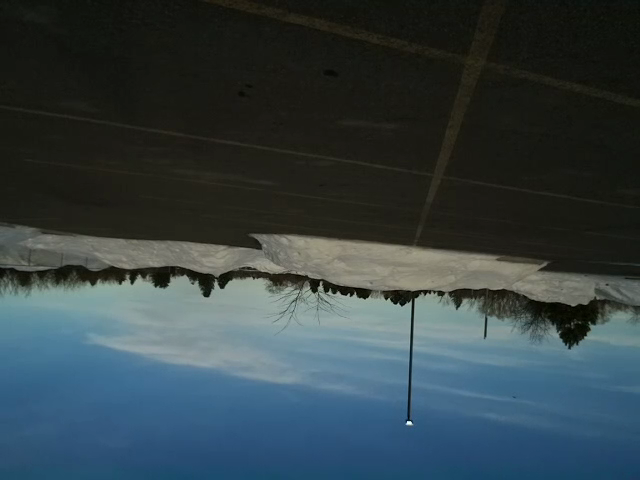
testing/frames/frameSet3/frame02.png
