EmS228/jumpguard/testing/frames/frameSet3/frame11.png

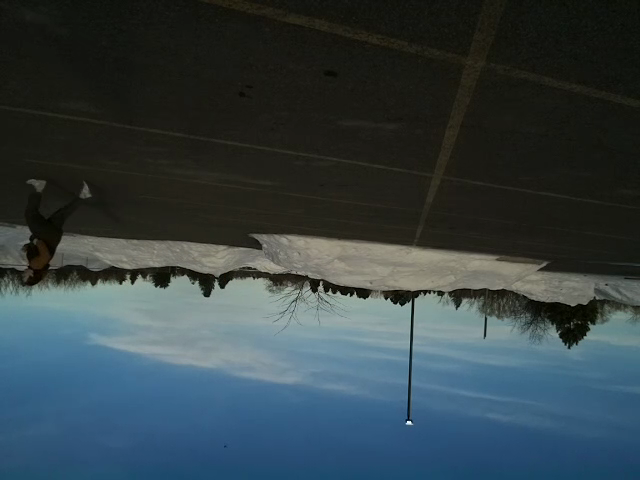
testing/frames/frameSet3/frame11.png
