EmS228/jumpguard/testing/frames/frameSet3/frame19.png

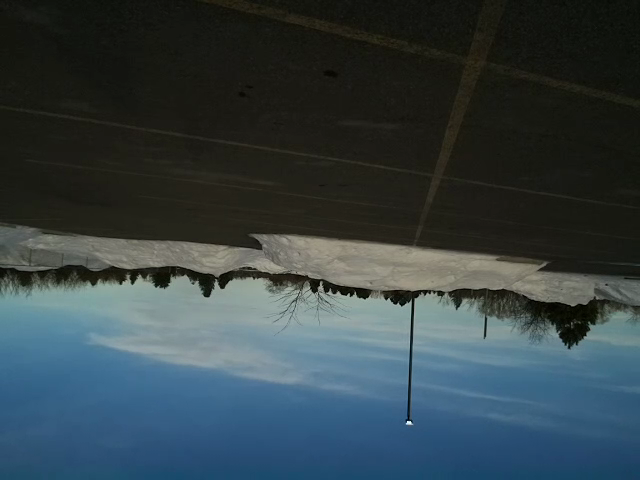
testing/frames/frameSet3/frame19.png
