EmS228/jumpguard/testing/frames/frameSet4/frame06.png

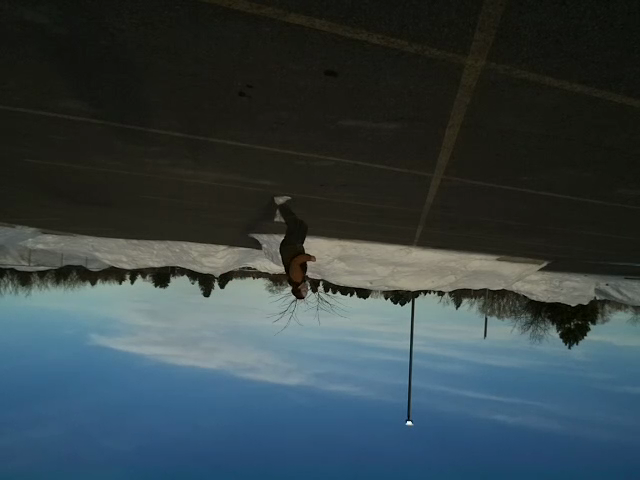
testing/frames/frameSet4/frame06.png
