EmS228/jumpguard/testing/frames/frameSet4/frame07.png

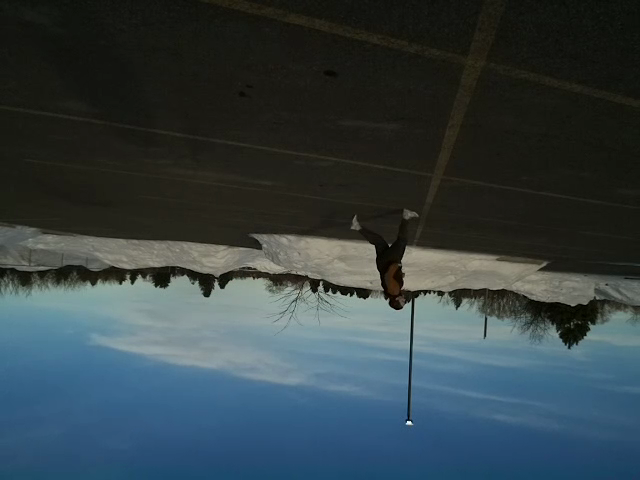
testing/frames/frameSet4/frame07.png
