EmS228/jumpguard/testing/frames/frameSet4/frame08.png

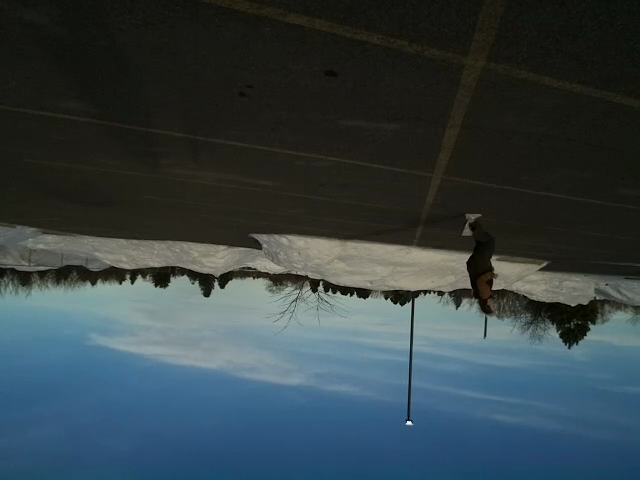
testing/frames/frameSet4/frame08.png
