EmS228/jumpguard/testing/frames/frameSet5/frame03.png

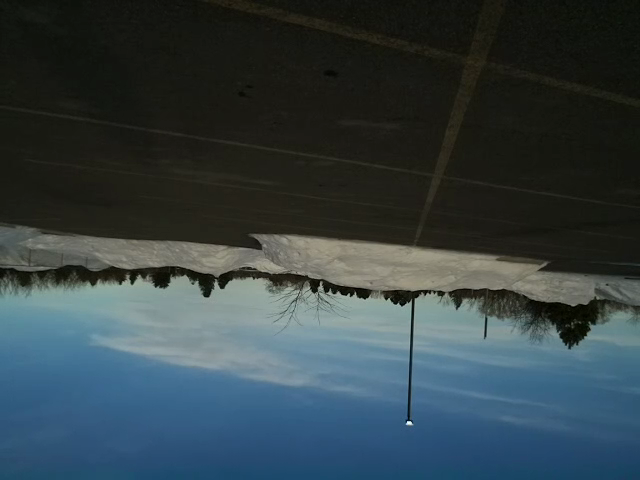
testing/frames/frameSet5/frame03.png
