EmS228/jumpguard/testing/frames/frameSet5/frame11.png

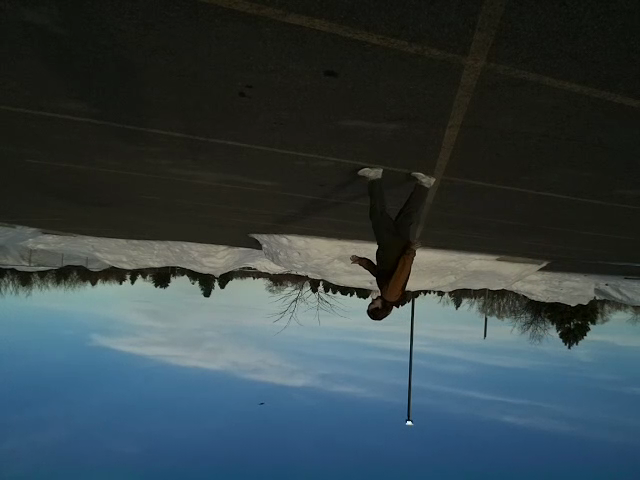
testing/frames/frameSet5/frame11.png
