EmS228/jumpguard/testing/frames/frameSet5/frame13.png

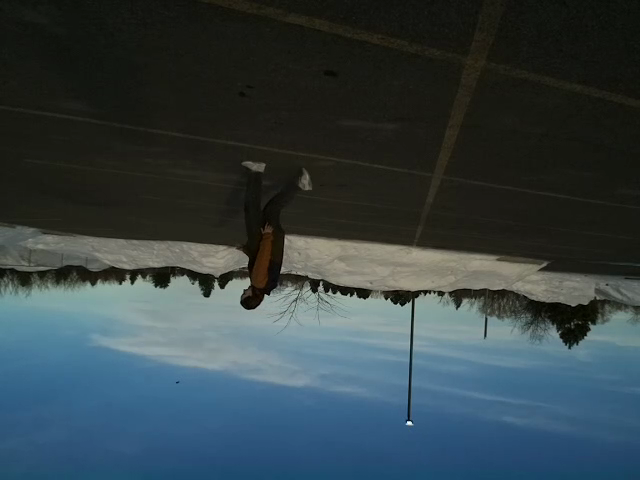
testing/frames/frameSet5/frame13.png
