EmS228/jumpguard/testing/frames/frameSet5/frame15.png

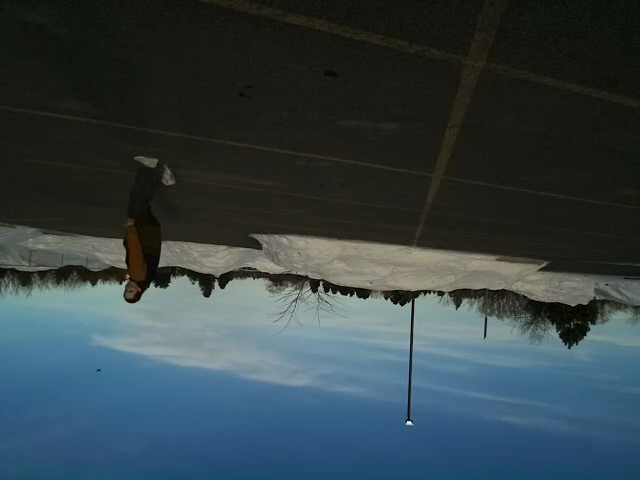
testing/frames/frameSet5/frame15.png
