EmS228/jumpguard/testing/frames/frameSet7/frame05.png

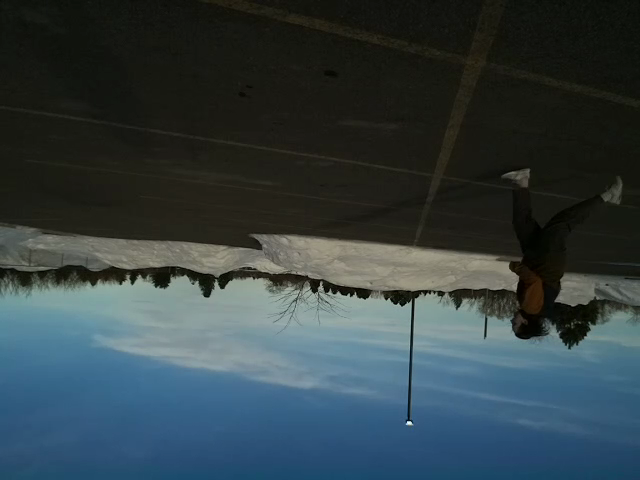
testing/frames/frameSet7/frame05.png
