EmS228/jumpguard/testing/frames/frameSet7/frame08.png

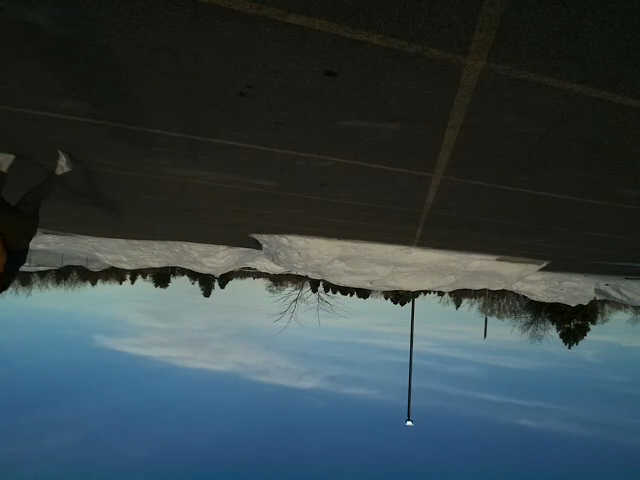
testing/frames/frameSet7/frame08.png
