EmS228/jumpguard/testing/frames/frameSet8/frame07.png

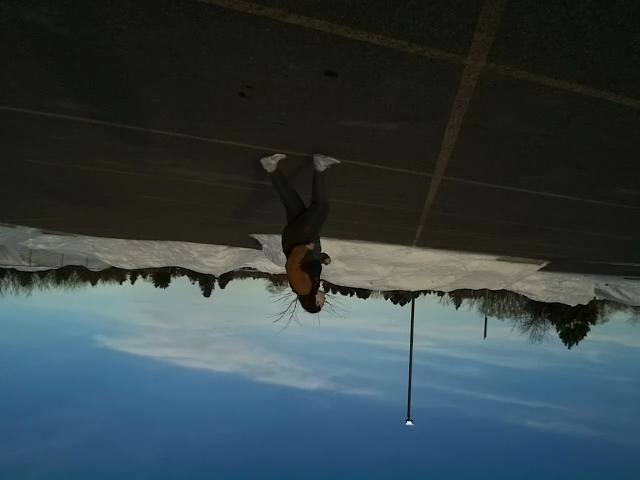
testing/frames/frameSet8/frame07.png
