EmS228/jumpguard/testing/frames/frameSet10/frame05.png

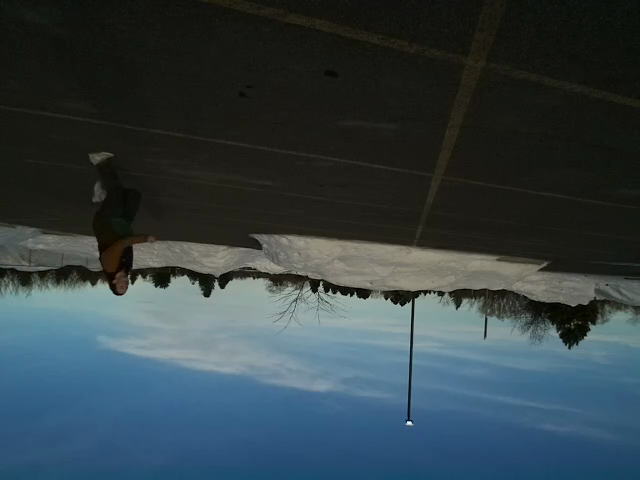
testing/frames/frameSet10/frame05.png
