EmS228/jumpguard/testing/frames/frameSet10/frame06.png

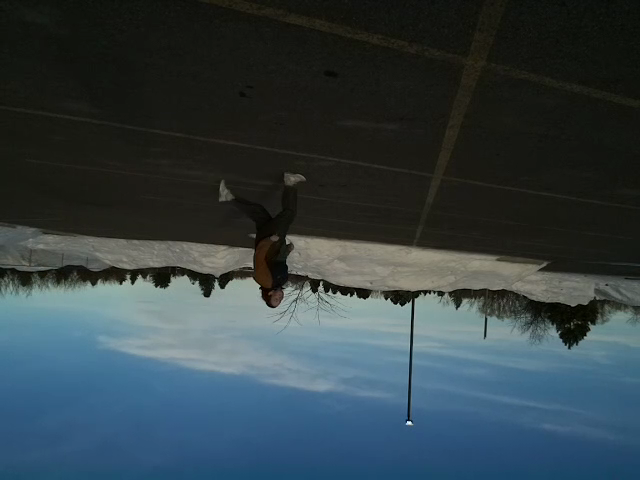
testing/frames/frameSet10/frame06.png
