EmS228/jumpguard/testing/frames/frameSet10/frame07.png

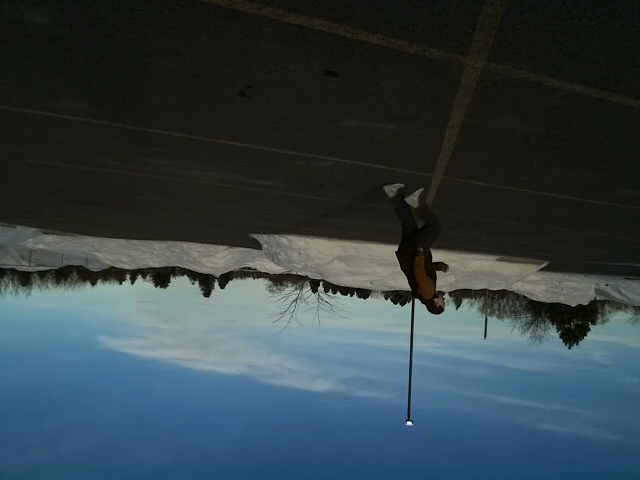
testing/frames/frameSet10/frame07.png
