EmS228/jumpguard/testing/frames/frameSet11/frame15.png

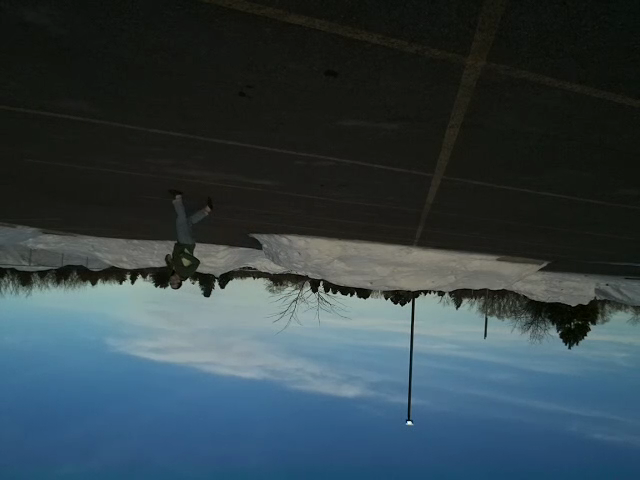
testing/frames/frameSet11/frame15.png
