EmS228/jumpguard/testing/frames/frameSet12/frame04.png

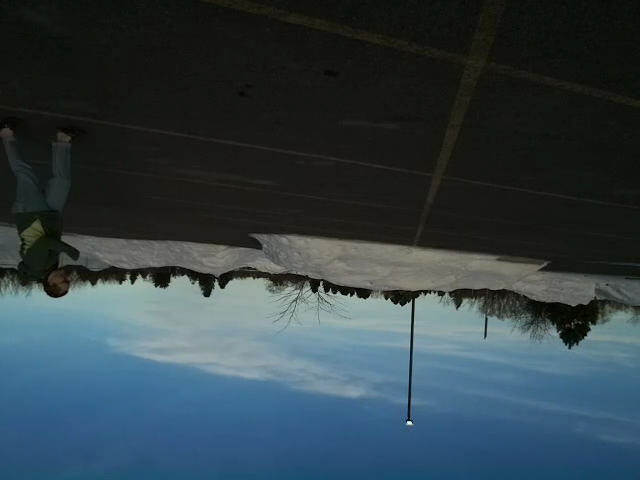
testing/frames/frameSet12/frame04.png
