EmS228/jumpguard/testing/frames/frameSet12/frame05.png

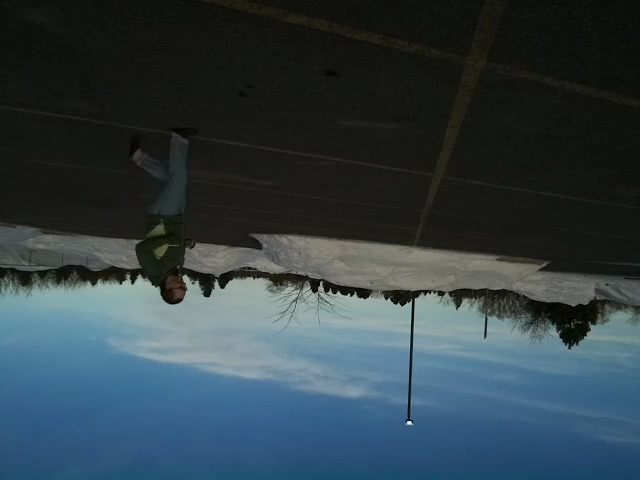
testing/frames/frameSet12/frame05.png
