EmS228/jumpguard/testing/frames/frameSet12/frame06.png

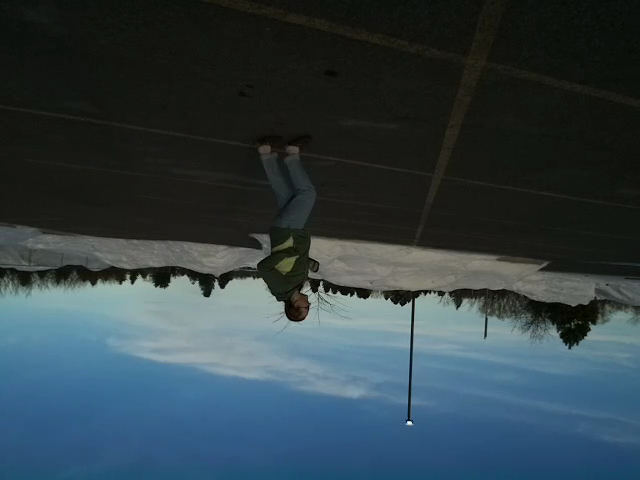
testing/frames/frameSet12/frame06.png
