EmS228/jumpguard/testing/frames/frameSet13/frame08.png

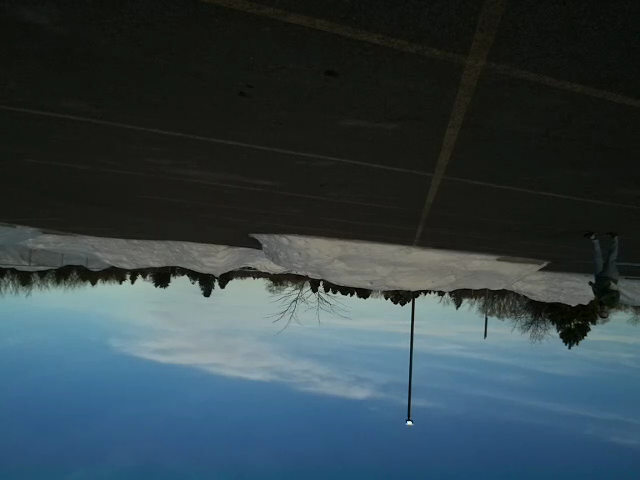
testing/frames/frameSet13/frame08.png
