EmS228/jumpguard/testing/frames/frameSet13/frame20.png

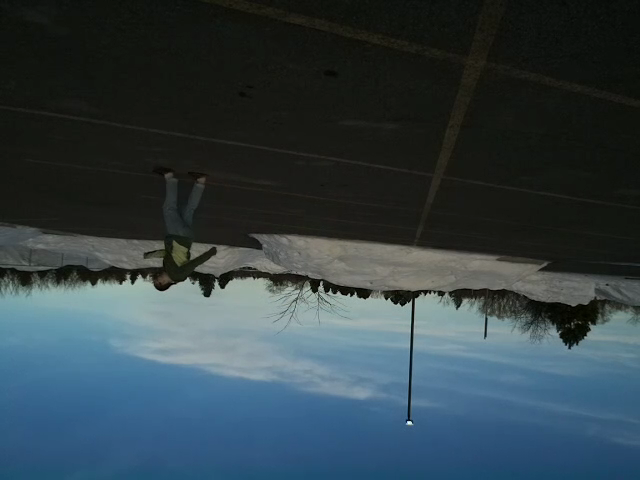
testing/frames/frameSet13/frame20.png
