EmS228/jumpguard/testing/frames/frameSet14/frame17.png

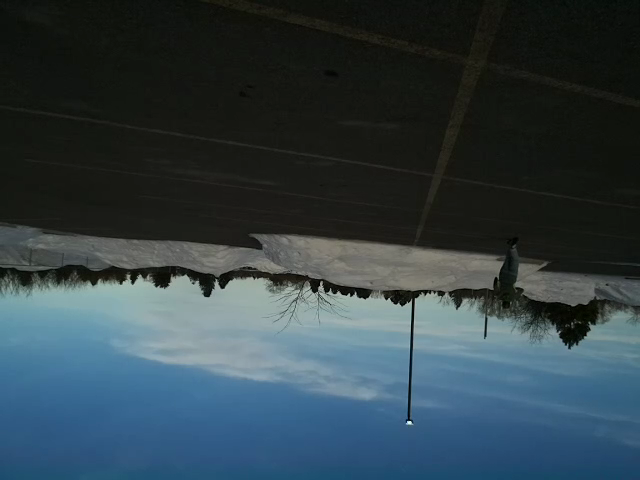
testing/frames/frameSet14/frame17.png
