EmS228/jumpguard/testing/frames/frameSet15/frame11.png

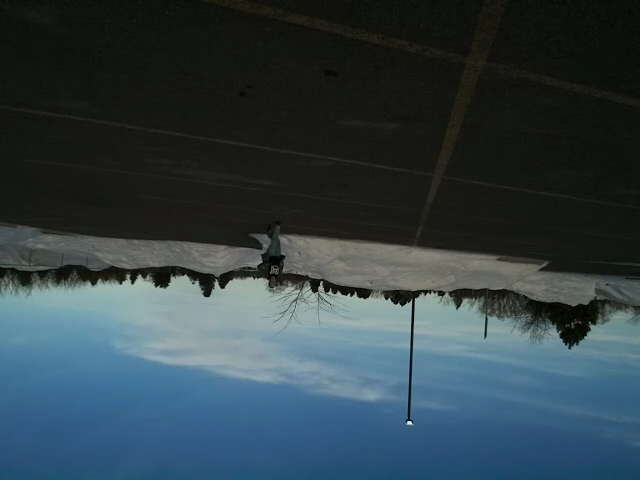
testing/frames/frameSet15/frame11.png
