EmS228/jumpguard/testing/frames/frameSet15/frame13.png

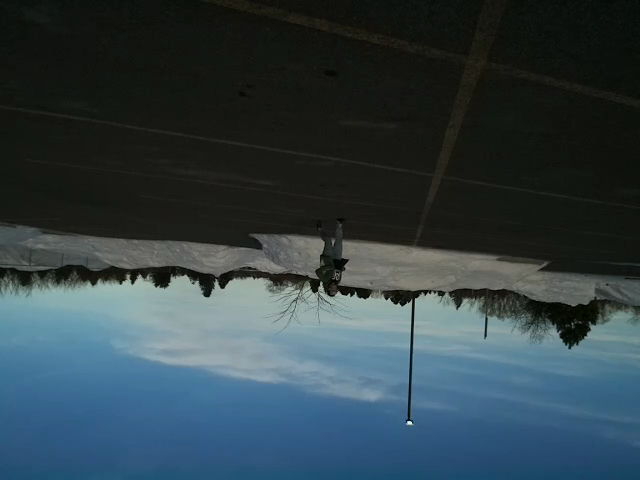
testing/frames/frameSet15/frame13.png
