EmS228/jumpguard/testing/frames/frameSet16/frame01.png

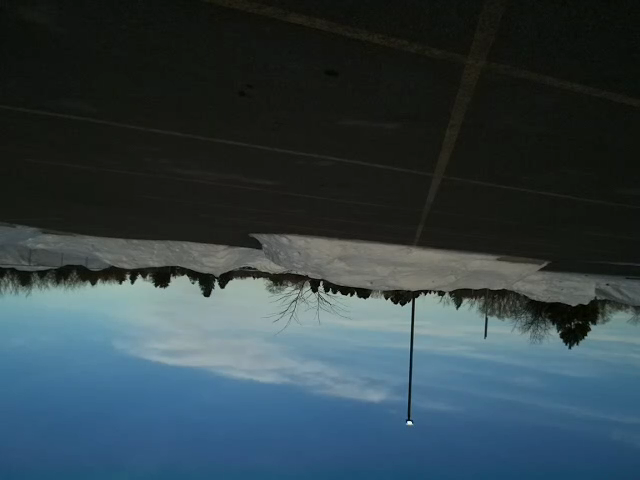
testing/frames/frameSet16/frame01.png
