EmS228/jumpguard/testing/frames/frameSet16/frame02.png

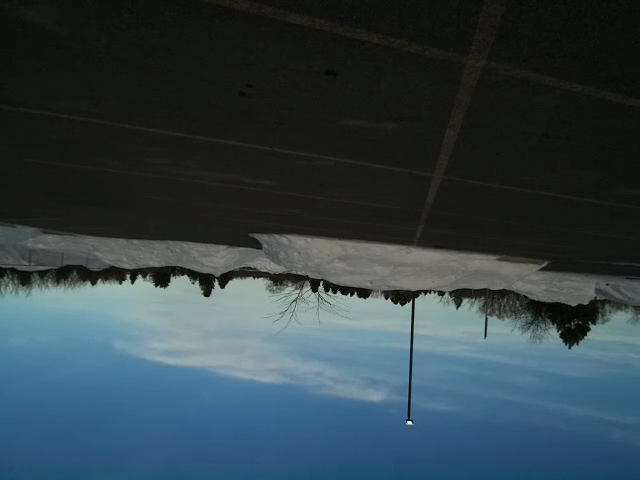
testing/frames/frameSet16/frame02.png
