EmS228/jumpguard/testing/frames/frameSet16/frame11.png

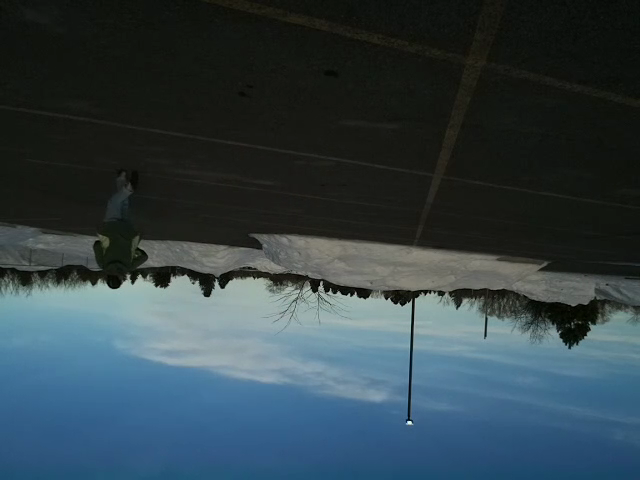
testing/frames/frameSet16/frame11.png
