EmS228/jumpguard/testing/frames/frameSet16/frame12.png

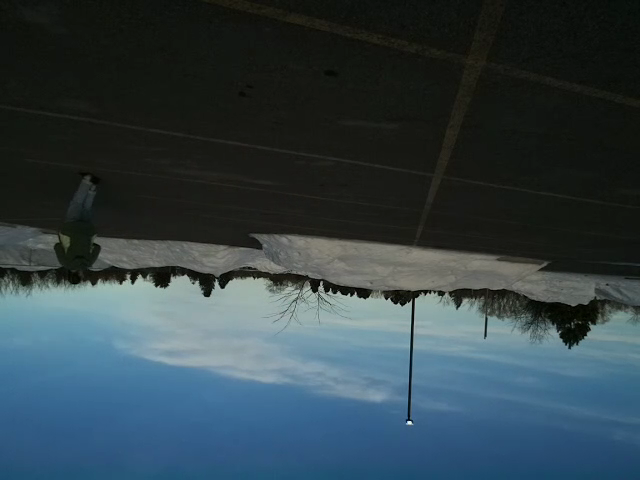
testing/frames/frameSet16/frame12.png
