EmS228/jumpguard/testing/frames/frameSet16/frame16.png

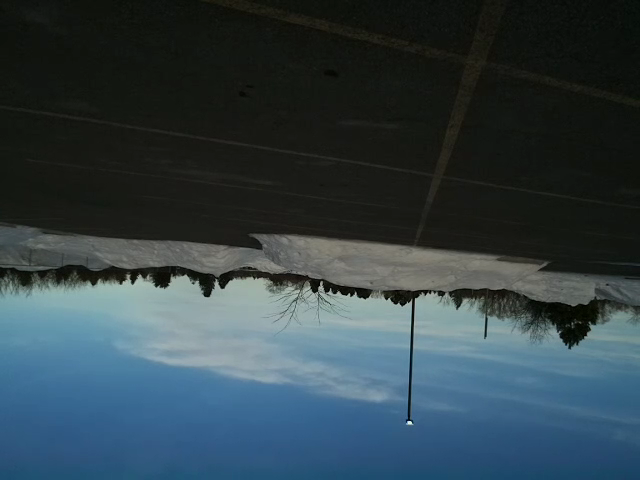
testing/frames/frameSet16/frame16.png
