EmS228/jumpguard/testing/frames/frameSet17/frame03.png

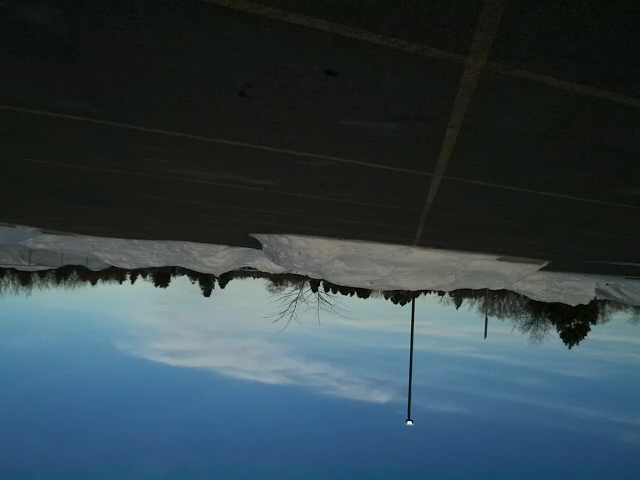
testing/frames/frameSet17/frame03.png
