EmS228/jumpguard/testing/frames/frameSet17/frame06.png

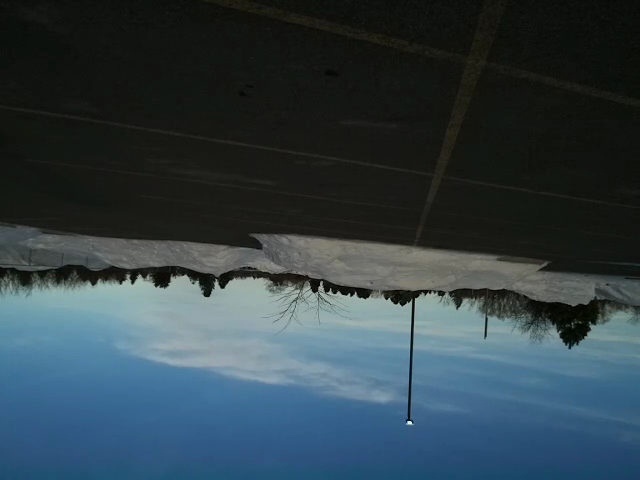
testing/frames/frameSet17/frame06.png
