EmS228/jumpguard/testing/frames/frameSet17/frame07.png

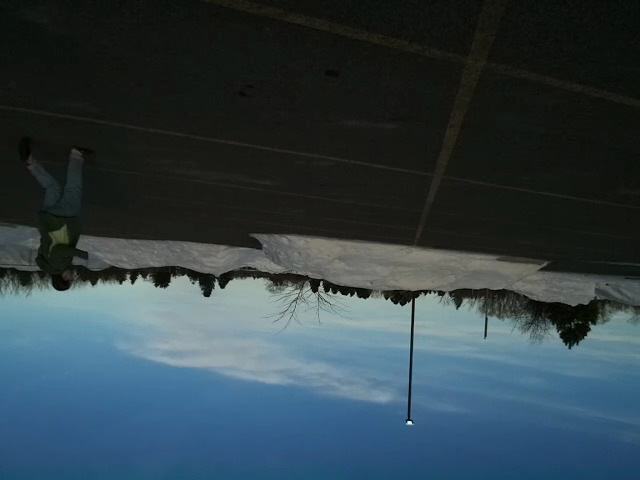
testing/frames/frameSet17/frame07.png
