EmS228/jumpguard/testing/frames/frameSet17/frame11.png

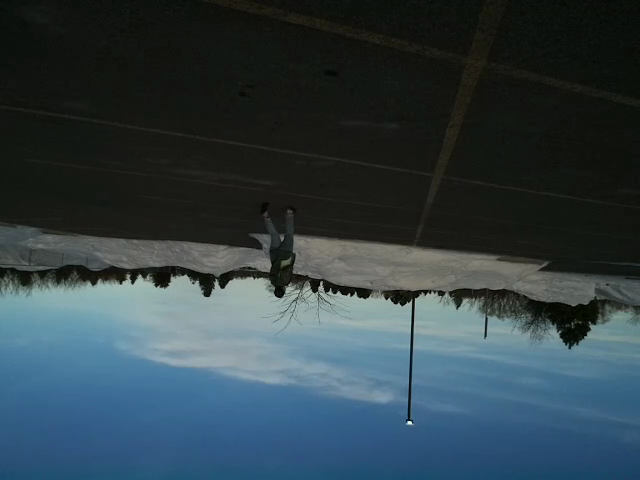
testing/frames/frameSet17/frame11.png
