EmS228/jumpguard/testing/frames/frameSet17/frame14.png

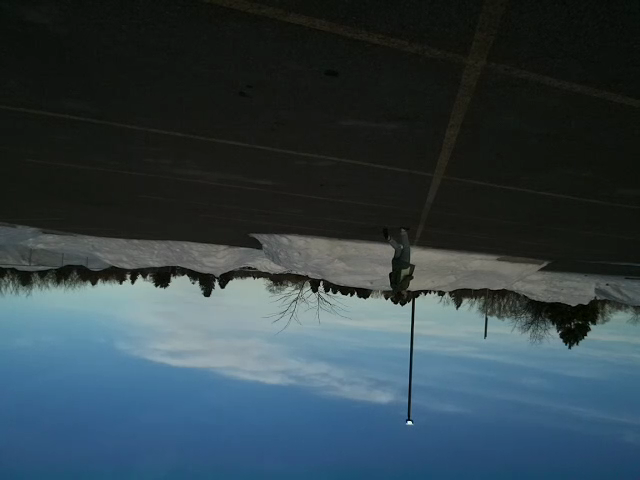
testing/frames/frameSet17/frame14.png
