EmS228/jumpguard/testing/frames/frameSet18/frame10.png

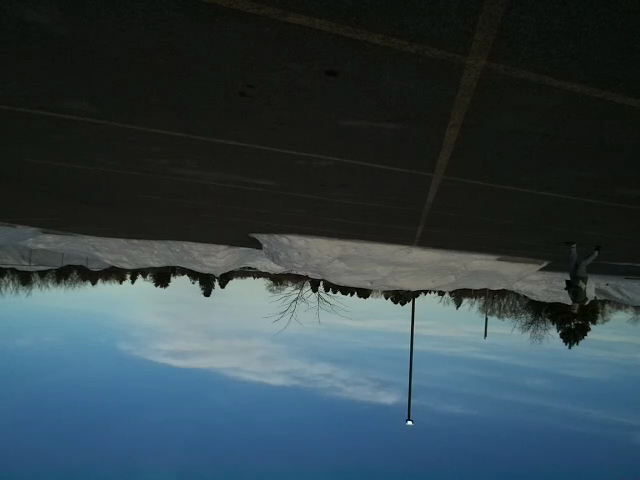
testing/frames/frameSet18/frame10.png
