EmS228/jumpguard/testing/frames/frameSet18/frame18.png

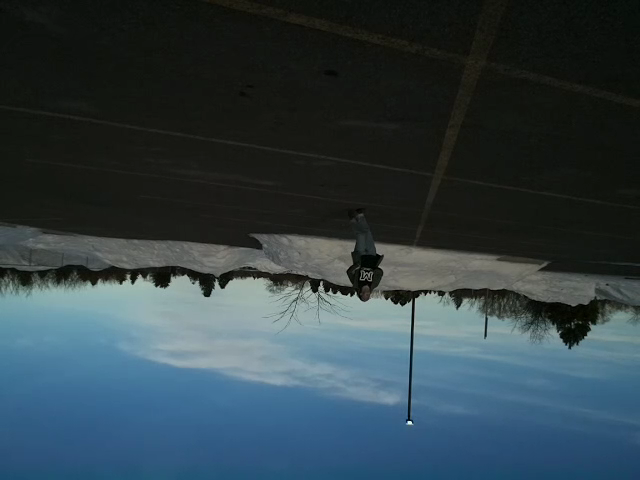
testing/frames/frameSet18/frame18.png
