EmS228/jumpguard/testing/frames/frameSet18/frame20.png

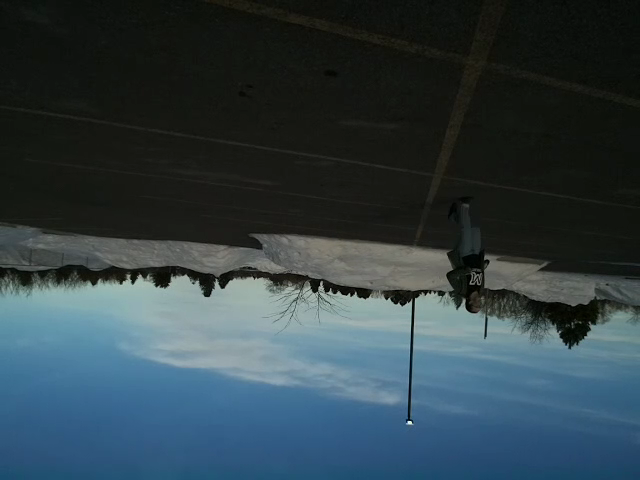
testing/frames/frameSet18/frame20.png
