EmS228/jumpguard/testing/frames/frameSet19/frame04.png

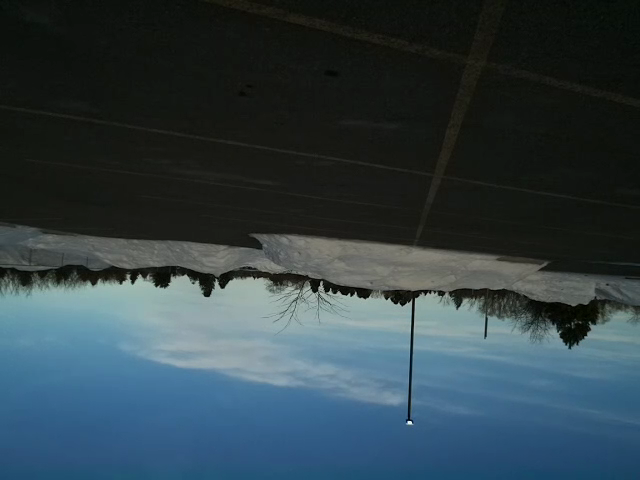
testing/frames/frameSet19/frame04.png
