EmS228/jumpguard/testing/frames/frameSet19/frame10.png

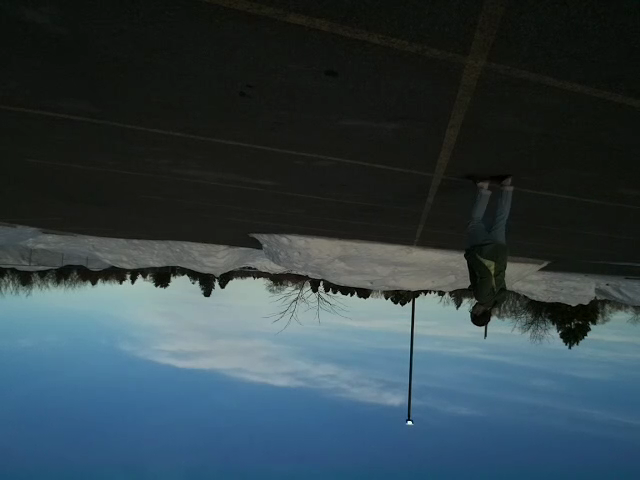
testing/frames/frameSet19/frame10.png
