EmS228/jumpguard/testing/frames/frameSet19/frame11.png

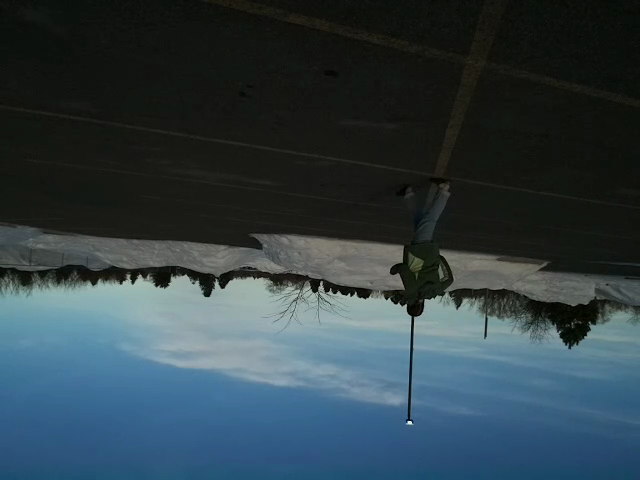
testing/frames/frameSet19/frame11.png
