EmS228/jumpguard/testing/frames/frameSet20/frame01.png

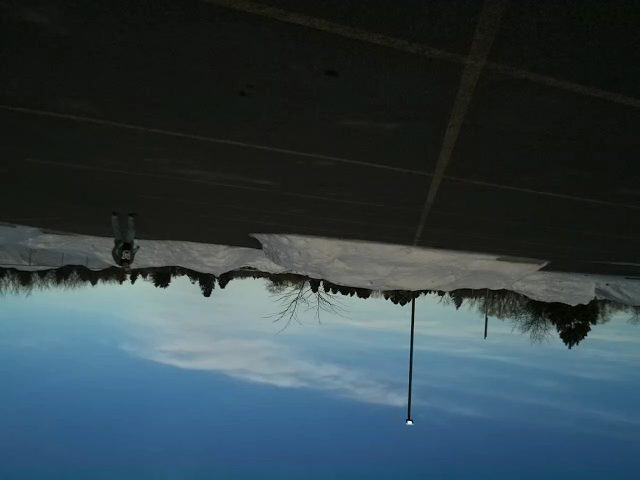
testing/frames/frameSet20/frame01.png
