EmS228/jumpguard/testing/frames/frameSet20/frame07.png

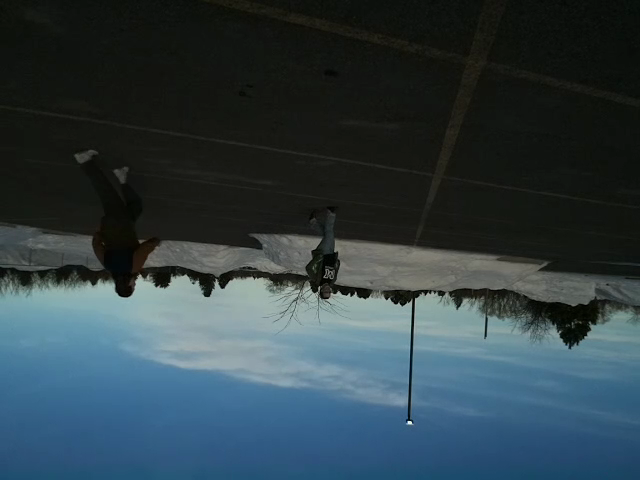
testing/frames/frameSet20/frame07.png
