EmS228/jumpguard/testing/frames/frameSet20/frame08.png

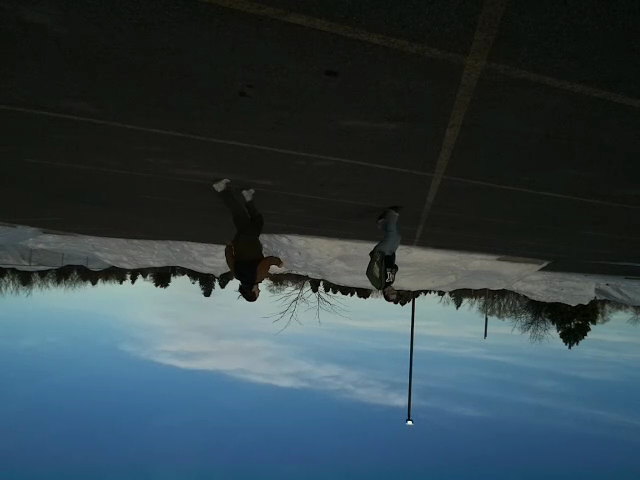
testing/frames/frameSet20/frame08.png
