EmS228/jumpguard/testing/frames/frameSet20/frame10.png

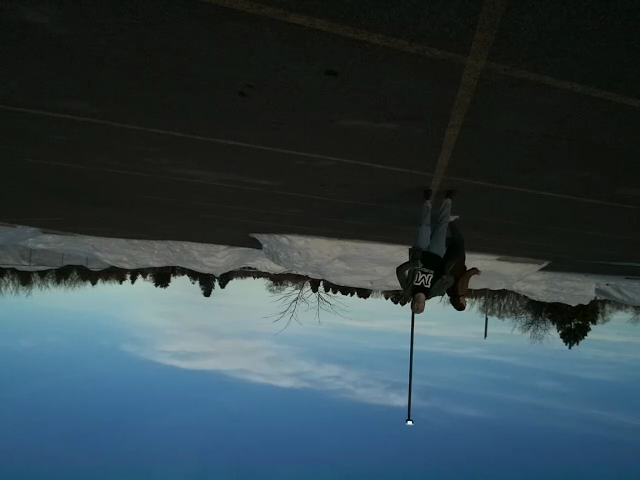
testing/frames/frameSet20/frame10.png
