EmS228/jumpguard/testing/frames/frameSet20/frame14.png

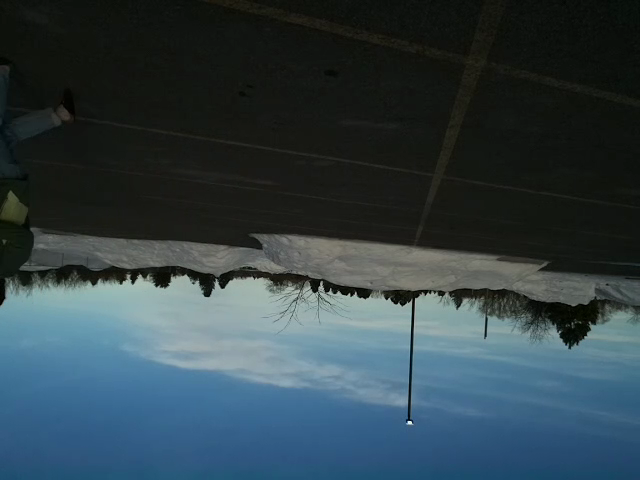
testing/frames/frameSet20/frame14.png
