EmS228/jumpguard/testing/frames/frameSet20/frame15.png

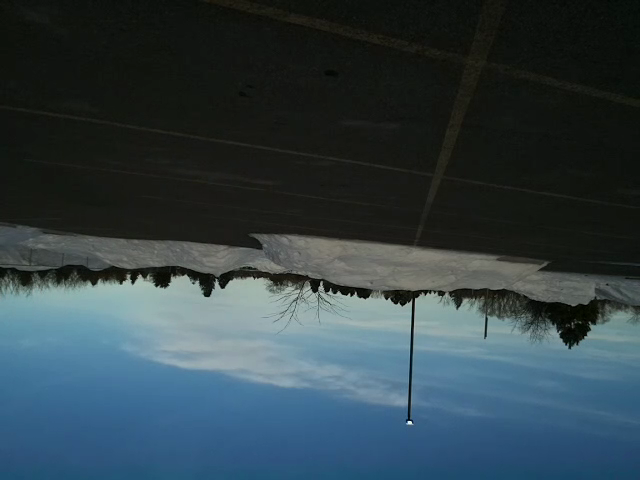
testing/frames/frameSet20/frame15.png
