EmS228/jumpguard/testing/frames/Test2/framesTest6/frame_11.png

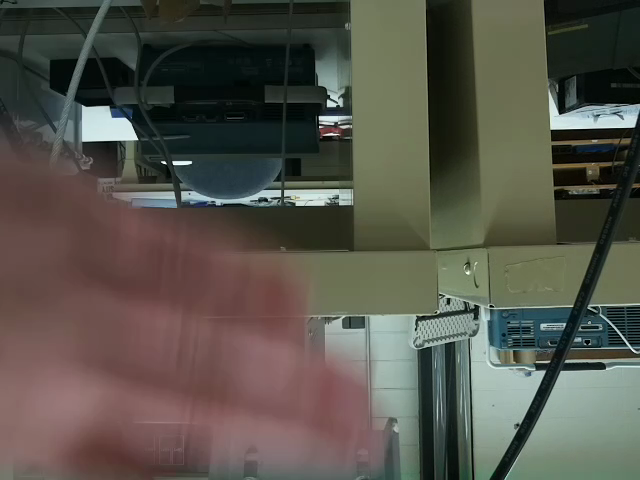
testing/frames/Test2/framesTest6/frame_11.png
