EmS228/jumpguard/testing/frames/Test2/framesTest6/frame_13.png

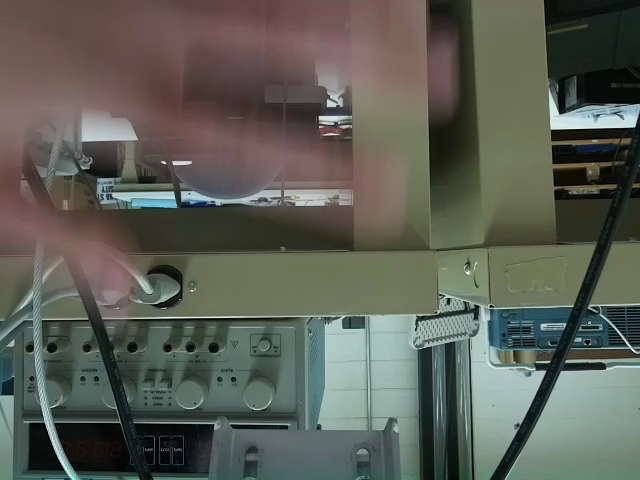
testing/frames/Test2/framesTest6/frame_13.png
