EmS228/jumpguard/testing/frames/Test2/framesTest11/frame_04.png

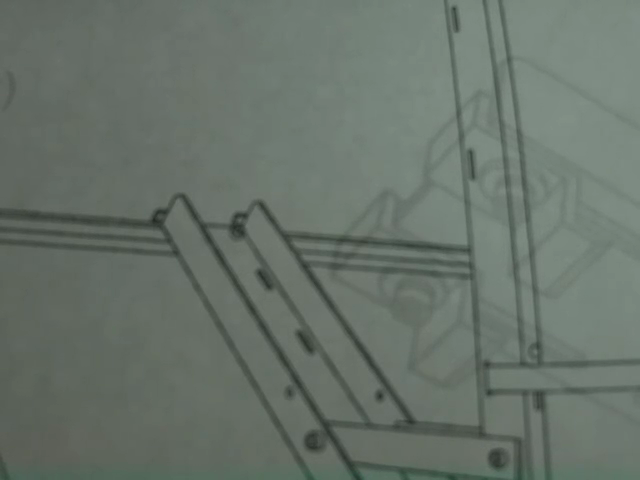
testing/frames/Test2/framesTest11/frame_04.png
