EmS228/jumpguard/testing/imageTest2/imageSet_01.bmp

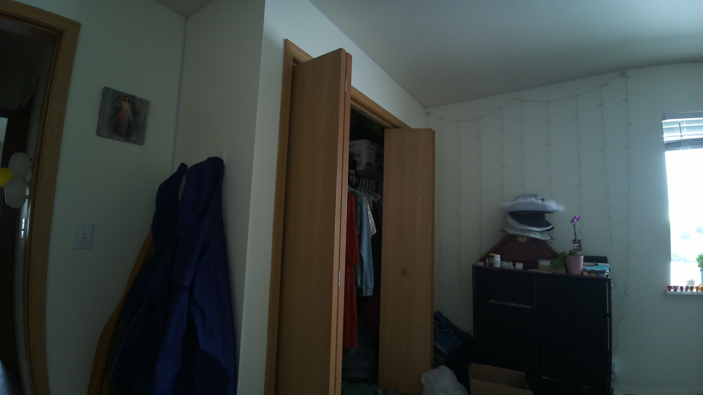
testing/imageTest2/imageSet_01.bmp
