EmS228/jumpguard/testing/series/frames/frame1_02.png

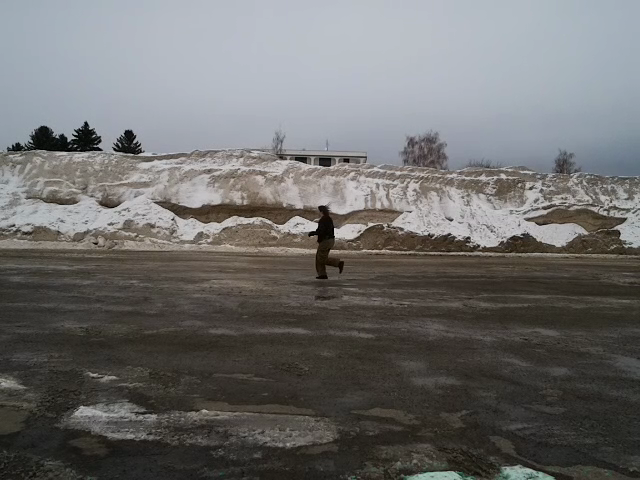
testing/series/frames/frame1_02.png
