EmS228/jumpguard/testing/series/frames/frame1_06.png

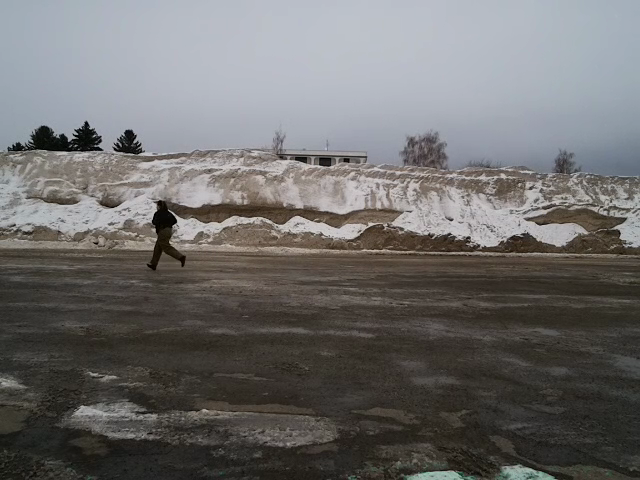
testing/series/frames/frame1_06.png
