EmS228/jumpguard/testing/series/frames/frame1_07.png

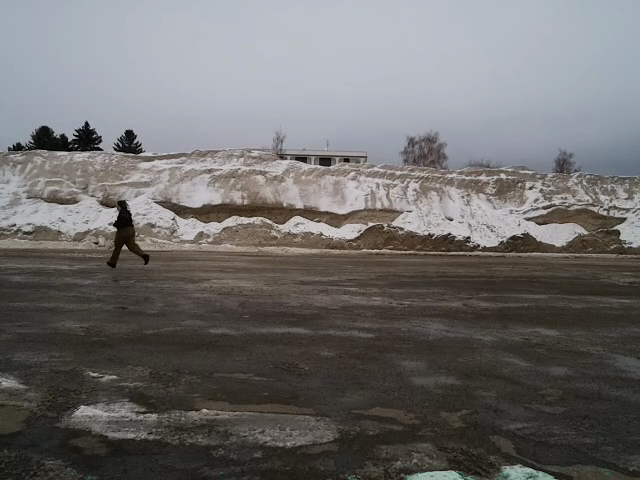
testing/series/frames/frame1_07.png
