EmS228/jumpguard/testing/series/frames/frame1_10.png

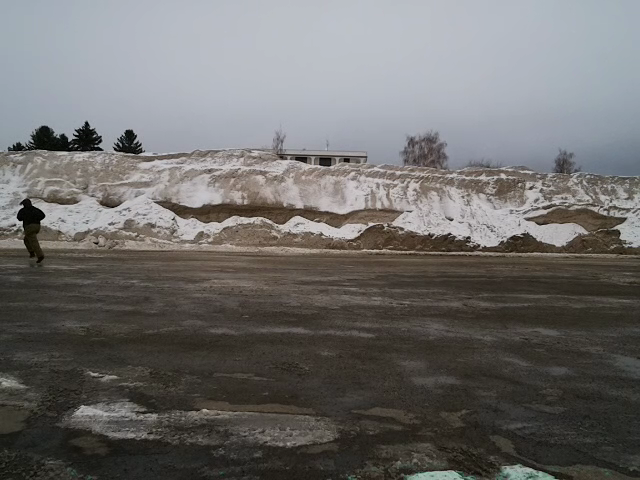
testing/series/frames/frame1_10.png
