EmS228/jumpguard/testing/series/frames/frame1_14.png

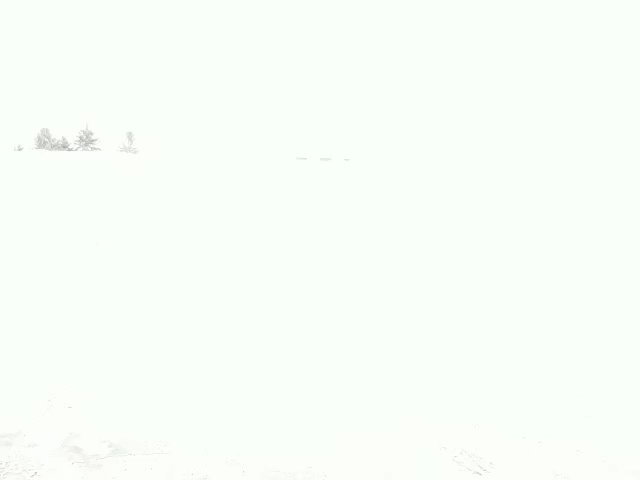
testing/series/frames/frame1_14.png
