EmS228/jumpguard/testing/series/frames/frame2_01.png

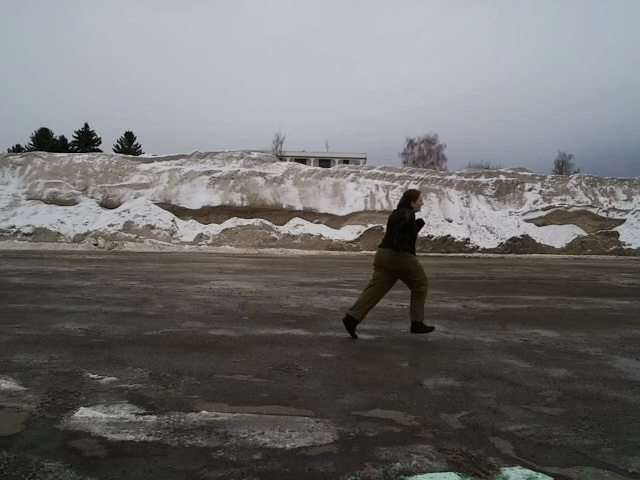
testing/series/frames/frame2_01.png
