EmS228/jumpguard/testing/series/frames/frame2_02.png

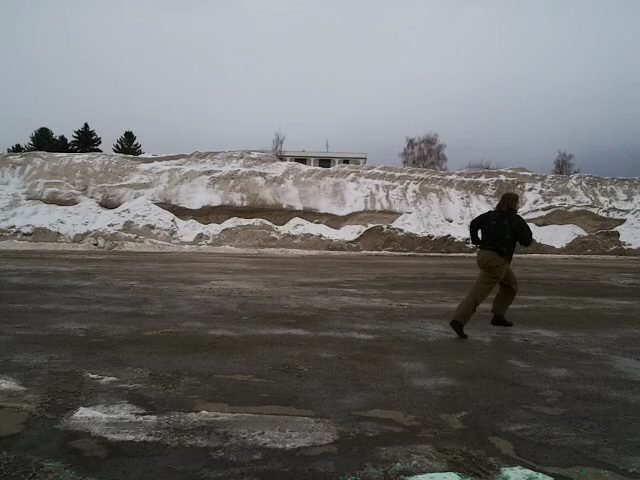
testing/series/frames/frame2_02.png
