EmS228/jumpguard/testing/series/frames/frame2_06.png

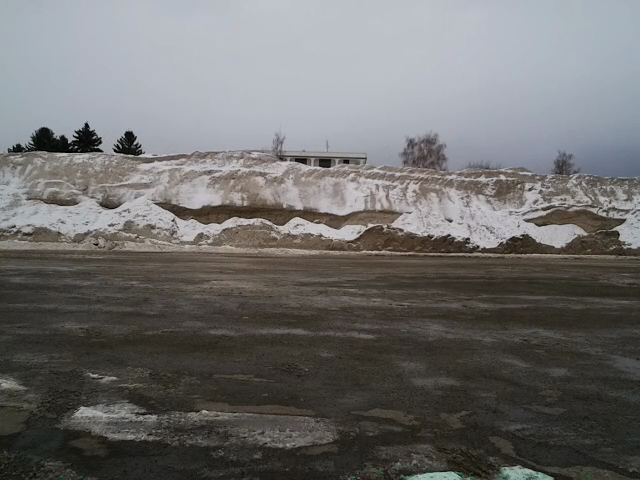
testing/series/frames/frame2_06.png
